RamazanBozkurrtt/circuitBuilderAi-Astra/docs/phases/phase_3g_remaining_schematic_implementation_preflight.md

# PHASE 3G — Remaining schematic implementation preflight

Date: 2026-09-14

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

## 1. Evidence used

Evidence IDs are from the [component evidence index](../evidence/component_evidence_index.md).

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

## 2. Phase 4C blocker disposition

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

## 3. Corrected microphone-to-ADC contract

### 3.1 Physical microphone ownership and polarity

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

### 3.2 Exact microphone-boundary isolation

Use four exact `TMUX1574PWR` TSSOP-16 packages:

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

The corrected isolation population is therefore:

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

### 3.3 Isolation electrical checks

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

### 3.4 Corrected VREF/common-mode path

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

### 3.5 Exact AFE topology and parts

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

For every `MICn_[P/N]_ISO` leg:

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

### 3.6 Worst-case range and headroom

The complete full-band screen uses the direction that maximizes amplitude:

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

Calculations:

`Vin,1k = 10^(-37/20) x 10^(26/20) = 0.281838 Vrms differential`

`Vin,max-band = 0.281838 x 10^(9/20) = 0.794328 Vrms differential`

`VADC,max-band = 0.794328 x 1.454479 = 1.155334 Vrms differential`

`Vleg,pk = 1.155334 / sqrt(2) = 0.816945 V`

`VOUT,min = 1.47 - 0.816945 - 0.002 = 0.651055 V`

`VOUT,max = 1.54 + 0.816945 + 0.002 = 2.358945 V`

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

## 4. Remaining-sheet implementation preflight

### 4.1 Sheet 3 — microphones / AFE

| Audit item | Frozen implementation | Result |
| --- | --- | --- |
| Channel/conductor count | Four differential channels, eight independently named legs; `P` and `N` never share a switch channel. | PASS |
| Isolation count/location | Microphone and AFE/ADC isolation devices are on Sheet 2. Sheet 3 receives eight `MICn_[P/N]_ISO` and returns eight `AFEn_[P/N]_RAW`. | PASS |
| Gain/headroom/common mode | Exact OPAx192 population, 1.453571 nominal gain and OPA320/OPA2192 VCM chain in §3. | PASS |
| LF corner | 4.7 uF nominal, >=2.2 uF effective, 100 kohm; 0.339/0.723 Hz. | PASS |
| Load/stability | `Rg+Rf>=4.066 kohm` and matched 47.0-ohm output isolation; Sheet 4 owns the balanced 1 nF C0G differential ADC capacitors. Macromodel/noise/CMRR tests retained. | PASS for schematic |
| Noise-critical resistors | 100 kohm bias, 2.80 kohm Rg, 1.27 kohm Rf, all 0.1% thin-film; 47 ohm output and Sheet 7 100 ohm RF resistors matched within each pair. | PASS |
| Power-off behavior | Paired-domain powered-off switches; no direct VREF or charged output path across an absent rail. | PASS |
| ADC interface | Eight outputs map one-to-one and polarity-correct to ADAU1978 AIN1-4. | PASS |
| Sheet 3 hierarchy count | **18 scalar pins:** eight mic inputs, eight AFE outputs, `AFE_VCM_ISO`, and `5V_AFE`. Ground is a global power net; no microphone connector is instantiated here. | PASS |

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

### 4.2 Sheet 4 — ADAU1978 ADC

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

### 4.3 Sheet 5 — ADSP-21569 DSP / boot / debug / clocks

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

The resource allocation is frozen and conflict-free:

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

### 4.4 Sheet 6 — TAS6424E-Q1 amplifier

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

### 4.5 Sheet 7 — connectors / system interfaces

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

## 5. Cross-sheet hierarchy inventory

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

| Source | Destination | Signal bundle | Direction | Count |
| --- | --- | --- | --- | ---: |
| Sheet 7 | Sheet 2 | `MIC1..4_[P/N]_RAW` after edge protection/100 ohms | 7 -> 2 | 8 |
| Sheet 2 | Sheet 3 | `MIC1..4_[P/N]_ISO` | 2 -> 3 | 8 |
| Sheet 3 | Sheet 2 | `AFE1..4_[P/N]_RAW` | 3 -> 2 | 8 |
| Sheet 2 | Sheet 4 | `ADC1..4_[P/N]_ISO` | 2 -> 4 | 8 |
| Sheet 4 | Sheet 2 | `ADC_VREF_RAW` | 4 -> 2 | 1 |
| Sheet 2 | Sheet 3 | `AFE_VCM_ISO` | 2 -> 3 | 1 |
| Sheet 2 | Sheets 3/4/5/6/7 | Frozen rails and enables: 5V AFE; 3V3 ADC; DSP rails; 3V3 SYS; 12V protected; 2V8 MIC | 2 -> loads | 8 named rails plus returns |
| Sheet 5 | Sheet 4 | ADC MCLK, BCLK, FSYNC | 5 -> 4 | 3 |
| Sheet 4 | Sheet 5 | ADC TDM data | 4 -> 5 | 1 |
| Sheet 5 | Sheet 6 | amplifier MCLK, SCLK, FSYNC, TDM data | 5 -> 6 | 4 |
| Sheet 5 | Sheets 4/6 | shared SDA, SCL | bidirectional | 2 |
| Sheet 5 | Sheet 2 | six retained-domain commands, MUTE command, STANDBY command, ADC reset-release command, WDI | 5 -> 2 | 10 |
| Sheet 2 | Sheet 5 | `RAILS_OK`, `SYS_HWRST` (dedicated reset, not GPIO) | 2 -> 5 | 2 |
| Sheet 6 | Sheets 2/5 | `AMP_FAULT_N` fanout | 6 -> 2 and 5 | 1 source, 2 sinks |
| Sheet 6 | Sheet 5 | `AMP_WARN_N` | 6 -> 5 | 1 |
| Sheet 6 | Sheet 7 | four filtered BTL `SPKn+/-` pairs | 6 -> 7 | 8 |
| Sheet 5 | Sheet 7 | UART TX/RX/RTS/CTS | mixed | 4 |
| Sheet 5 | Sheet 7 | JTAG TMS/TCK/TDO/TRST/TDI | mixed | 5 |
| Sheet 2 | Sheet 7 | common `SYS_HWRST` branch to JTAG reset contact | 2 -> 7 | 1 |
| Sheet 5 | Sheet 7 | optional service SDA/SCL | bidirectional | 2 |

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

## 6. Remaining non-architectural validation

The following are explicitly **physical-validation items**, not choices left to Astra:

- SPICE/macromodel DC, AC, noise, stability, CMRR and overload recovery for the exact OPA320/OPAx192/switch/ADC network at rail, resistor, temperature and microphone corners.
- Extracted plus measured microphone `Ca`, `Cb`, and `Cd`, each <=100 pF with the production cable/module.
- ADC full-scale/clipping onset because 2 Vrms is published as typical, plus complete channel gain/phase matching.
- ADC data hold timing using exact IBIS/trace extraction and the already frozen >=3 ns measured acceptance criterion.
- DSP rail transient/PI and BGA escape review; decoupling may be augmented within the frozen regulator limits.
- Exact amplifier inductor part, saturation/DCR/temperature, EMI filter optimization, heatsink/interface, load diagnostics and conducted/radiated emissions.
- Exact production connector series, creepage/mechanics, mating-cycle and cable strain relief.

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

## 7. Controlled implementation order

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

## 8. Gate

Both Phase 4C blockers are resolved. Every remaining sheet has a fixed component/interface/safe-state contract, the four-channel DSP resource map has no collision, connector counts include required returns/shields, and the remaining unknowns are physical validation or mechanical procurement items rather than schematic-architecture blockers.

PHASE 3G: PASS
