RamazanBozkurrtt/circuitBuilderAi-Astra/docs/product/ANC_B2B_Custom_PCB_2_Kart_Mimari_Tasarim_Dokumani_v1.0.docx

ANC B2B CUSTOM PCB

İki Kartlı Ürün Mimarisi
ve Tasarım Gereksinimleri

Controller + Audio AFE / Power + Stereo Class-D

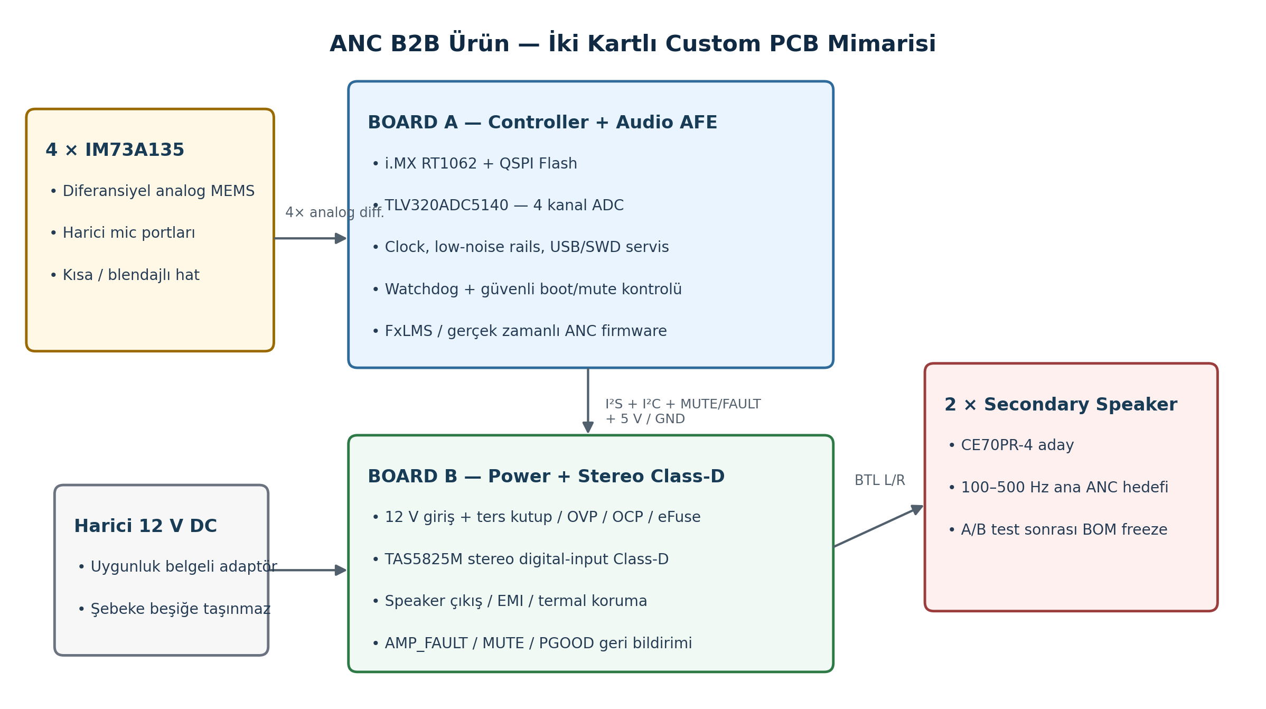
[picture p1: figure]

Doküman statüsü — Bu belge üretim dosyası değildir. Şema/PCB tasarımını yönetecek sistem mimarisi, güvenlik, arayüz, DFM ve doğrulama gereksinimlerini dondurmak için hazırlanmış taslak tasarım girdisidir.

Sürüm: v1.0 Draft | Tarih: 26 Eylül 2026 | Hedef: B2B gömülü ANC modülü

# 1. Amaç, kapsam ve ürün sınırı

Bu dokümanın amacı, mevcut Teensy 4.1 + iki Audio Shield + ayrı Class-D amplifier kartlarıyla kurulan PoC mimarisini, seri üretime uygun iki parçalı custom PCB platformuna dönüştürmek için teknik gereksinimleri tanımlamaktır.

Hedef, PoC kartlarını PCB üzerinde birebir kopyalamak değildir. Hazır geliştirme kartlarının yalnızca ürün için gerekli işlevleri korunur; microSD, headphone jack, kullanıcı potansiyometreleri, geliştirme amaçlı geniş header alanları ve final B2B ürününde kullanılmayan test çıkışları kaldırılır.

Ana ürün kararı — v1 ürün iki karttan oluşacaktır: Board A = Controller + Audio AFE; Board B = Power + Stereo Class-D. Dört mikrofon giriş kanalı ve iki secondary speaker çıkışı korunur. Ürünün ilk ticari odağı B2B gömülü entegrasyondur.

Kaynak proje belgeleri

- ANC_PoC_FINAL_Rev2(1).docx — mevcut PoC kanal planı, güç ve bring-up baseline.
- ANC_Ürünleşme_Sertifikasyon_Doküman.docx — güç, EMC, akustik emniyet, EVT/DVT/PVT ve teknik dosya gereksinimleri.
- ANC_Besik_Kompakt_Hoparlor_Adaylari_Arastirma_Raporu(1).docx — kompakt secondary speaker seçimi ve A/B test planı.
- ANC_Besik_Potansiyel_Musteri_Analizi_2026-09-16(1).docx — B2B gömülü ürün yaklaşımının ticari bağlamı.

1.1 Dondurulan ve açık bırakılan kararlar

Konu | Durum | v1 kararı | Not
Mimari | DONDURULDU | 2 kartlı stack | AFE/digital ile Class-D/power fiziksel olarak ayrılır.
Mikrofon | HEDEF | 4 × IM73A135 | Analog diferansiyel; exact input network şema aşamasında doğrulanır.
ADC | HEDEF | TLV320ADC5140 | 4 analog kanal, TDM/I²S; düşük gecikme ayarı doğrulanır.
MCU/DSP | HEDEF | i.MX RT1062 | Teensy 4.1 işlevlerinin gerekli kısmı doğrudan MCU üzerinde.
Amplifier | HEDEF | TAS5825M | 2 kanal digital-input Class-D; 12 V performansı EVT’de doğrulanır.
Speaker | ADAY | 2 × Dayton CE70PR-4 | Seri BOM, gerçek beşik A/B testinden sonra dondurulur.
Kablosuz | v1 DIŞI | Yok | RED kapsamını ve maliyeti gereksiz büyütmemek için.
microSD / headphone | KALDIRILDI | Yok | Ürün işlevi değil.
Boot/update | AÇIK | Kendi production flow’u tercih | Teensy uyumluluğu otomatik değildir; ayrıca kararlaştırılmalı.

# 2. Sistem mimarisi

Şekil 1 — Önerilen ürün mimarisi. Board A düşük seviyeli analog ve DSP işlerini; Board B yüksek akım, giriş koruması ve speaker sürüşünü taşır.

2.1 Ürün sinyal zinciri

4 × IM73A135 → analog diferansiyel giriş → TLV320ADC5140 → TDM/I²S → i.MX RT1062 / FxLMS → stereo I²S → TAS5825M → 2 × secondary speaker

- PoC’de kullanılan MAX4466 modülleri final üründe kaldırılır. Mikrofon kapsülleri doğrudan ürün AFE’sine bağlanır.
- PoC’deki iki SGTL5000 / iki Audio Shield kaldırılır. Dört giriş için tek çok kanallı ADC kullanılır.
- Digital-input Class-D kullanıldığı için ürün zincirinde ayrı bir stereo DAC zorunlu değildir.
- PoC’deki primary/noise speaker ve spare output final B2B cihaz işlevi değildir; üretim BOM’una eklenmez.
- Dört mikrofonun reference/error/monitoring rolleri mekanik geometri ve algoritma testleriyle atanacaktır; PCB dört eşdeğer giriş kanalı sağlar.

2.2 Fonksiyonel hedefler

Fonksiyon | v1 hedefi | Tasarım sonucu
Mikrofon girişleri | 4 eşzamanlı kanal | Tek ADC, kanal başına eşlenebilir gain/calibration.
Speaker çıkışları | 2 secondary kanal | Tek stereo Class-D.
ANC işleme | Düşük gecikmeli gerçek zamanlı FxLMS | RT1062 üzerinde production firmware.
Programlama/servis | Fabrika ve servis erişimi | USB/SWD/test pad; tüketiciye açık arayüz olmak zorunda değil.
Güvenli durum | Arıza / reset / boot sırasında mute | Hardware mute + watchdog + firmware state machine.
Güç | Harici düşük gerilim DC | Beşik içinde şebeke yok; giriş Board B’de korunur.

# 3. Board A — Controller + Audio AFE

Board A sistemin hassas tarafıdır. Mikrofon analog yolları, ADC, RT1062, flash, clock, servis/debug ve güvenli kontrol mantığı bu kartta bulunur. Class-D güç akımlarından fiziksel olarak uzak tutulur.

3.1 Zorunlu bloklar

- i.MX RT1062 MCU/DSP: mevcut Teensy 4.1 tabanlı gerçek zamanlı ANC algoritmasının üretim platformu.
- Harici QSPI NOR Flash: boot/application image ve gerekirse kalibrasyon verisi.
- TLV320ADC5140: dört analog mikrofon kanalının eşzamanlı örneklenmesi; TDM/I²S ile MCU bağlantısı.
- 4 × IM73A135 giriş portu: diferansiyel mikrofon hatları, ESD/EMI yaklaşımı ve gerekli AC-coupling/bias network.
- Düşük gürültülü analog besleme ve ayrı dijital regülasyon/filtreleme.
- Clock/reset/boot strap devresi; production boot ve recovery yolu.
- Hardware watchdog; amplifier MUTE/ENABLE hattını güvenli durumda zorlayabilecek fail-safe kontrol.
- USB servis/programlama ve SWD/JTAG test padleri; production pogo fixture ile erişilebilirlik.
- Kart kimliği / revision / seri numarası için EEPROM gerekmiyorsa flash alanı kullanılabilir; gereksiz IC eklenmez.

Mikrofon AFE notu — IM73A135 diferansiyel analog çıkışlıdır. TLV320ADC5140 analog/diferansiyel giriş destekler; ancak coupling, common-mode, gain, bias, headroom ve anti-alias network değerleri iki parçanın datasheet/referans devreleri birlikte incelenerek şema aşamasında doğrulanacaktır. Bu doküman o değerleri dondurmaz.

3.2 Board A PCB hedefi

Başlık | Öneri / gereksinim
Katman | Başlangıç hedefi 6 layer. EVT sonrası DFM/EMC sonucu uygunsa 4 layer cost-down değerlendirilebilir.
Yerleşim | Mic AFE + ADC bölgesi, RT1062/flash/clock bölgesinden ve board-to-board power girişinden ayrılır.
Ground | Kesintisiz referans plane; analog/digital dönüş yolları geometrik olarak yönetilir, keyfi split ground yapılmaz.
High-speed | QSPI, USB ve clock hatları kontrollü ve kısa; BGA breakout üretici DFM kurallarına göre.
Test | Tüm rail, reset, boot, SWD, I²C ve kritik audio clock hatlarında erişilebilir test noktası.
EMC | Harici mic connector girişinde ESD/filtre footprintleri; pre-scan için DNP opsiyonları.

# 4. Board B — Power + Stereo Class-D

Board B yüksek akım ve switching enerjisinin bulunduğu karttır. 12 V ürün girişi, primer koruma, logic rail üretimi ve stereo speaker amplifier aynı kartta tutulur. Board A’ya temiz ve kontrol edilmiş besleme sağlanır.

4.1 Zorunlu bloklar

- 12 V DC giriş konektörü ve doğru akım kapasitesine sahip kablo/harness arayüzü.
- Ters kutup koruması, aşırı gerilim, aşırı akım/kısa devre ve eFuse/elektronik sigorta yaklaşımı.
- 12 V → 5 V yüksek verimli buck; Board A üzerinde gerekli düşük gürültülü LDO’larla nihai rail üretimi.
- TAS5825M stereo digital-input Class-D amplifier; I²S audio ve I²C kontrol.
- Hardware MUTE/ENABLE; MCU arızasında varsayılan mute olacak pull-up/pull-down mantığı.
- AMP_FAULT / thermal / PGOOD geri bildirimleri Board A’ya taşınır.
- Speaker output connectorları, BTL topolojisine uygun; eksi uçlar GND olarak etiketlenmez.
- EMI/output network ve bulk decoupling footprintleri; ölçüm sonrası optimize edilebilir.

4.2 Board B PCB hedefi

Başlık | Öneri / gereksinim
Katman | 4 layer başlangıç hedefi; power/ground plane ve Class-D dönüş yolları için tercih edilir.
Akım döngüleri | PVDD decoupling, half-bridge ve speaker akım döngüleri çok kısa tutulur.
Termal | Exposed pad / thermal via / copper area datasheet’e göre; kapalı muhafaza worst-case test edilir.
Connector | 12 V giriş ve speaker çıkışları mic/AFE yönünün ters tarafına yerleştirilir.
Koruma | Input TVS/eFuse/OVP/OCP ve ESD parçaları konektöre yakın.
Servis | Rail, current sense/PGOOD, amplifier fault ve mute hatlarında test point.

12 V karar kapısı — İlk ürün 12 V hedefiyle tasarlanır; ancak CE70PR-4 ile gerçek beşik geometrisinde gerekli Vrms/Irms, THD ve ANC headroom ölçülmeden besleme kesin dondurulmaz. 24 V’a geçiş yalnız ölçüm ihtiyacı gösterirse değerlendirilir.

# 5. Board-to-board arayüzü ve stack konsepti

İki kartın fiziksel ayrımı yalnız servis kolaylığı için değil, EMC ve analog performans için de kullanılır. Board B’nin Class-D ve DC/DC switching bölgesi Board A mikrofon/ADC tarafının altına doğrudan denk getirilmemelidir.

5.1 Önerilen arayüz sinyalleri

Grup | Sinyaller | Yön | Not
Güç | 5 V, GND × çoklu pin | B → A | Akım ve ground dönüşü için birden fazla pin.
Audio | BCLK, LRCLK, SDOUT, opsiyonel MCLK | A → B | Stereo I²S; exact pinout şema freeze ile.
Control | I²C SDA/SCL | Çift yön | Amplifier configuration / status.
Safety | AMP_MUTE, AMP_FAULT, PGOOD | A↔B | Fail-safe logic seviyeleri güç yokken de tanımlı.
Service | Revision detect / spare GPIO | Çift yön | DNP/gelecek opsiyon; minimum tutulur.

5.2 Mekanik başlangıç hedefi

- Kart boyutları beşik geometrisi görülmeden dondurulmaz. İlk ECAD hedefi aynı dış zarfı paylaşan iki kompakt karttır.
- Board-to-board mezzanine connector; yanlış yönde takmayı fiziksel olarak engelleyen keying tercih edilir.
- Başlangıç stack mesafesi 10–15 mm sınıfında planlanır; en yüksek komponent ve termal hava ihtiyacıyla doğrulanır.
- Mic connectorları Board A’nın bir kenarında, power/speaker connectorları Board B’nin karşı kenarında gruplanır.
- Montaj deliği/standoff düzeni iki kartta ortak datum kullanır; beşik üreticisinin plastik/ahşap taşıyıcısına aktarılabilir.

# 6. Güvenlik ve EMC gereksinimleri

Bu bölüm maliyet düşürmek için kaldırılamayacak gereksinimleri özetler. Bebek ürünü bağlamında DSP yazılımı tek güvenlik katmanı olarak kabul edilmez.

Risk | Donanım / firmware önlemi | Doğrulama
Kontrol kararsızlığı / yüksek SPL | Hardware mute, sabit gain/power sınırı, watchdog, controlled startup | Full-scale ve kararsızlık fault injection + peak/süre ölçümü.
Mic kopuk/kısa/doygun | ADC validity check + anında safe state | Open/short/reverse/clip testleri.
Amplifier/power arızası | eFuse/OCP/OVP, amp thermal/fault, mute | Short-circuit, overload, thermal single-fault.
EMC ile yanlış çıkış | ESD/EMI filtreleme + immunity sırasında fault→mute | Pre-scan + immunity sırasında eşzamanlı audio izleme.
Yanlış adaptör / reset | Input protection, brownout/PGOOD, silent boot | Gerilim sweep, kesinti, hızlı power-cycle.
Kablo/connector | Locking connector, strain relief, BTL işaretleme | Pull test ve yanlış bağlantı senaryoları.

EMC yerleşim kuralları

- Clock/QSPI/USB ve Class-D switching akım döngüleri mic inputlardan uzak tutulur.
- Board A ve Board B arasında ground dönüşü düşük empedanslı ve öngörülebilir olmalıdır; sinyal dönüşleri connector üzerinden kopuk bırakılmaz.
- Harici mic ve power/speaker kabloları pre-scan testinde en kötü gerçek uzunlukla değerlendirilir.
- Ferrite/RC/common-mode filtre için ölçüm sonrası populate edilebilecek DNP footprint alanları planlanır.
- Debug/test konnektörleri final ürün EMI antenine dönüşmeyecek biçimde üretim sonrasında erişim kontrolüyle ele alınır.

# 7. Firmware, boot ve ürün davranışı

RT1062 kullanmak, Teensy 4.1 kartını PCB üzerinde kopyalamak anlamına gelmez. MCU, flash, reset/boot ve programlama zinciri ürün için ayrıca tasarlanır. Teensy uyumluluğu istenirse bootloader/lisans/ek bileşen kararı ayrı bir üretim kararıdır.

7.1 Production firmware state machine

Durum | Davranış
POWER_OFF | Amplifier fiziksel olarak mute/disabled.
BOOT_SAFE | Rail/clock/flash/ADC/amp iletişimi doğrulanır; speaker sessiz.
SELF_TEST | Mic kanal validity, fault pinleri, calibration CRC ve temel limitler kontrol edilir.
READY | ANC enable edilebilir; soft-start uygulanır.
ANC_ACTIVE | Watchdog ve audio health sürekli izlenir.
FAULT_MUTE | Her kritik fault’ta amp mute; otomatik restart yalnız tanımlı policy ile.

7.2 Güncelleme yaklaşımı

- v1 B2B üründe Wi-Fi/Bluetooth OTA zorunlu değildir.
- Factory flashing pogo/SWD veya USB üzerinden yapılır.
- Firmware version, board revision ve calibration version üretim kaydına bağlanır.
- Field update gerekiyorsa yetkili servis/üretici prosedürü tanımlanır; rastgele son kullanıcı update akışı ilk sürümde şart değildir.

# 8. Üretilebilirlik (DFM/DFA) ve 400 adet/yıl planı

Ticari hedef 400 adet/yıl olduğunda üretim dört release halinde 100 + 100 + 100 + 100 yapılabilir. Ancak fiyat avantajını korumak için üreticiyle yıllık hacim taahhütlü blanket order / scheduled release modeli müzakere edilmelidir.

8.1 PCB üretim paketi

- Gerber/ODB++ veya üreticinin tercih ettiği fabrication package.
- BOM: manufacturer + MPN + approved alternate + DNP + lifecycle status.
- CPL / pick-and-place, centroid, rotation doğrulaması.
- Assembly drawing, polarity, critical component notes.
- Stack-up, impedance note, via/finish ve BGA escape gereksinimleri.
- Panelization/fiducial/tooling hole kuralları assembly house ile birlikte dondurulur.
- Programming/test fixture mekanik çizimi ve pogo test-point map.

8.2 Üretim kalite kontrolü

- RT1062 BGA ve QFN/thermal pad komponentler için ilk lotta X-ray inspection.
- AOI + görsel kalite standardı; tombstone, polarity ve solder void riskleri için process feedback.
- Her board setine lot/serial kimliği.
- Approved alternate kullanımı yalnız BOM change control ile.
- RoHS/material declaration ve kritik komponent CoC dokümanları teknik dosyada saklanır.

# 9. Factory EOL test planı

Her ürün seti yalnız “çalışıyor” kontrolüyle değil, otomatik veya yarı otomatik EOL fixture ile temel güvenlik ve kanal fonksiyonlarından geçmelidir.

Test | Yöntem | PASS kriteri | Kayıt
Rail/idle current | Fixture ölçümü | 5 V/3.3 V tolerans içinde, anormal idle yok | V/I
MCU/Flash | Program + CRC | Boot OK, firmware checksum PASS | FW rev/CRC
ADC/I²C | Device ID/config | 4 kanal erişilebilir | PASS/FAIL
Mic channel | Known acoustic/electrical stimulus | Gain/noise/channel map limit içinde | 4ch değer
I²S amp | Digital test tone | L/R doğru kanal, mute çalışıyor | PASS/FAIL
Speaker output | Dummy load veya controlled speaker fixture | Amplitude/THD/fault normal | L/R değer
Watchdog/mute | Fault injection | Belirlenen sürede sessiz duruma geçiş | ms + status
Serial trace | QR/serial scan | Board A/B eşleşmesi kayıtlı | Serial pair

# 10. EVT → DVT → PVT doğrulama planı

Resmi uygunluk testine production tasarımı dondurulmadan girilmez. Önce elektrik/akustik riskleri kapatan mühendislik iterasyonları tamamlanır.

Aşama | Önerilen adet | Ana iş | Çıkış koşulu
EVT-0 | 5–10 set | Power-up, RT1062 boot, ADC 4ch, I²S amp, basic audio loop | Schematic/layout kritik hataları kapanır.
EVT-1 | 10–20 set | Latency, noise floor, thermal, fault/mute, speaker A/B | CE70PR-4/SLS-65 kararı ve power headroom.
PCB v2 / DVT | 20–30 set | EMC pre-scan, ESD, single-fault, full enclosure/crib integration | Design freeze candidate.
PVT | 50–100 set | Gerçek üretim hattı, EOL fixture, yield ve traceability | 400/yıl release planına geçiş.
Production | 100 × 4 release | Blanket order / scheduled build | Her lot EOL + change control.

# 11. Maliyet hedefi ve cost-down sınırı

Aşağıdaki rakamlar tedarikçi teklifi değil, proje hedef zarfıdır. 400 ürün/yıl ve parçaların yıllık hacim üzerinden fiyatlanması varsayımıyla kullanılmalıdır.

Kapsam | Hedef maliyet | Not
2-board assembled PCB set | ~1.700–2.100 TL / ürün | MCU+ADC+amp+power/safety+PCB/SMT; RFQ ile doğrulanır.
4 mic + 2 speaker + harness dahil embedded set | ~3.400–3.700 TL / ürün | 400/yıl optimize hedef; lojistik/garanti koşuluna göre değişir.
Ticari planlama maliyeti | ~4.000 TL / ürün | Garanti/yield/lojistik/finansman tamponu için güvenli planlama rakamı.

Cost-down kuralı — microSD, headphone, potansiyometre, ikinci gereksiz codec, ayrı DAC, development header ve PoC’ye özel primary speaker çıkışı kaldırılır. Buna karşılık eFuse/OVP/OCP, watchdog, mute, ESD/EMI ve EOL test gibi güvenlik/üretim öğeleri cost-down için kaldırılmaz.

# 12. Açık kararlar / tasarım başlamadan kapanması gerekenler

# | Açık karar | Kapanma kriteri

1 | IM73A135 → TLV320ADC5140 exact analog input network | Schematic freeze öncesi bench/reference-circuit validation.
2 | RT1062 boot/programming modeli | Kendi production boot/update flow’u mu, Teensy uyumluluğu mu?
3 | CE70PR-4 vs SLS-65 | Gerçek beşik A/B testi: 80/100/125/160/250/500/800 Hz, THD, excursion, Vrms/Irms.
4 | 12 V amplifier headroom | CE70PR-4 ile hedef attenuation için yeterli mi? Ölçümle dondur.
5 | Board boyutu ve connector | Beşik üreticisinin mekanik hacmi ve kablo rotası geldikten sonra.
6 | Mic role / placement | 4 kanalın reference/error/monitoring dağılımı akustik geometriyle.
7 | Safety SPL acceptance criteria | Bağımsız akustik uzman/lab ile satış öncesi yazılı limit/test metodu.

12.1 İlk PCB tasarım sprinti için önerilen çıktı

- System schematic review: Board A ve Board B sheet breakdown.
- Power tree + reset/boot sequencing diagram.
- 4-channel microphone AFE simulation / bench validation note.
- Board-to-board connector pin assignment v0.1.
- RT1062 pin mux / DMA / SAI / I²C resource map.
- Preliminary BOM + lifecycle + sourcing risk list.
- Placement floorplan before routing: AFE, MCU/flash, connector, DC/DC, Class-D, speaker outputs.
- EVT testpoint ve fixture requirements freeze.

# Ek A — Fonksiyonel preliminary BOM

Bu liste üretim BOM’u değildir; tasarım bloklarını netleştirmek için hazırlanmıştır. Exact MPN, package ve alternatifler schematic/DFM aşamasında dondurulacaktır.

Ref blok | Önerilen parça / sınıf | Adet | Kart | Durum
MCU | NXP i.MX RT1062 | 1 | A | Hedef
Flash | QSPI NOR, yeterli capacity | 1 | A | Açık MPN
Audio ADC | TI TLV320ADC5140 | 1 | A | Hedef
Microphone | Infineon IM73A135 | 4 | Harici / mic PCB | Hedef
Class-D | TI TAS5825M | 1 | B | Hedef
Secondary speaker | Dayton CE70PR-4 | 2 | Harici | A/B test adayı
Power protection | eFuse / OVP / reverse polarity / TVS | 1 set | B | Schematic seçimi açık
DC/DC | 12 V → 5 V buck | 1 | B | Açık MPN
Low-noise rails | LDO / filter network | 1 set | A | Açık MPN
Watchdog | Independent hardware watchdog veya equivalent safety path | 1 | A | Açık MPN
Board connector | Keyed mezzanine | 1 pair | A+B | Mekanik açık
Service | USB/SWD/pogo test interface | 1 set | A | Üretim gereksinimi

# Ek B — Teknik referanslar ve proje dayanakları

- TI TLV320ADC5140 product/data sheet: 4 analog ADC channel, TDM/I²S, programmable gain/low-latency options.
- TI TAS5825M product/data sheet: stereo digital-input Class-D, 4.5–26.4 V PVDD, integrated fault protections.
- Infineon IM73A135 product information: analog differential MEMS microphone.
- Project document: ANC_PoC_FINAL_Rev2(1).docx.
- Project document: ANC_Ürünleşme_Sertifikasyon_Doküman.docx.
- Project document: ANC_Besik_Kompakt_Hoparlor_Adaylari_Arastirma_Raporu(1).docx.

Final not — Bu dokümandan sonraki doğru adım doğrudan routing değildir. Önce Board A/Board B schematic sheet planı, power tree, boot strategy ve IM73A135→ADC input network dondurulmalı; ardından placement floorplan ve PCB layout’a geçilmelidir.

ANC B2B Custom PCB | Taslak v1.0 | 26.09.2026 •

ANC B2B Custom PCB — Two-Board Product Architecture
