RamazanBozkurrtt/circuitBuilderAi-Astra/datasheets/power/amass_xt30pw_spec_0.png

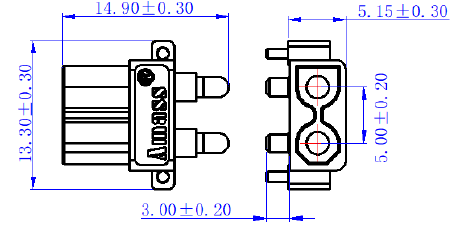
datasheets/power/amass_xt30pw_spec_0.png
