RamazanBozkurrtt/circuitBuilderAi-Astra/tmp/phase_1/ADC_8.png

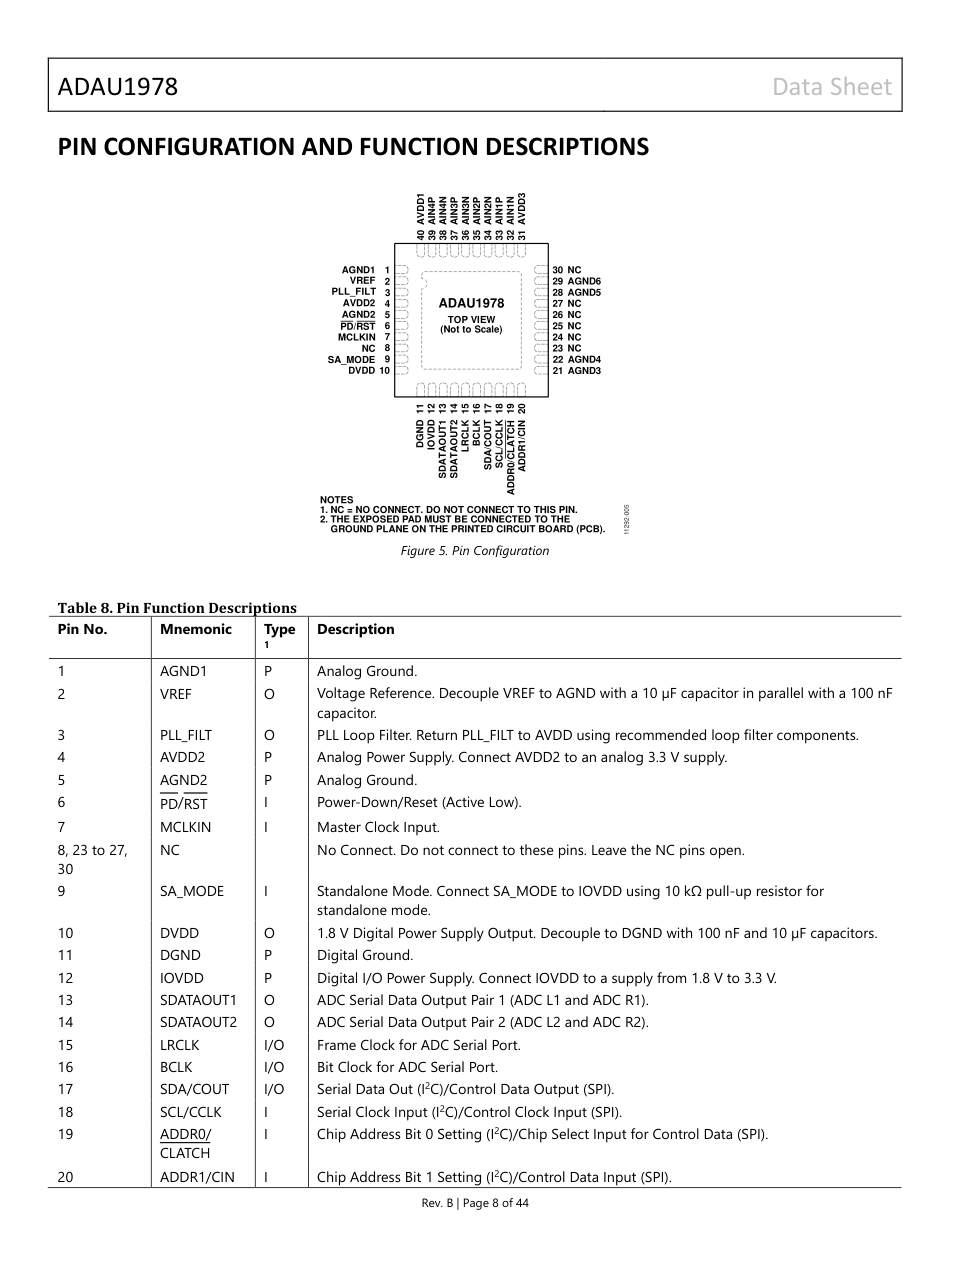
tmp/phase_1/ADC_8.png
