RamazanBozkurrtt/circuitBuilderAi-Astra/tmp/phase_1/ADC_18.png

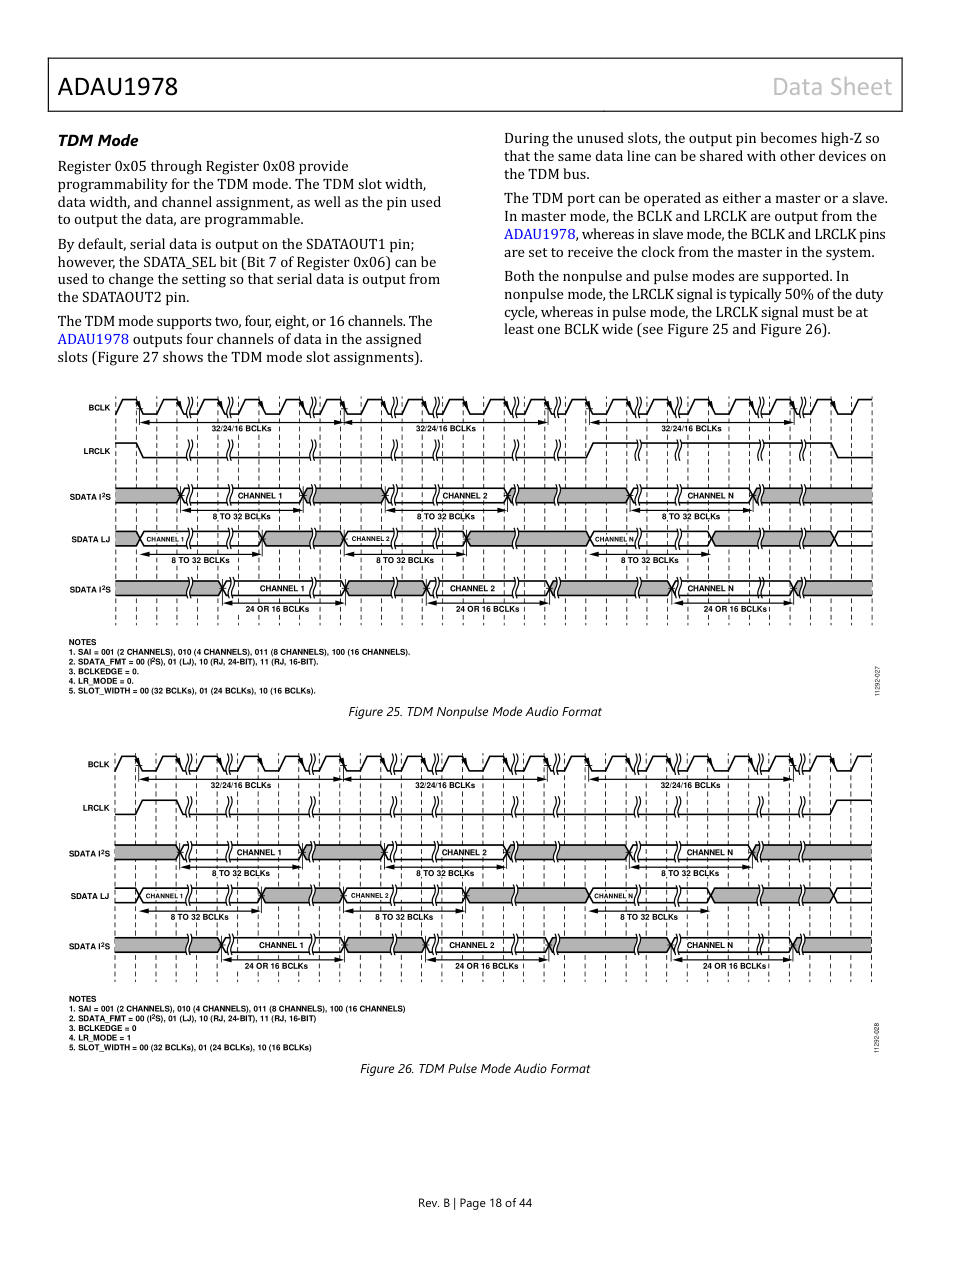
tmp/phase_1/ADC_18.png
