RamazanBozkurrtt/circuitBuilderAi-Astra/tmp/phase_1/ADC_43.png

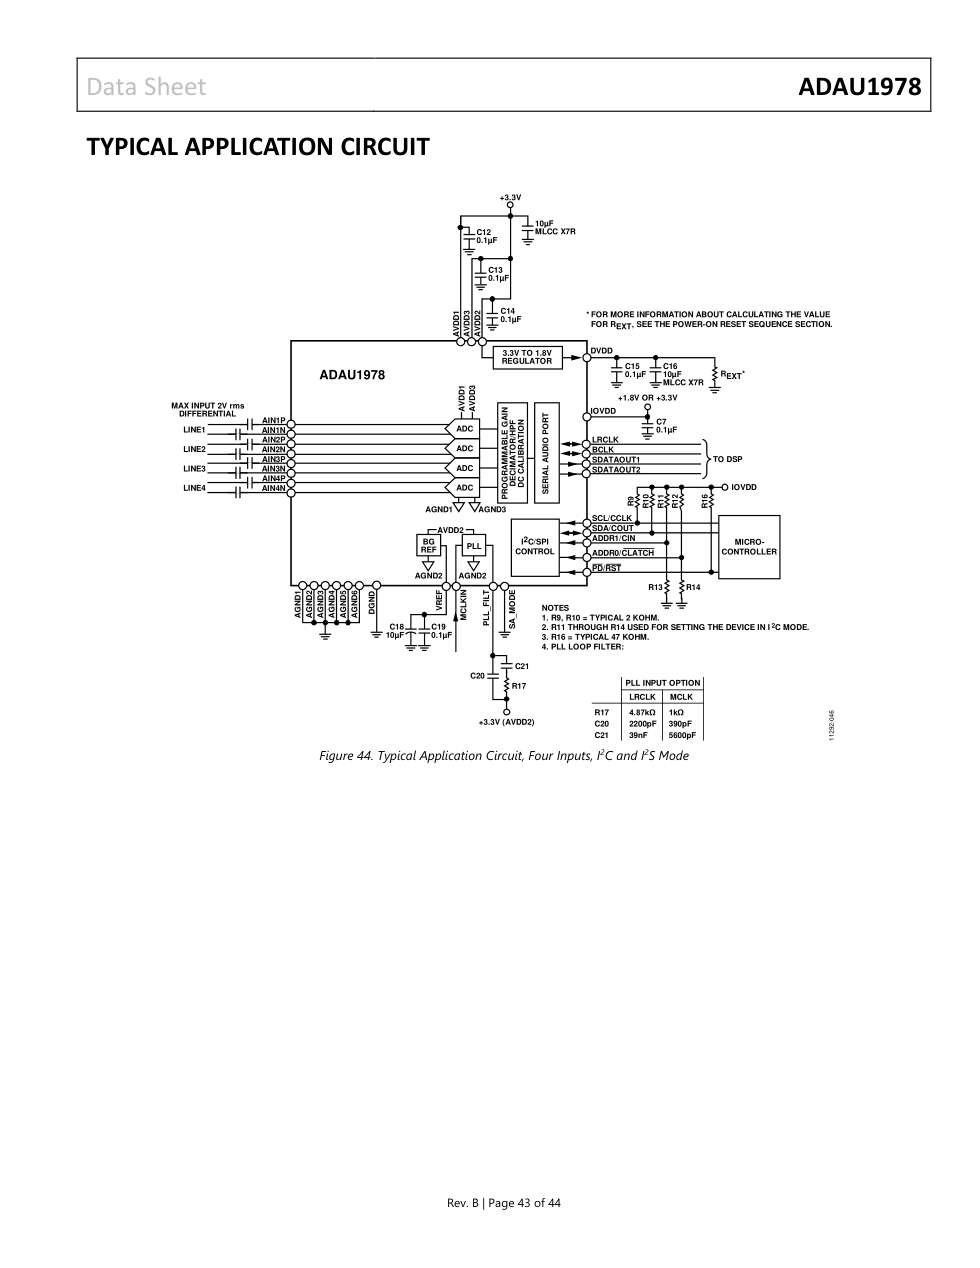
tmp/phase_1/ADC_43.png
