RamazanBozkurrtt/circuitBuilderAi-Astra/tmp/phase_1/ADCEVAL_10.png

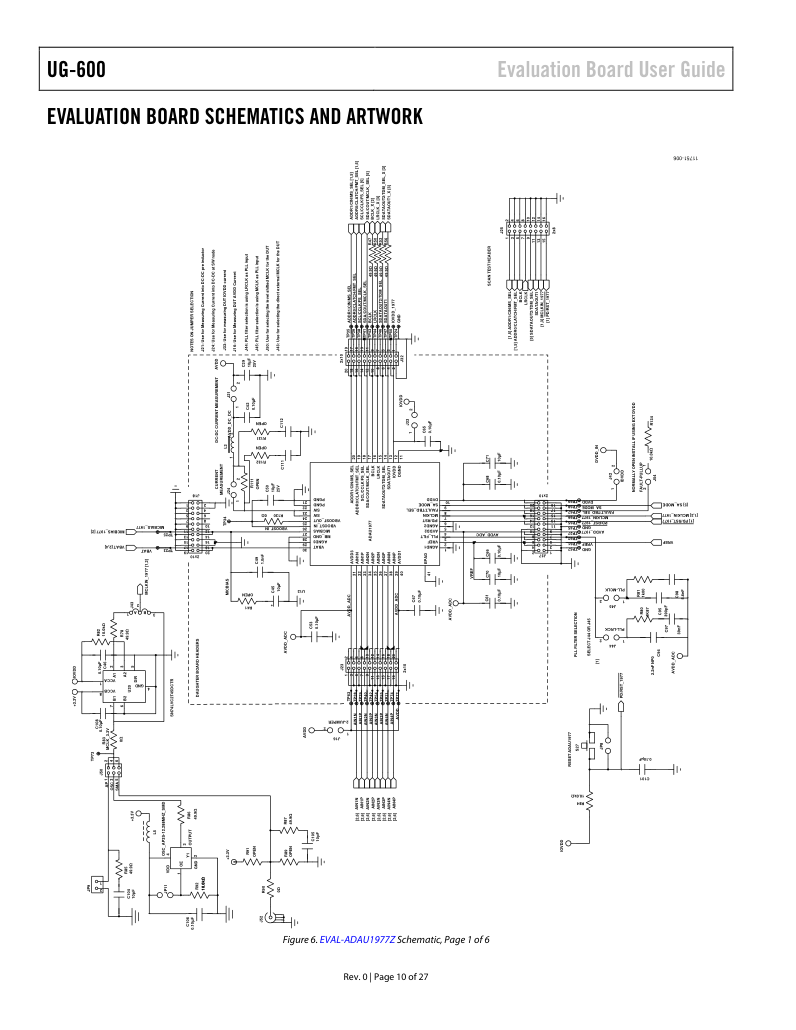
tmp/phase_1/ADCEVAL_10.png
