RamazanBozkurrtt/circuitBuilderAi-Astra/tmp/phase_1/ADCEVAL_11.png

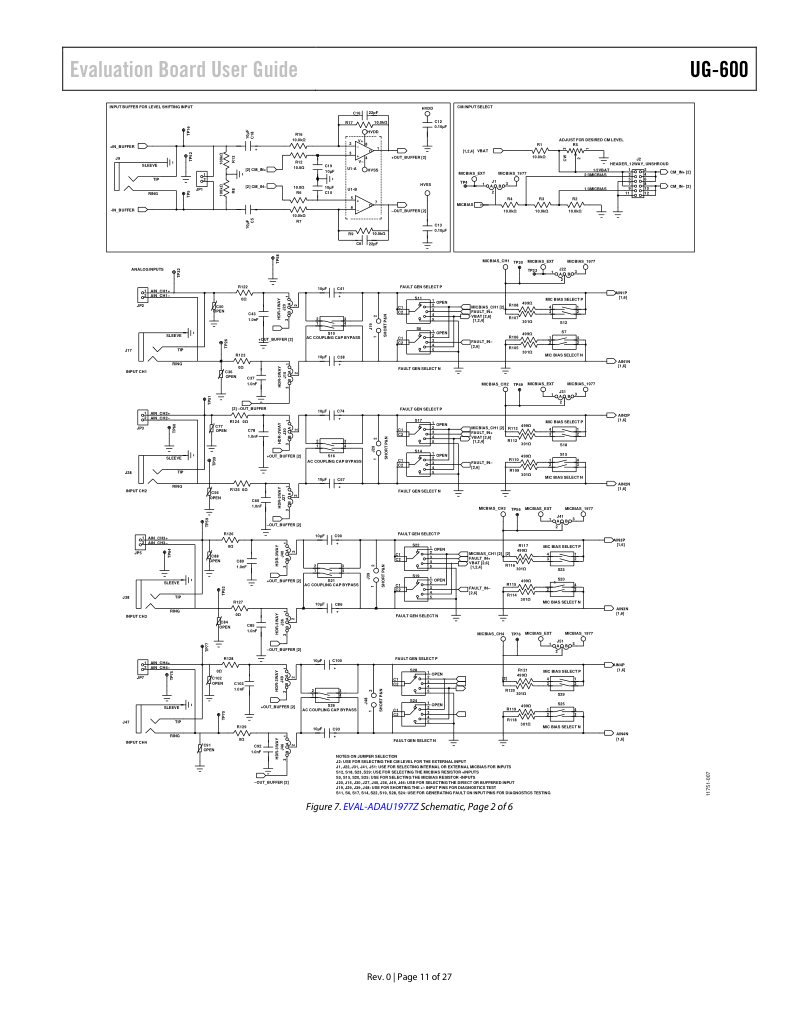
tmp/phase_1/ADCEVAL_11.png
