RamazanBozkurrtt/circuitBuilderAi-Astra/tmp/phase_1/AMP_4.png

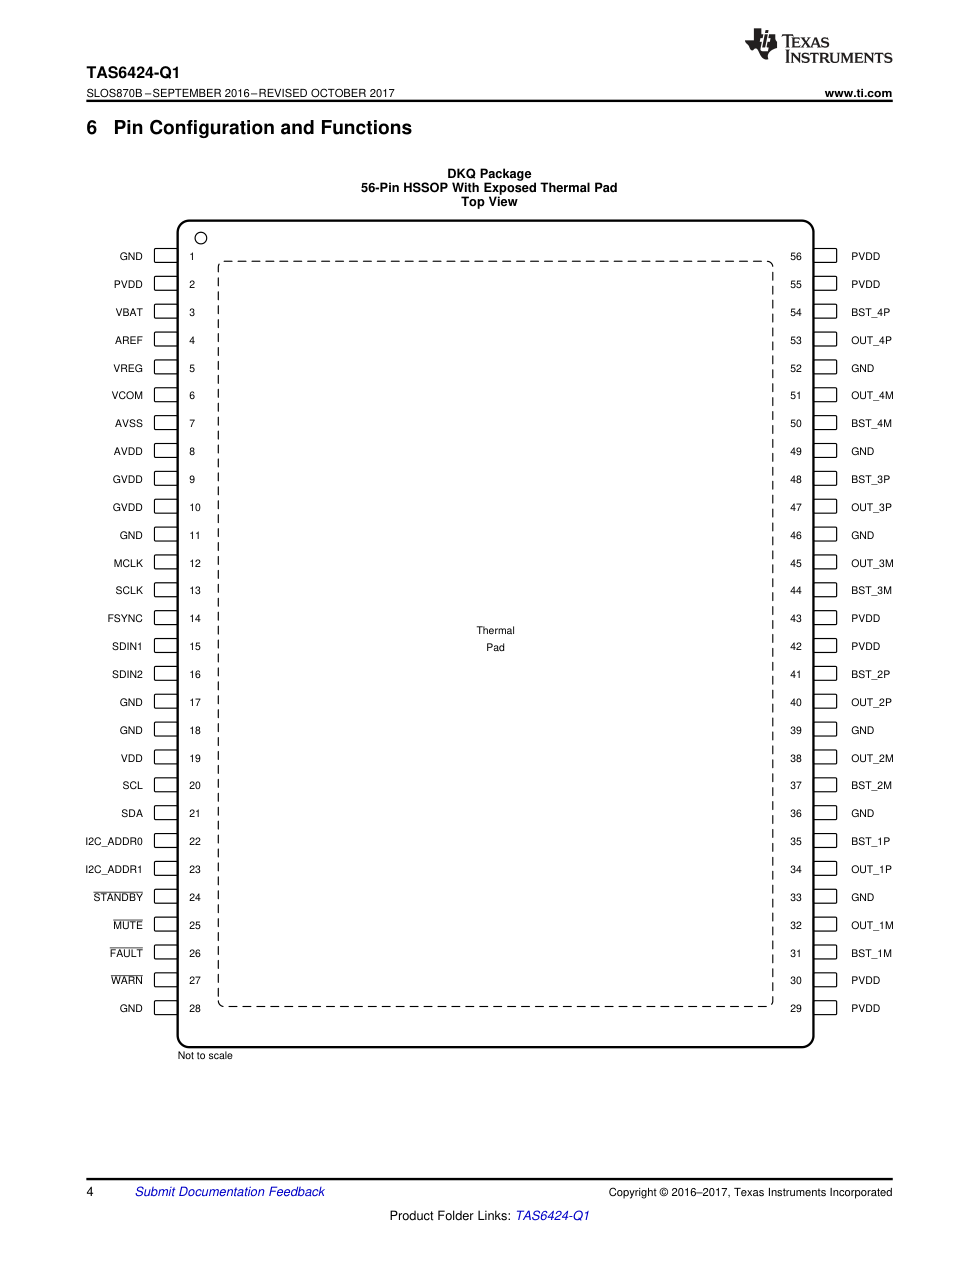
tmp/phase_1/AMP_4.png
