RamazanBozkurrtt/circuitBuilderAi-Astra/tmp/phase_1/AMP_19.png

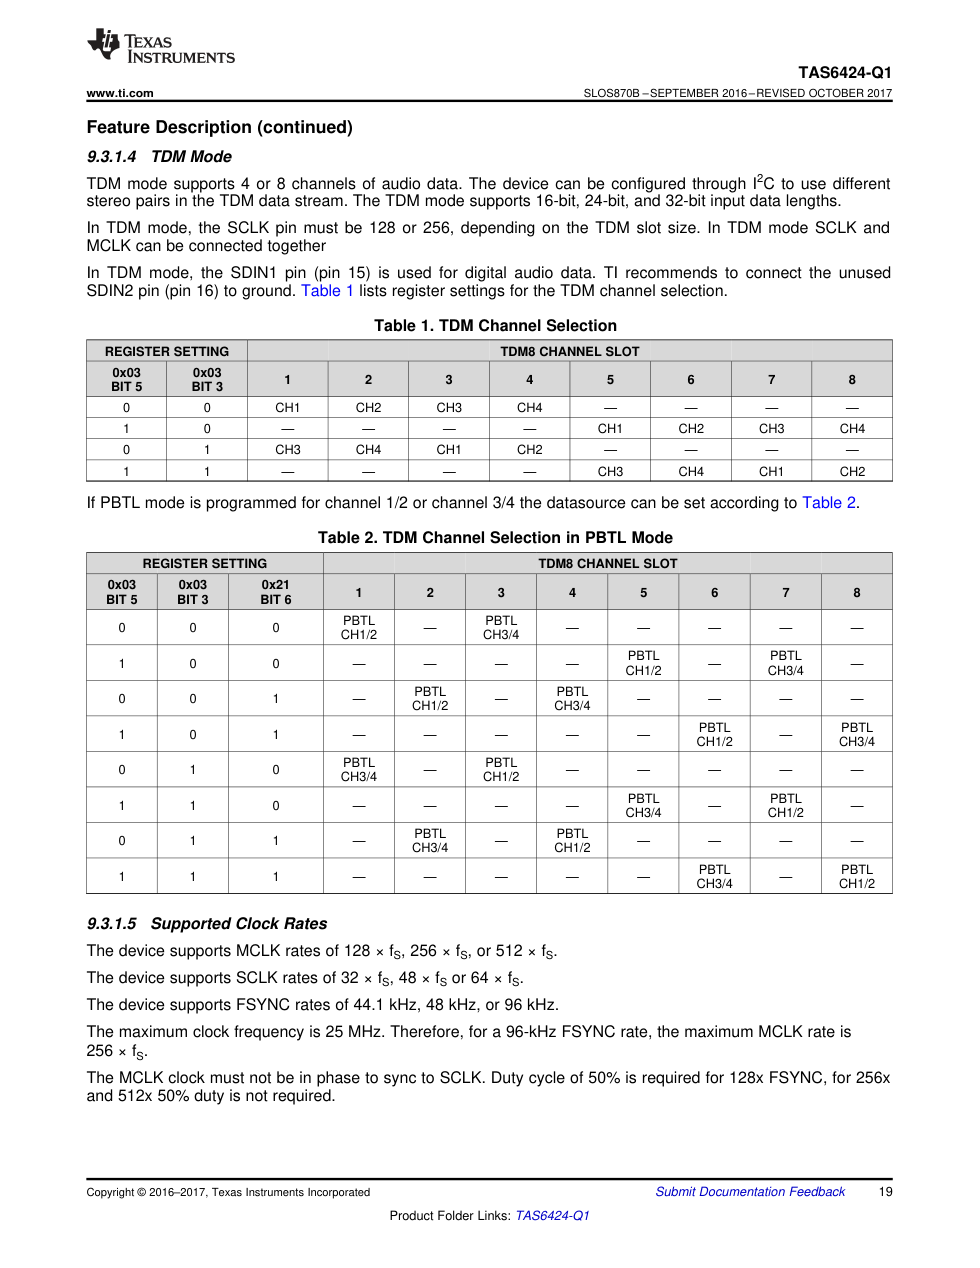
tmp/phase_1/AMP_19.png
