RamazanBozkurrtt/circuitBuilderAi-Astra/tmp/phase_1/AMP_21.png

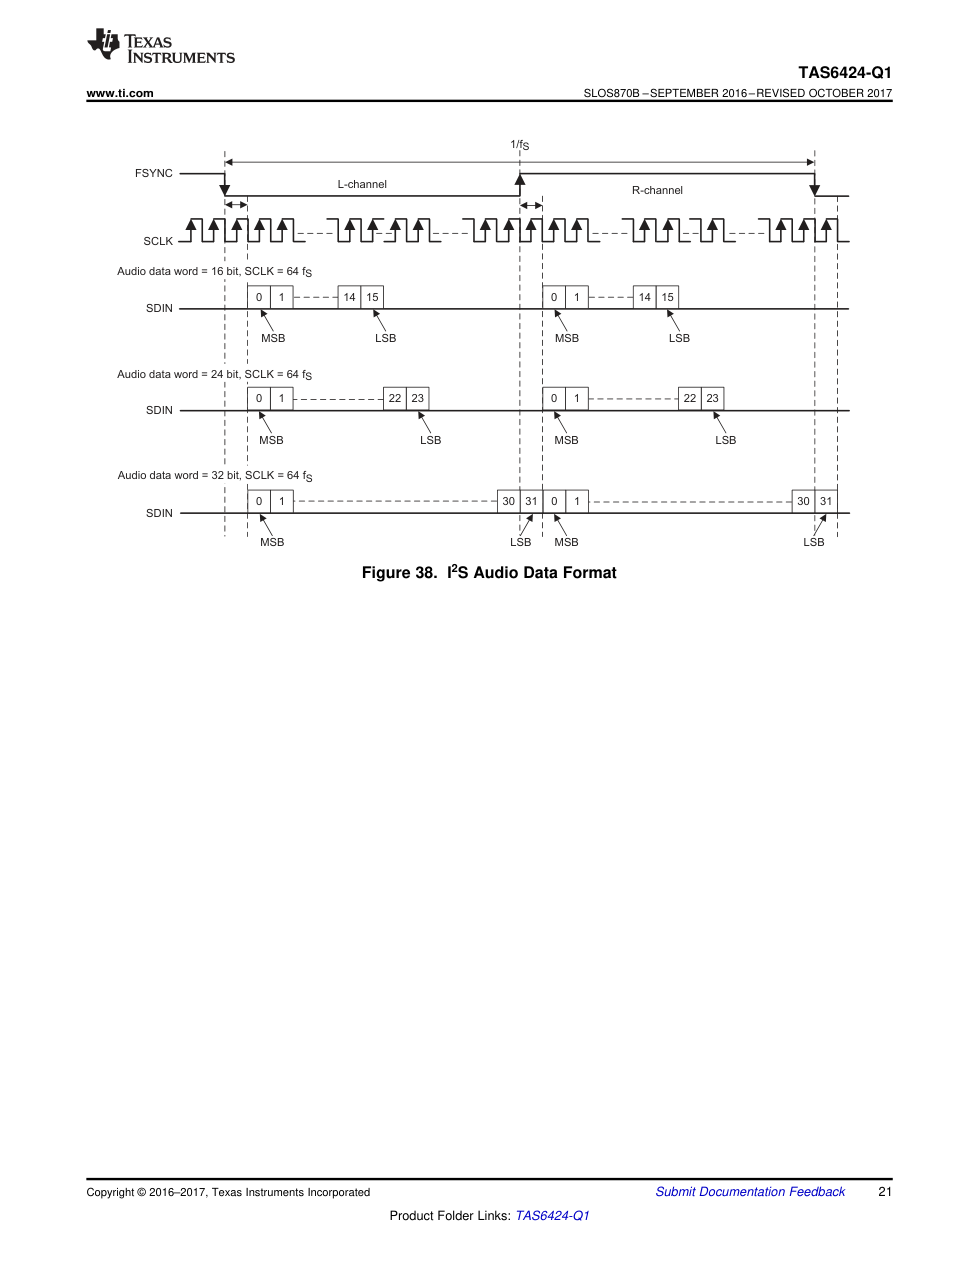
tmp/phase_1/AMP_21.png
