RamazanBozkurrtt/circuitBuilderAi-Astra/tmp/phase_1/AMP_22.png

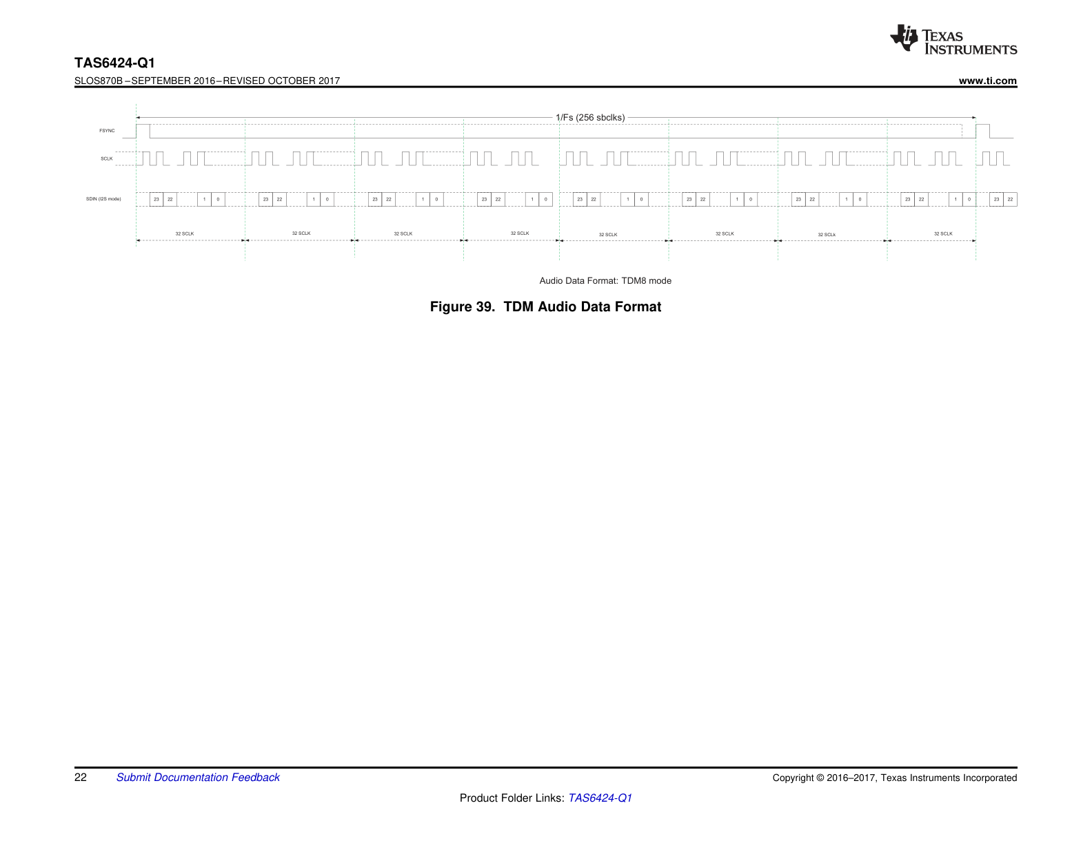
tmp/phase_1/AMP_22.png
