RamazanBozkurrtt/circuitBuilderAi-Astra/tmp/phase_1/AMP_34.png

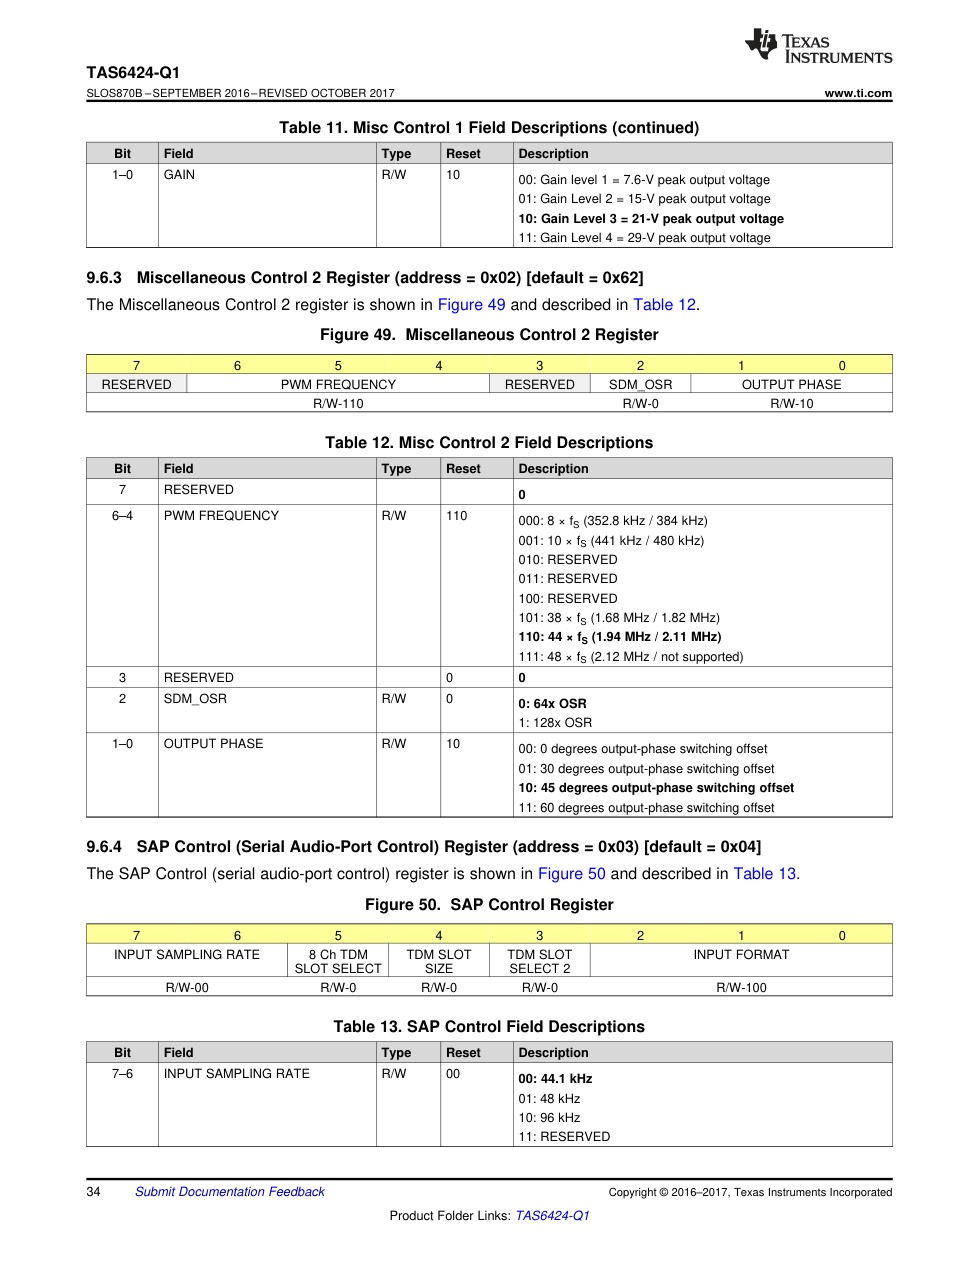
tmp/phase_1/AMP_34.png
