RamazanBozkurrtt/circuitBuilderAi-Astra/tmp/phase_1/AMPEVAL_23.png

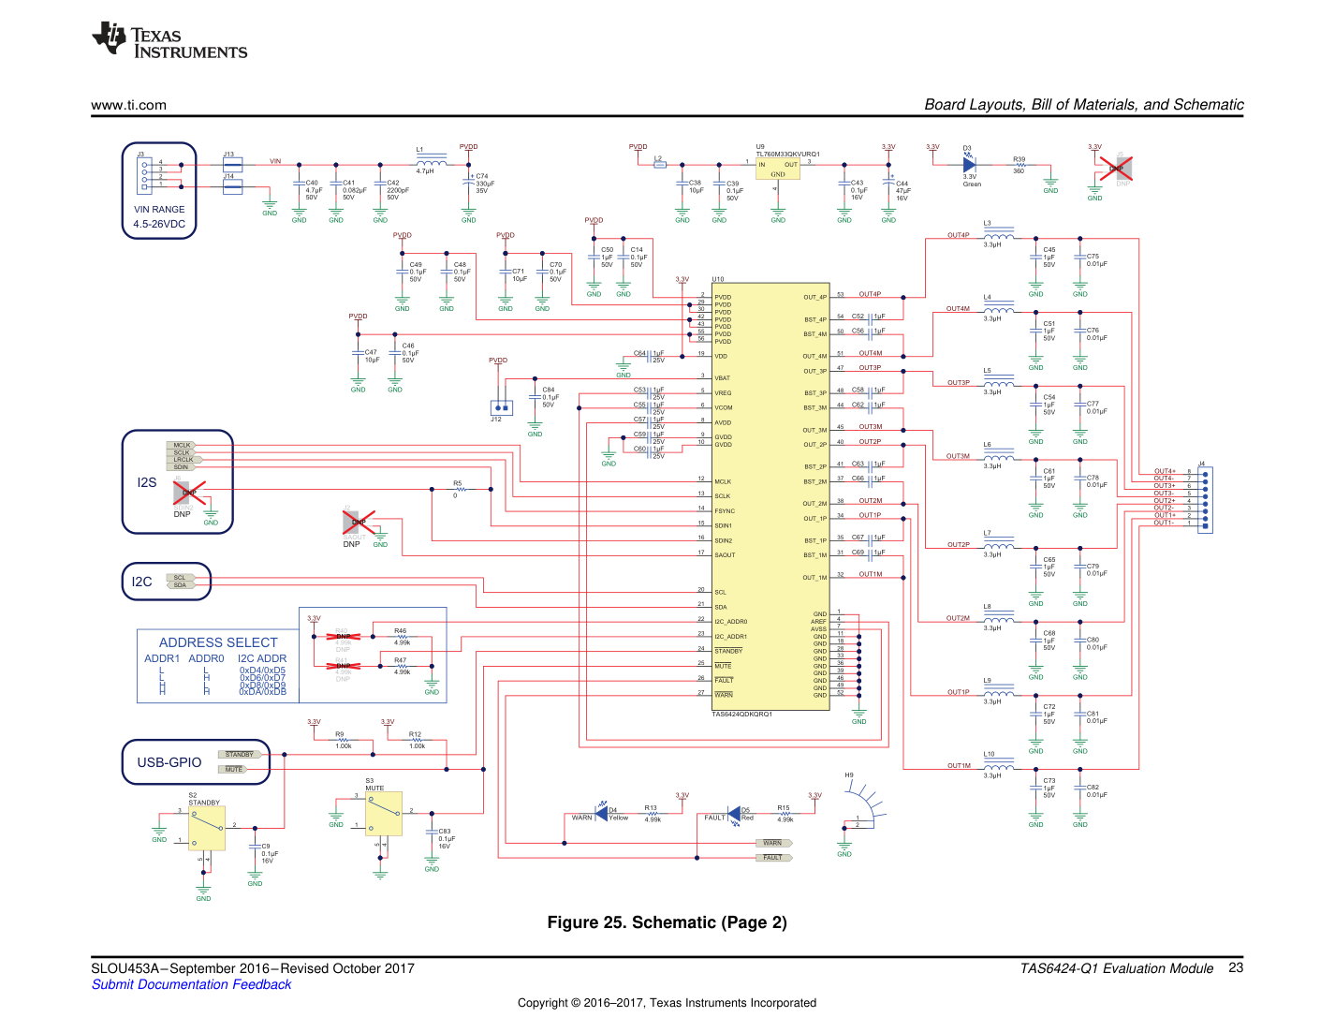
tmp/phase_1/AMPEVAL_23.png
