RamazanBozkurrtt/circuitBuilderAi-Astra/tmp/phase_1/AMPEVAL_27.png

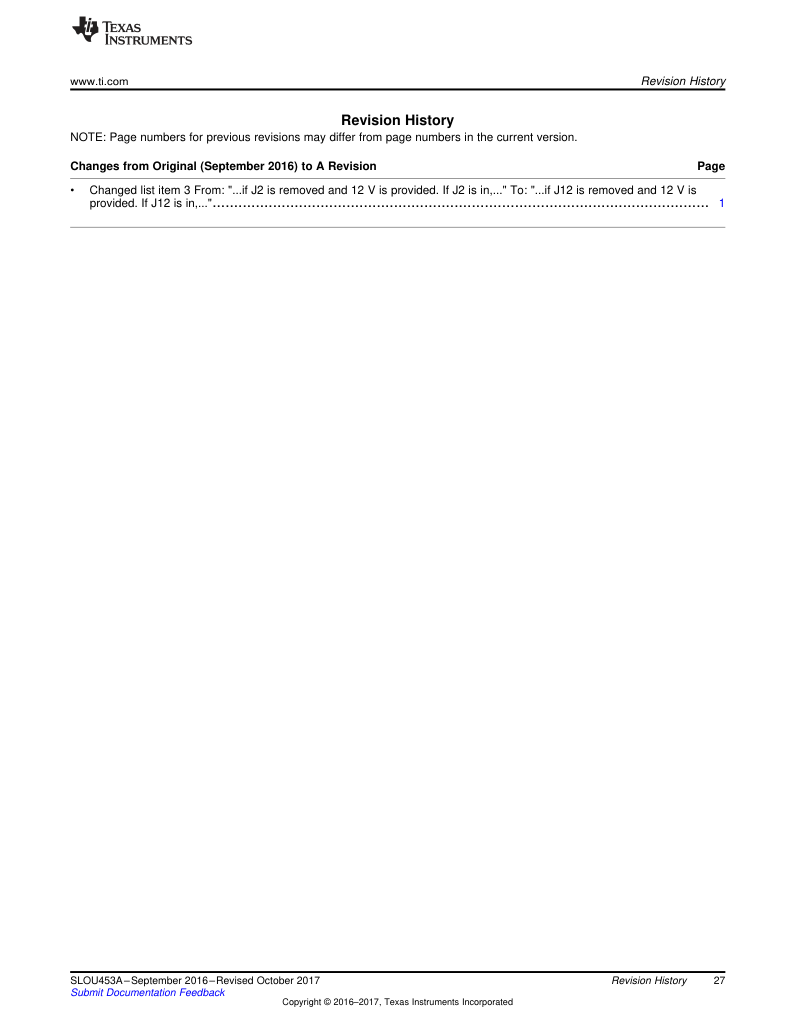
tmp/phase_1/AMPEVAL_27.png
