RamazanBozkurrtt/circuitBuilderAi-Astra/tmp/phase_1/AMPEVAL_28.png

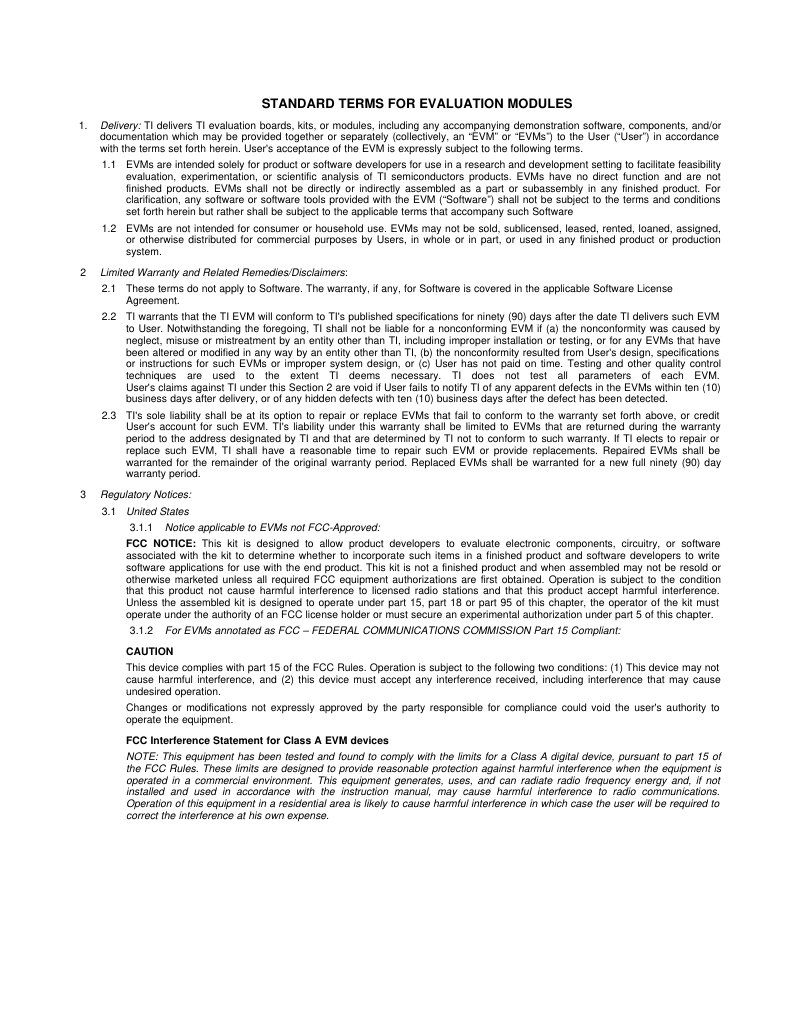
tmp/phase_1/AMPEVAL_28.png
