RamazanBozkurrtt/circuitBuilderAi-Astra/tmp/phase_1/DSP_89.png

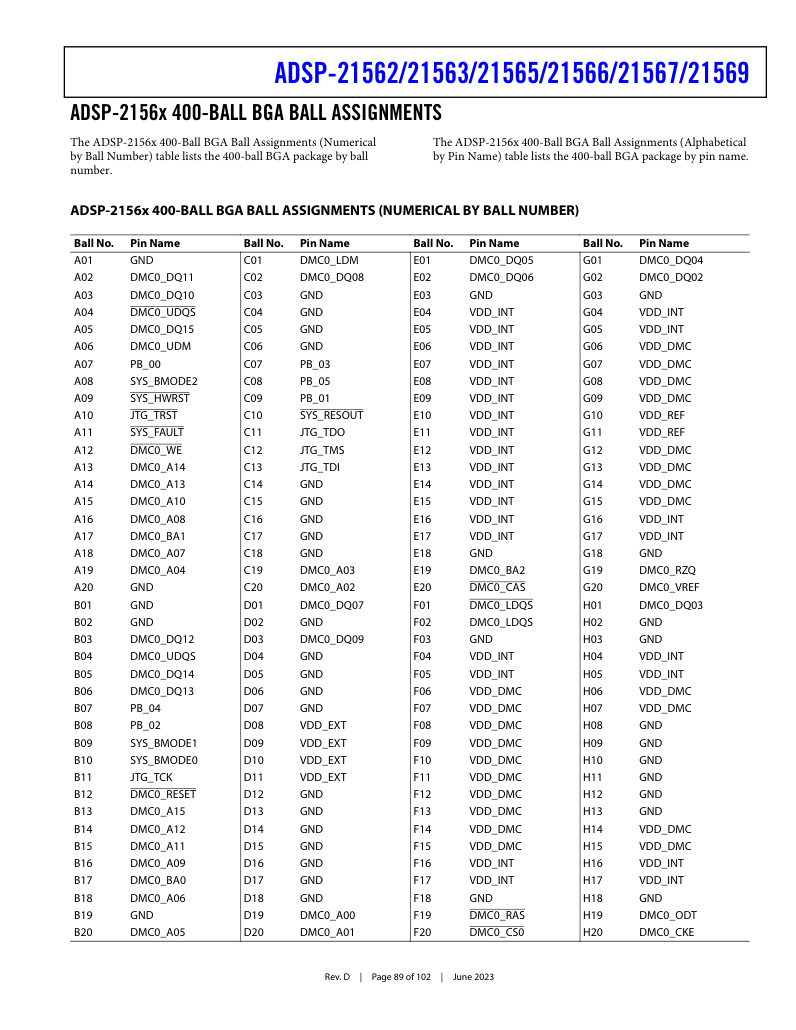
tmp/phase_1/DSP_89.png
