RamazanBozkurrtt/circuitBuilderAi-Astra/tmp/phase_1/DSP_90.png

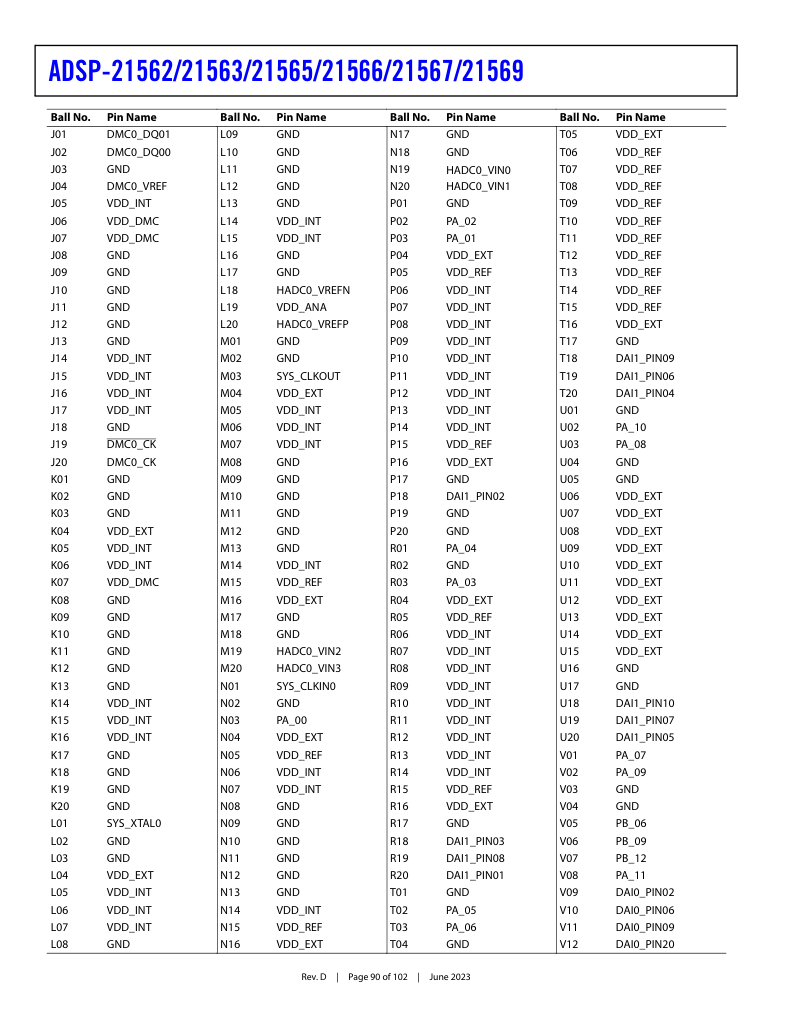
tmp/phase_1/DSP_90.png
