RamazanBozkurrtt/circuitBuilderAi-Astra/tmp/phase_1/DSP_91.png

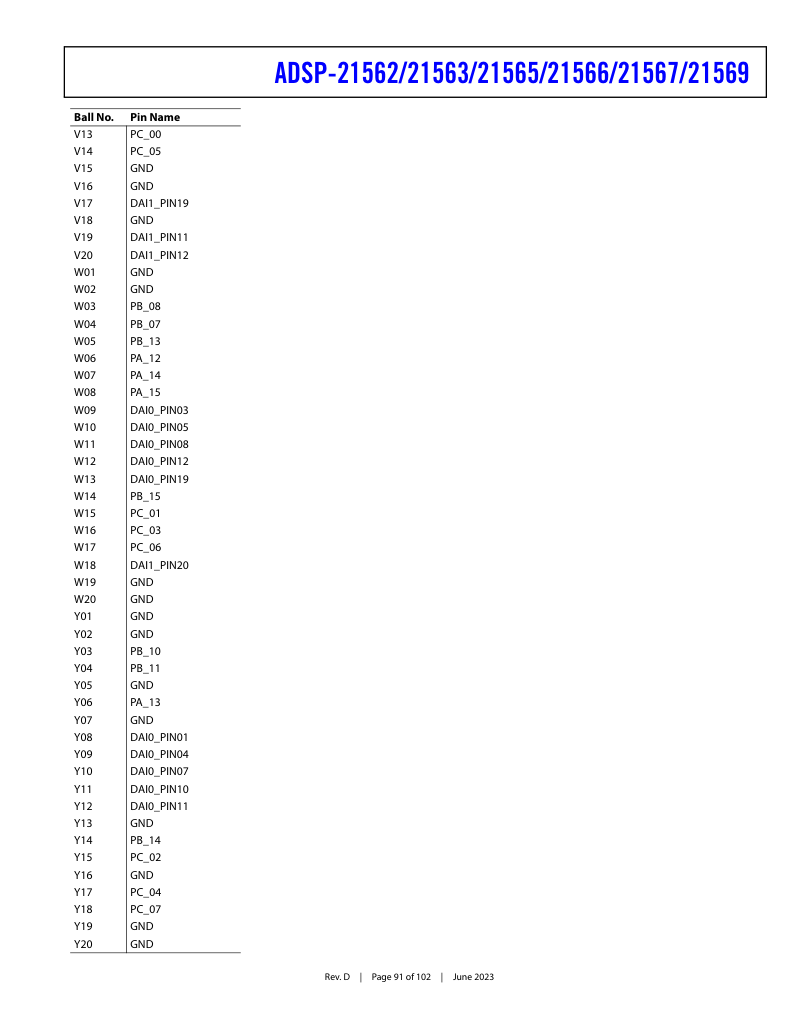
tmp/phase_1/DSP_91.png
