RamazanBozkurrtt/circuitBuilderAi-Astra/tmp/phase_1/MIC_8.png

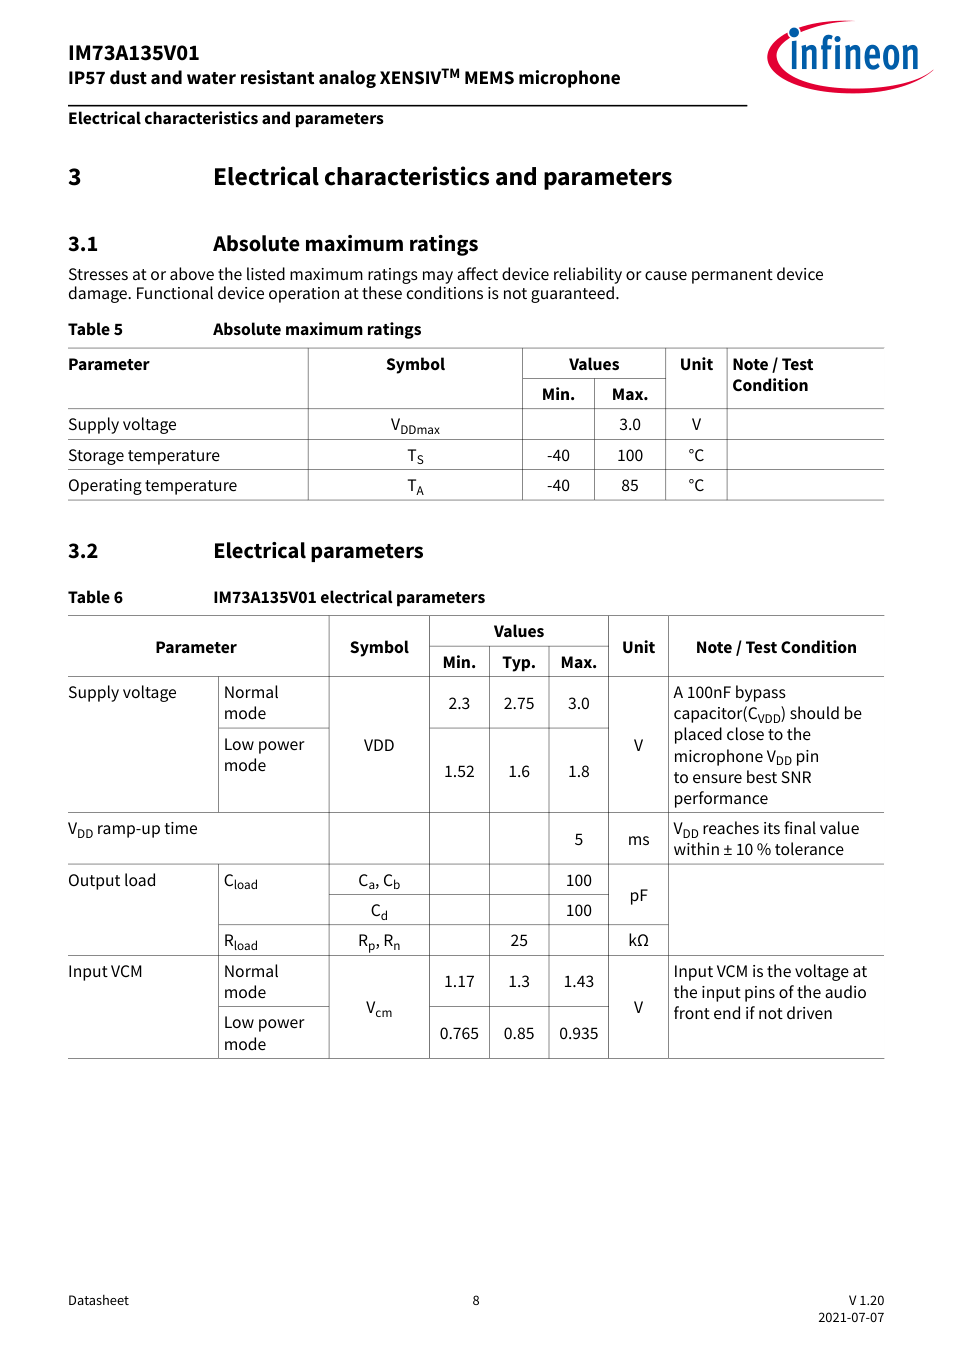
tmp/phase_1/MIC_8.png
