RamazanBozkurrtt/circuitBuilderAi-Astra/tmp/phase_1/MIC_9.png

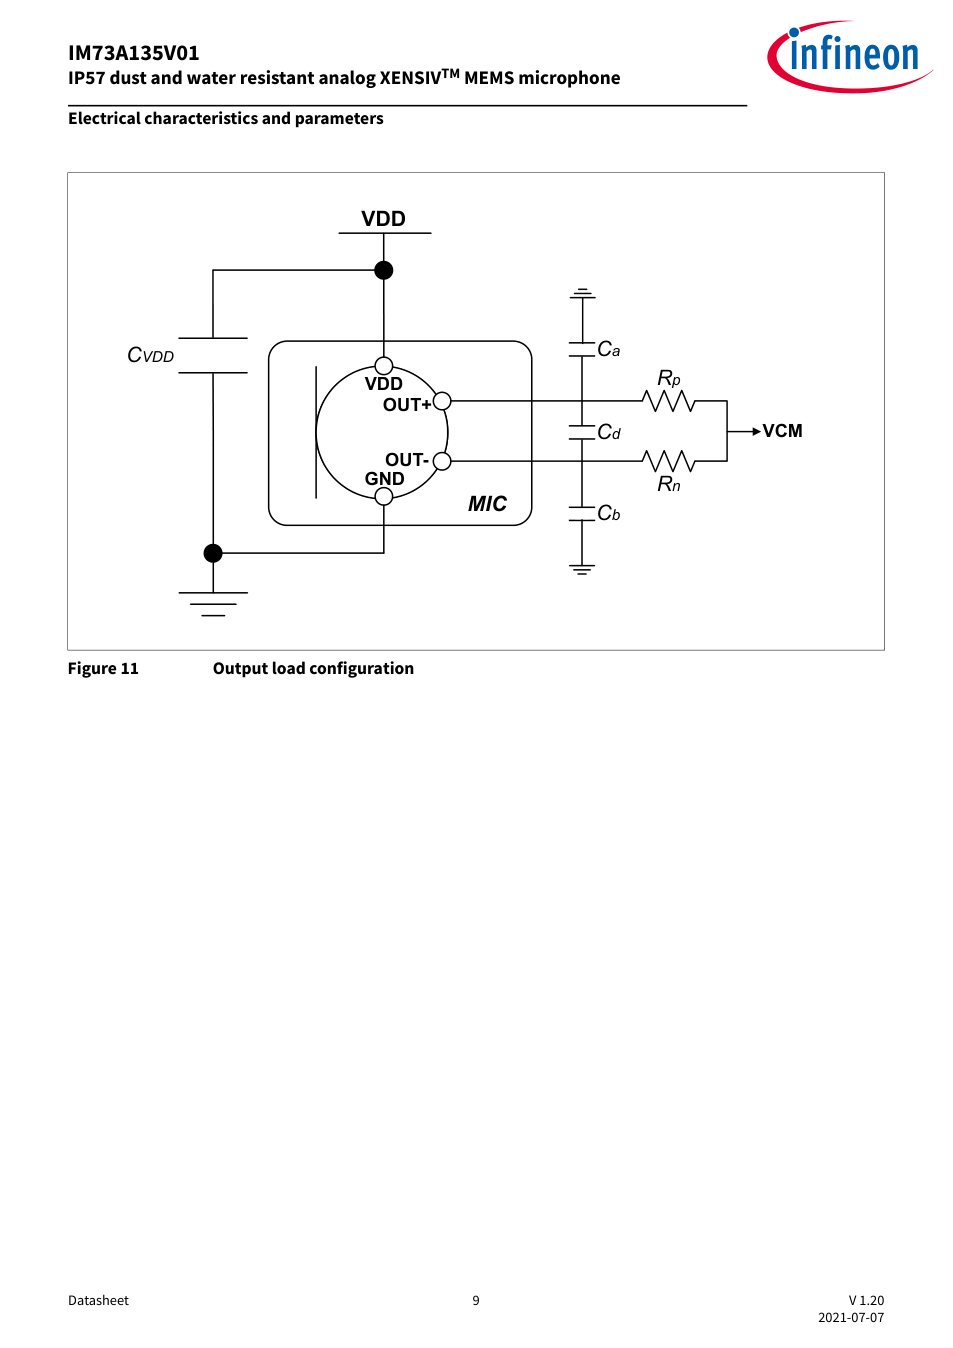
tmp/phase_1/MIC_9.png
