RamazanBozkurrtt/circuitBuilderAi-Astra/tmp/phase_1/MIC_10.png

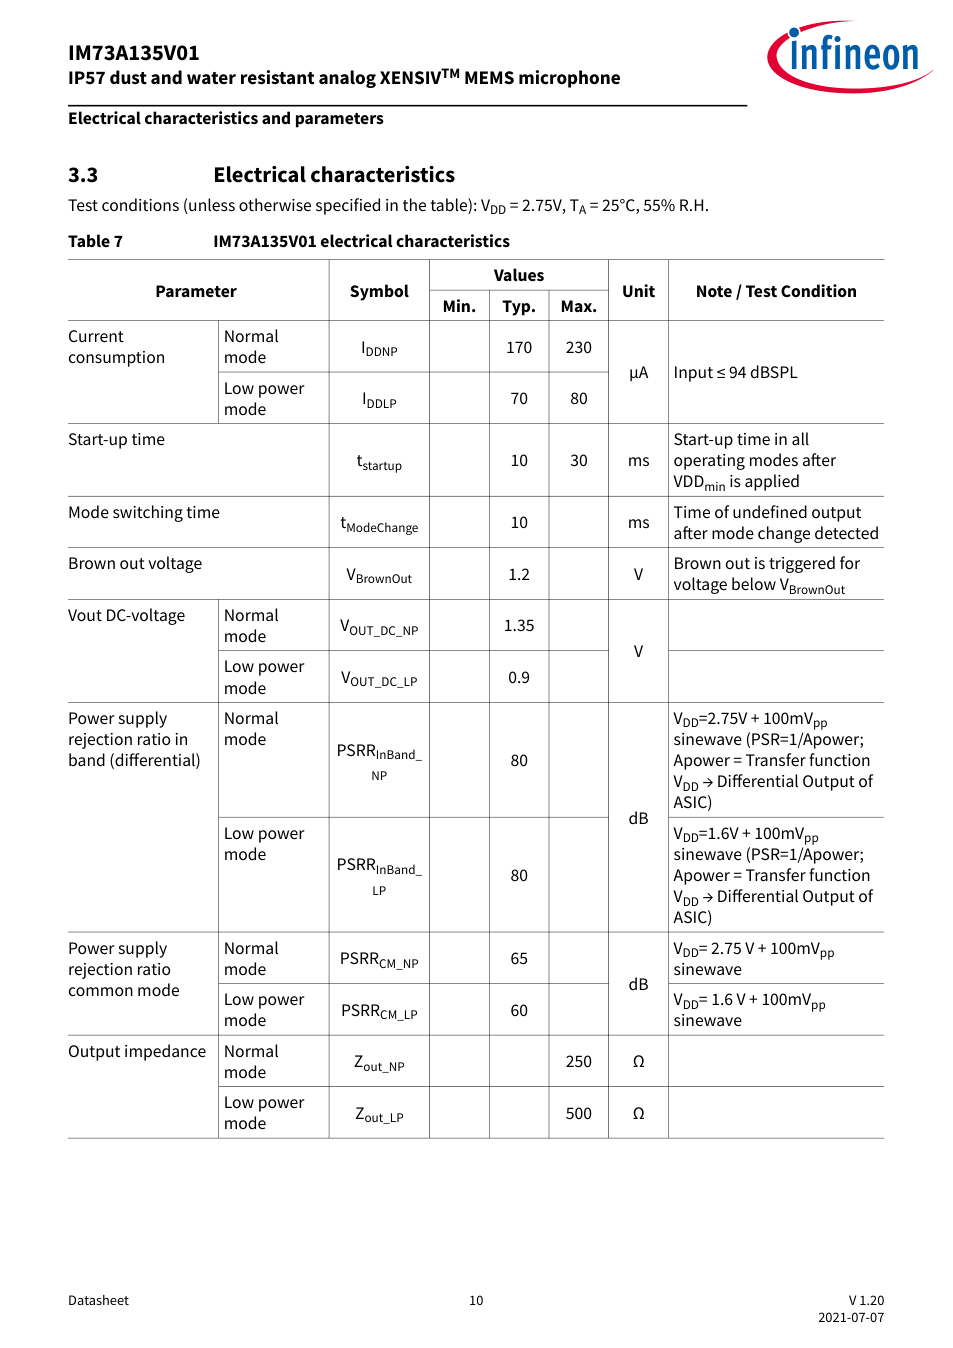
tmp/phase_1/MIC_10.png
