RamazanBozkurrtt/circuitBuilderAi-Astra/tmp/phase_1/MIC_11.png

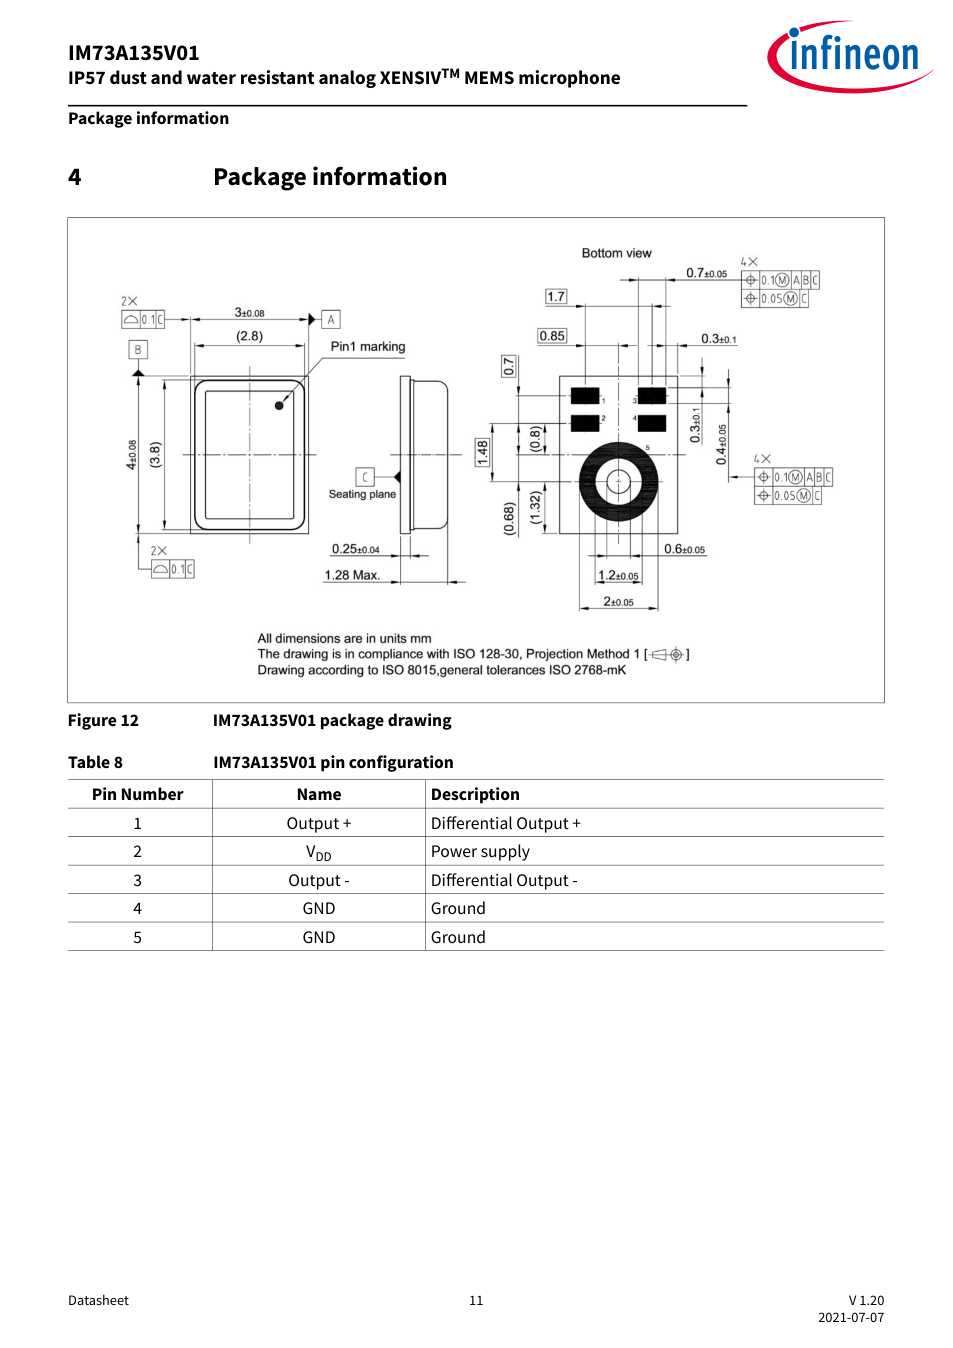
tmp/phase_1/MIC_11.png
