RamazanBozkurrtt/circuitBuilderAi-Astra/tmp/phase_1/SOMSCH_7.png

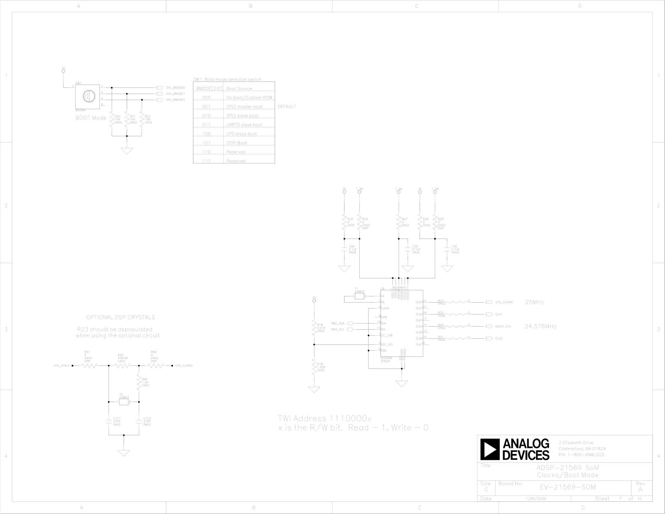
tmp/phase_1/SOMSCH_7.png
