RamazanBozkurrtt/circuitBuilderAi-Astra/tmp/phase_1/SOMSCH_9.png

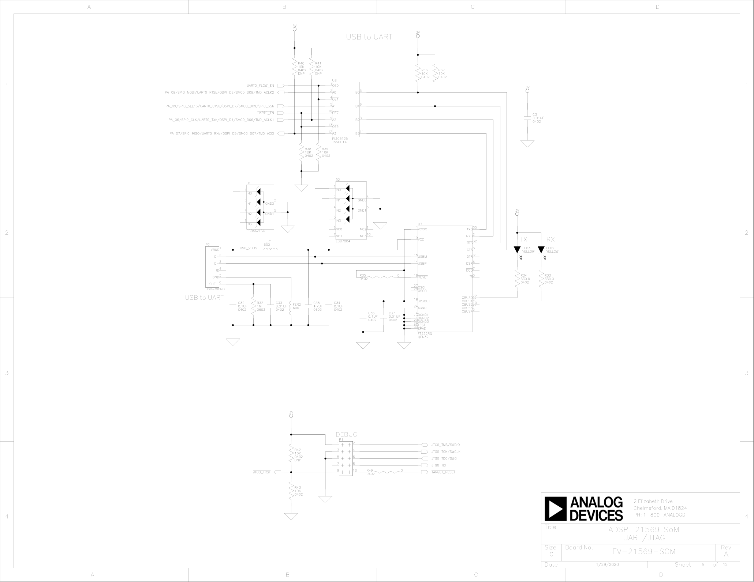
tmp/phase_1/SOMSCH_9.png
