RamazanBozkurrtt/circuitBuilderAi-Astra/tmp/phase_1/SOMSCH_11.png

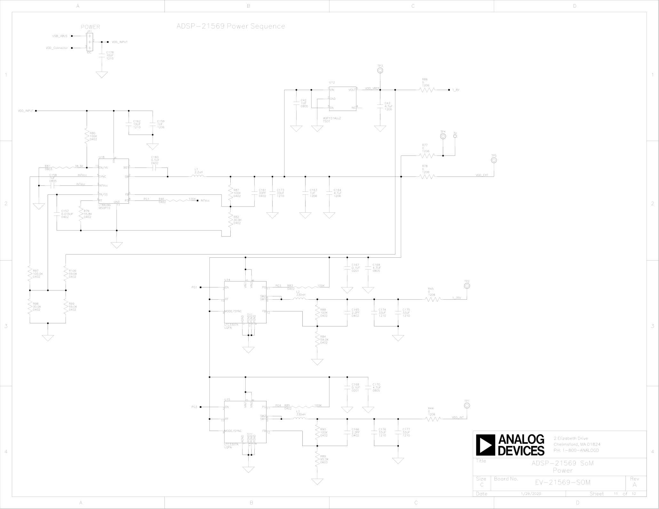
tmp/phase_1/SOMSCH_11.png
