RamazanBozkurrtt/circuitBuilderAi-Astra/tmp/phase_1b/ADC_3.png

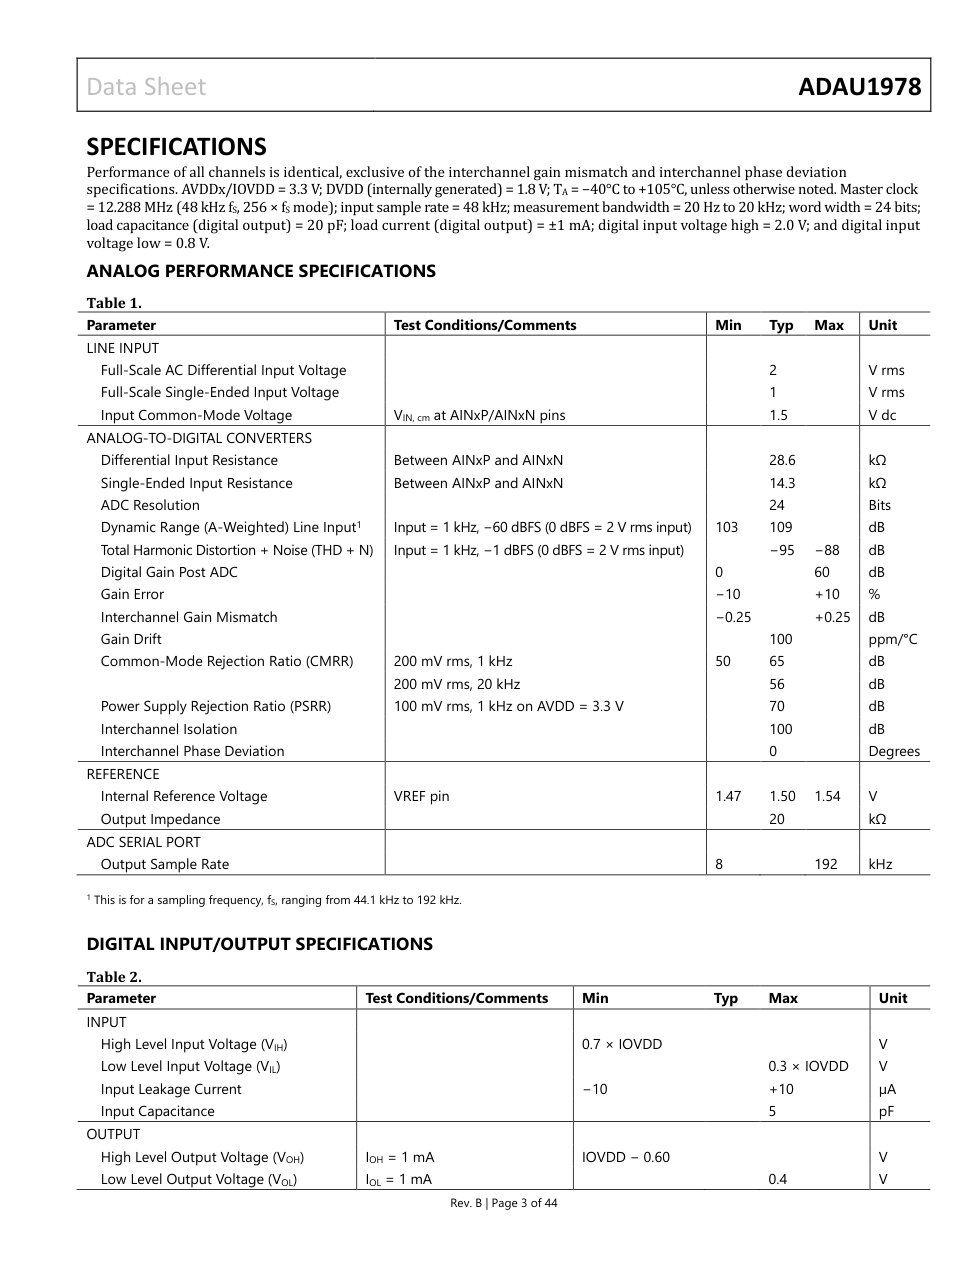
tmp/phase_1b/ADC_3.png
