RamazanBozkurrtt/circuitBuilderAi-Astra/tmp/phase_1b/ADC_4.png

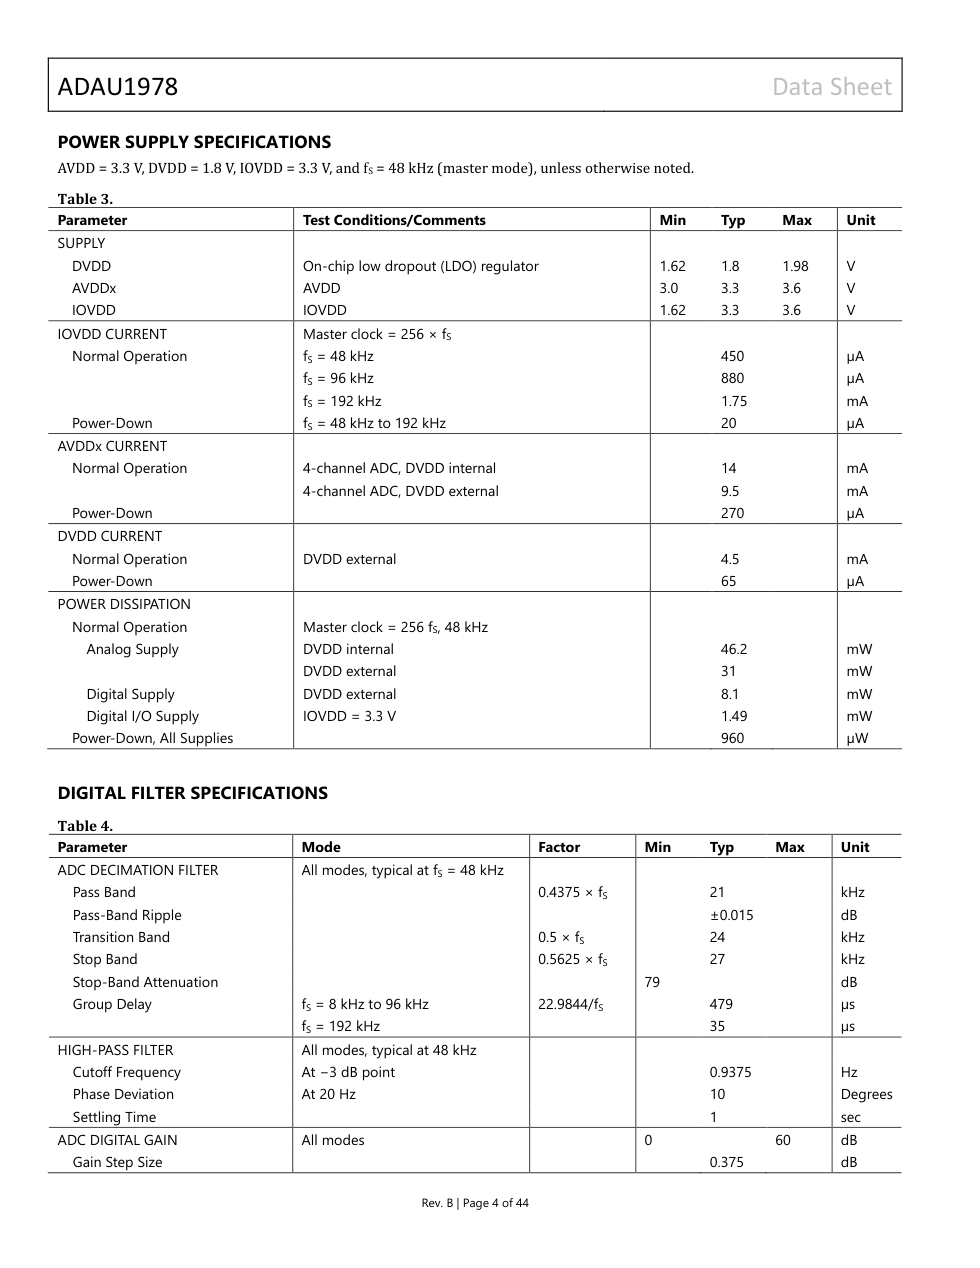
tmp/phase_1b/ADC_4.png
