RamazanBozkurrtt/circuitBuilderAi-Astra/tmp/phase_1b/ADC_5.png

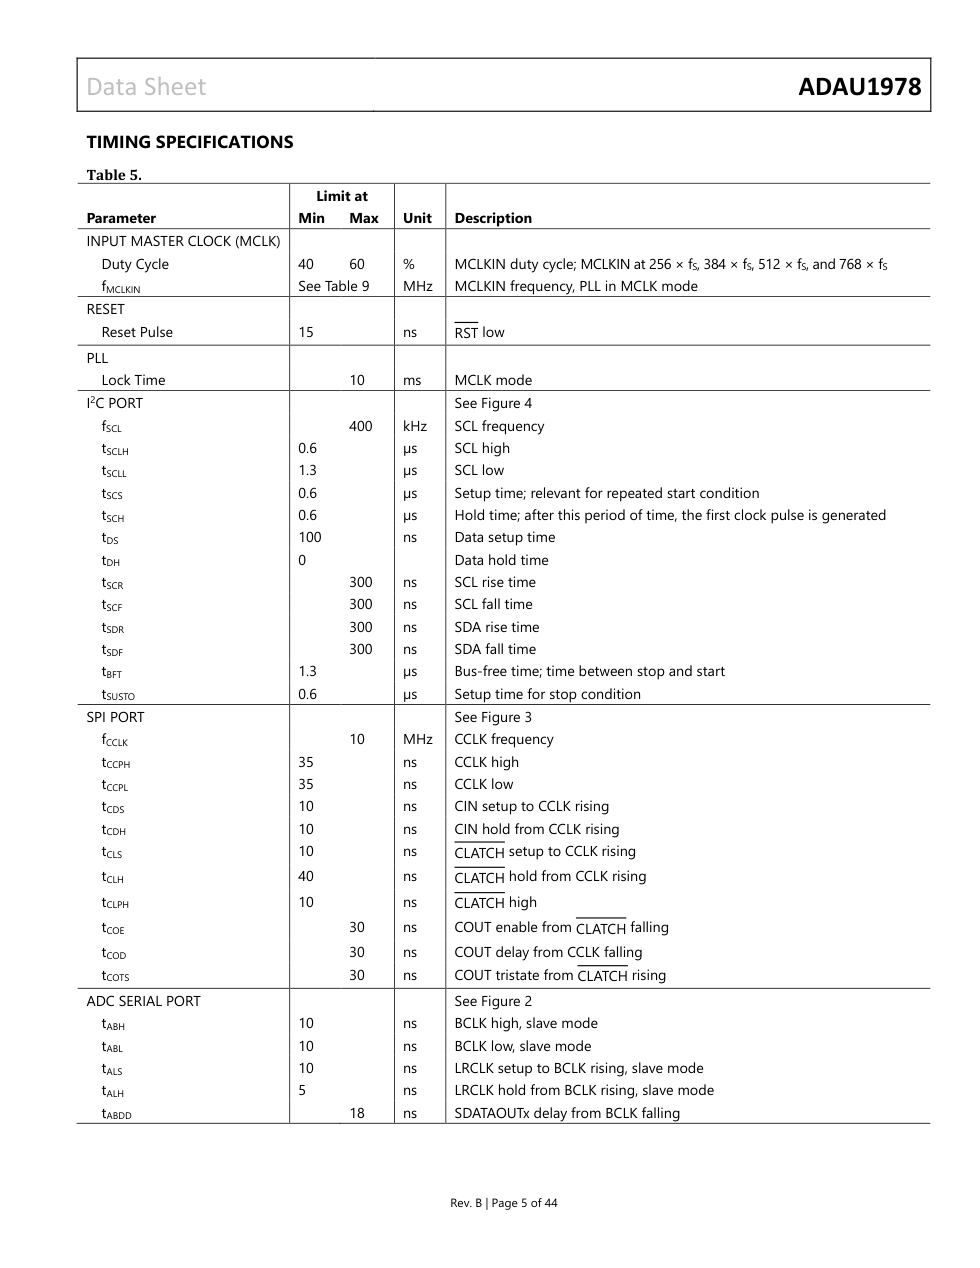
tmp/phase_1b/ADC_5.png
