RamazanBozkurrtt/circuitBuilderAi-Astra/tmp/phase_1b/ADC_6.png

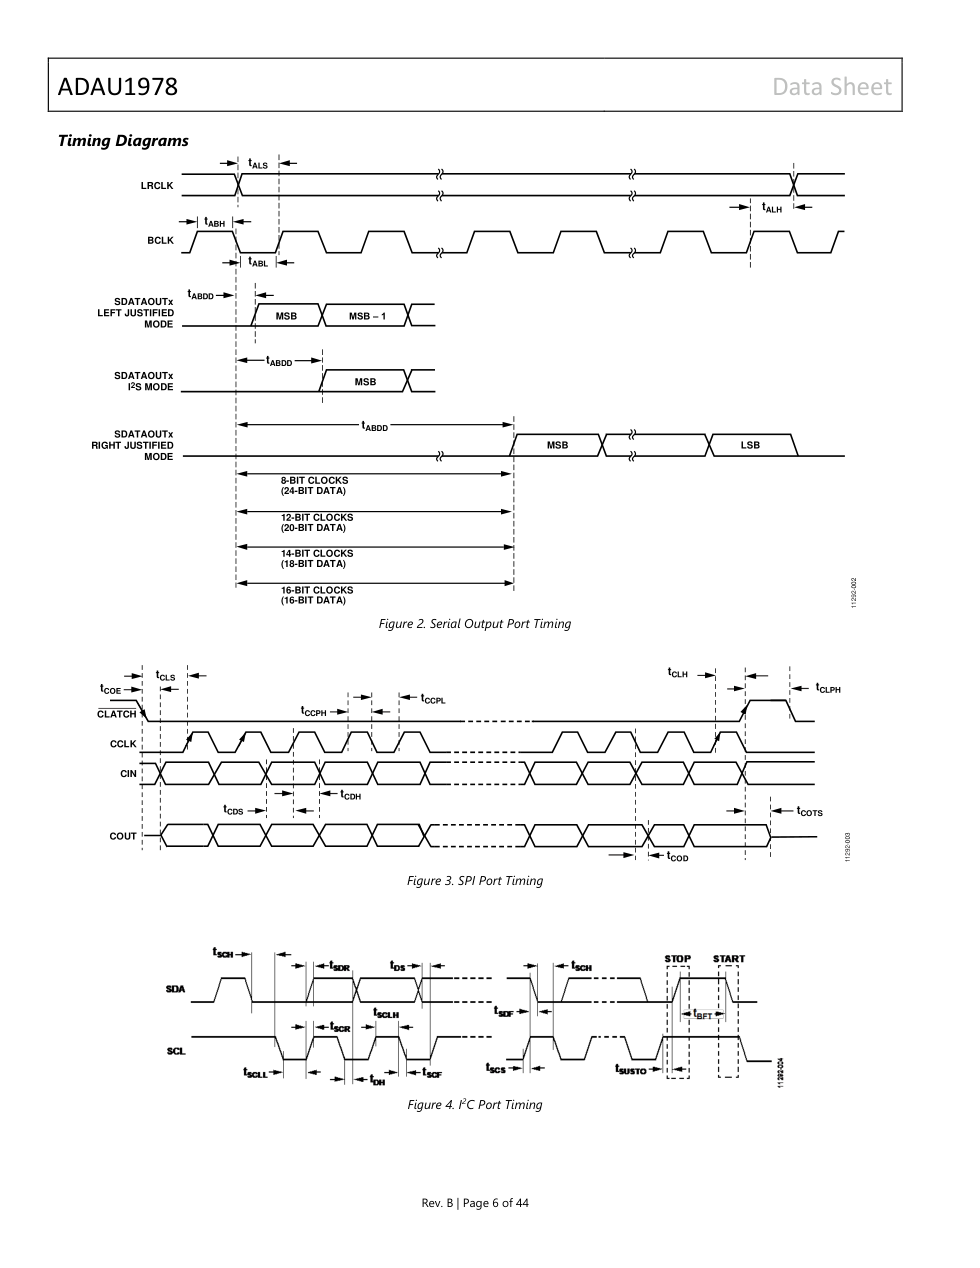
tmp/phase_1b/ADC_6.png
