RamazanBozkurrtt/circuitBuilderAi-Astra/tmp/phase_1b/ADC_31.png

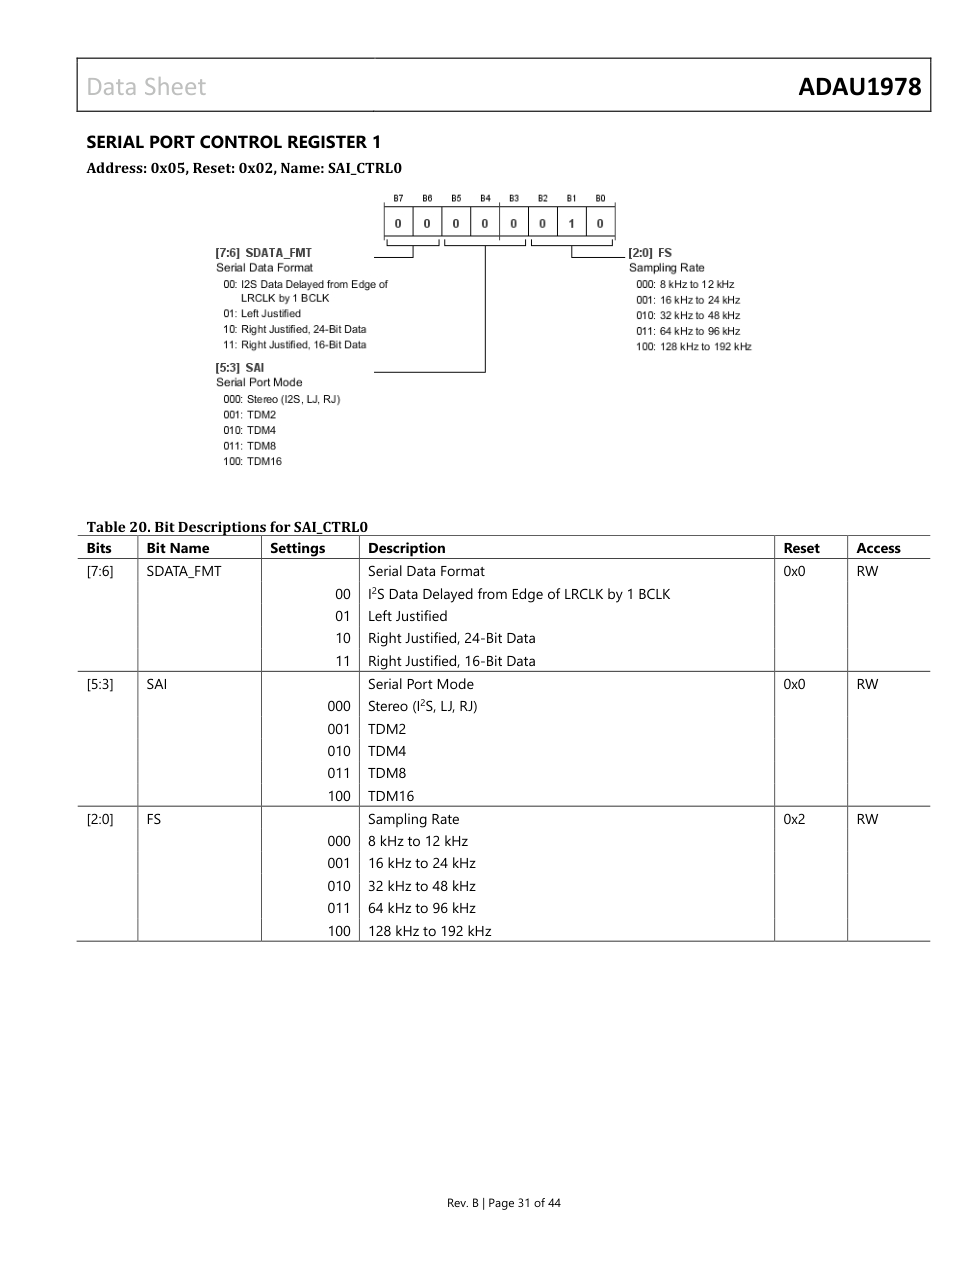
tmp/phase_1b/ADC_31.png
