RamazanBozkurrtt/circuitBuilderAi-Astra/tmp/phase_1b/ADC_42.png

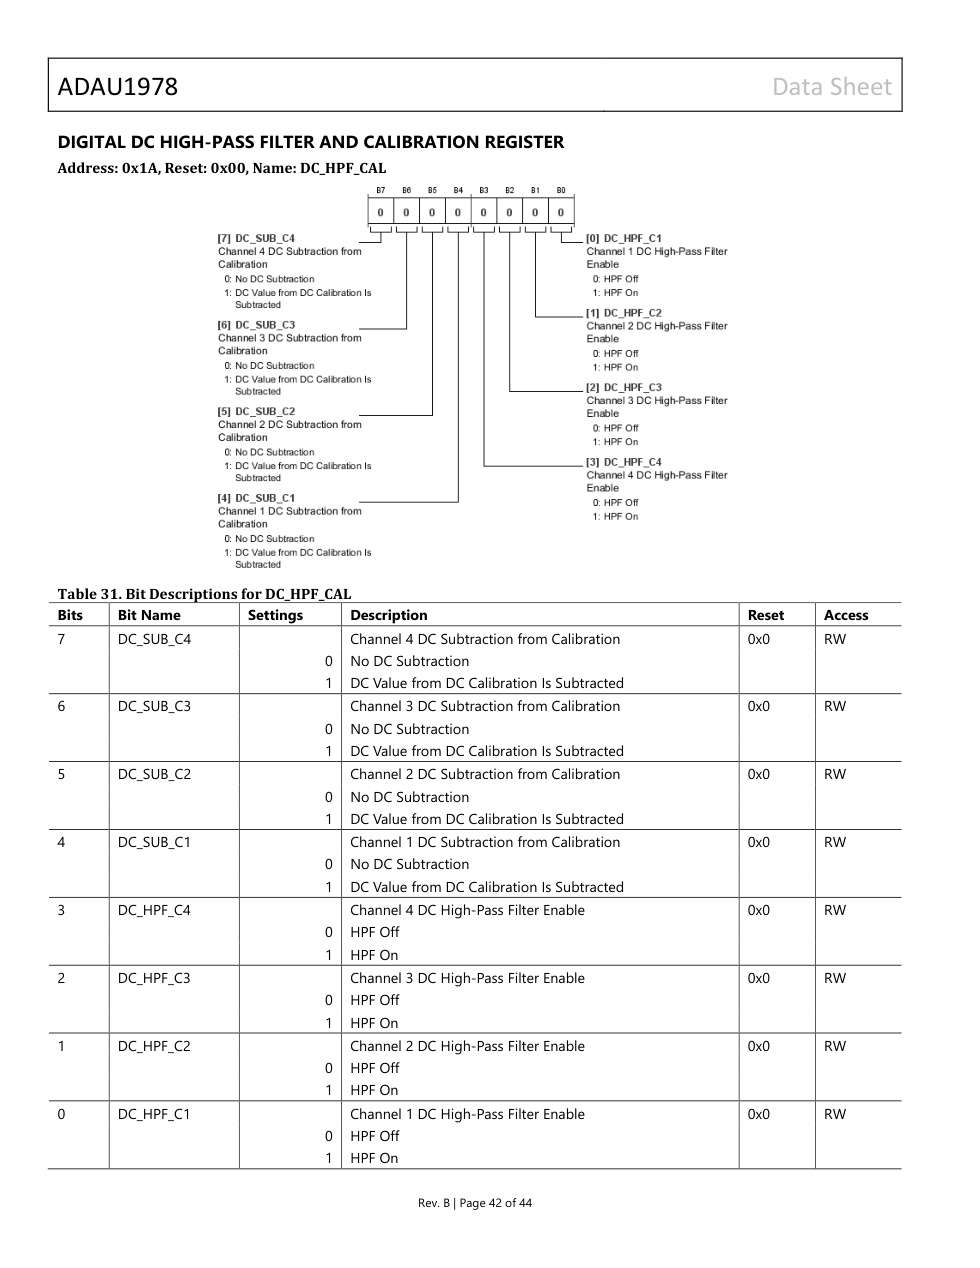
tmp/phase_1b/ADC_42.png
