RamazanBozkurrtt/circuitBuilderAi-Astra/tmp/phase_1b/AMP_6.png

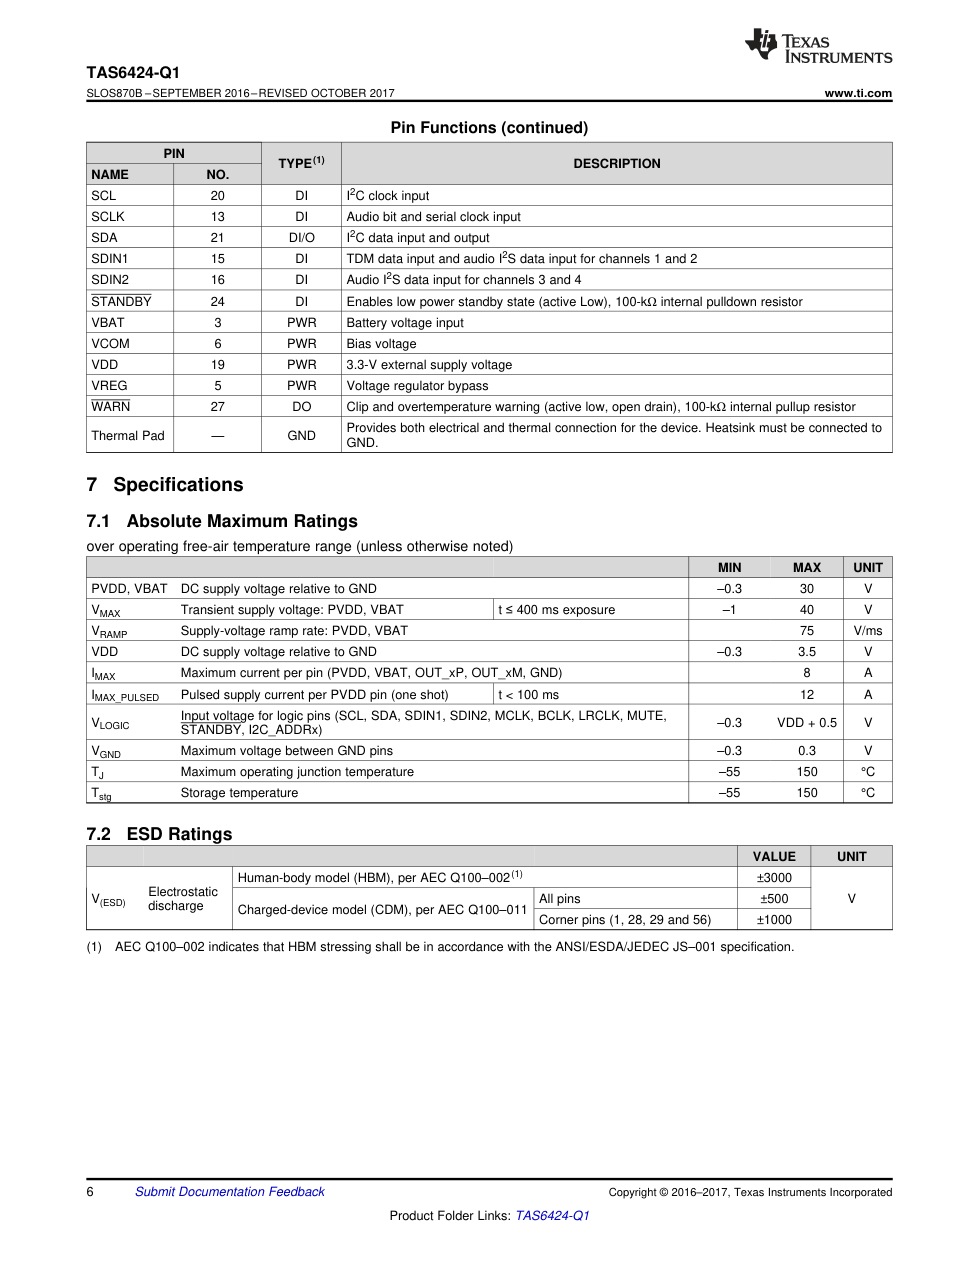
tmp/phase_1b/AMP_6.png
