RamazanBozkurrtt/circuitBuilderAi-Astra/tmp/phase_1b/AMP_8.png

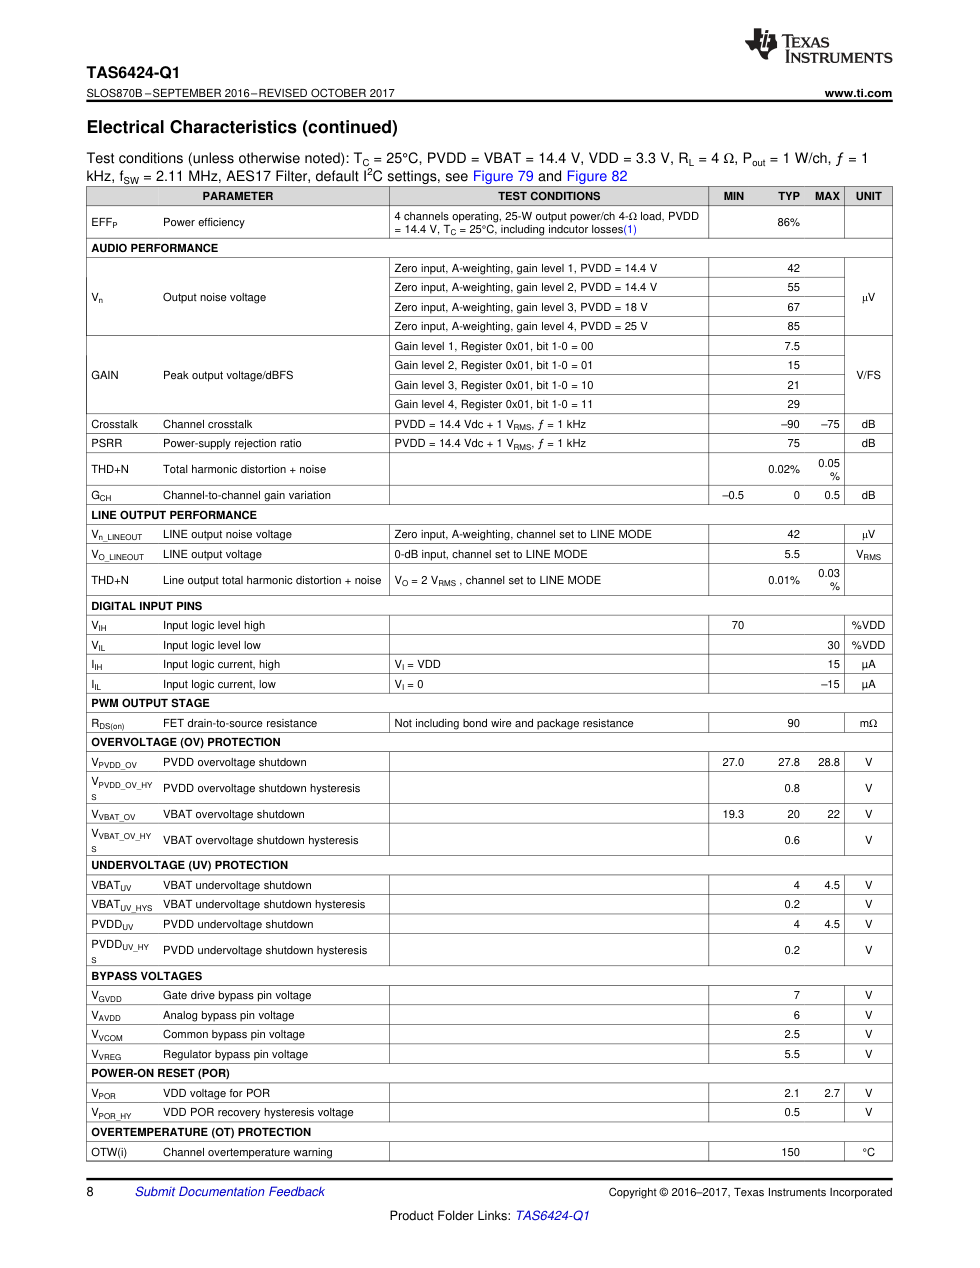
tmp/phase_1b/AMP_8.png
