RamazanBozkurrtt/circuitBuilderAi-Astra/tmp/phase_1b/AMP_10.png

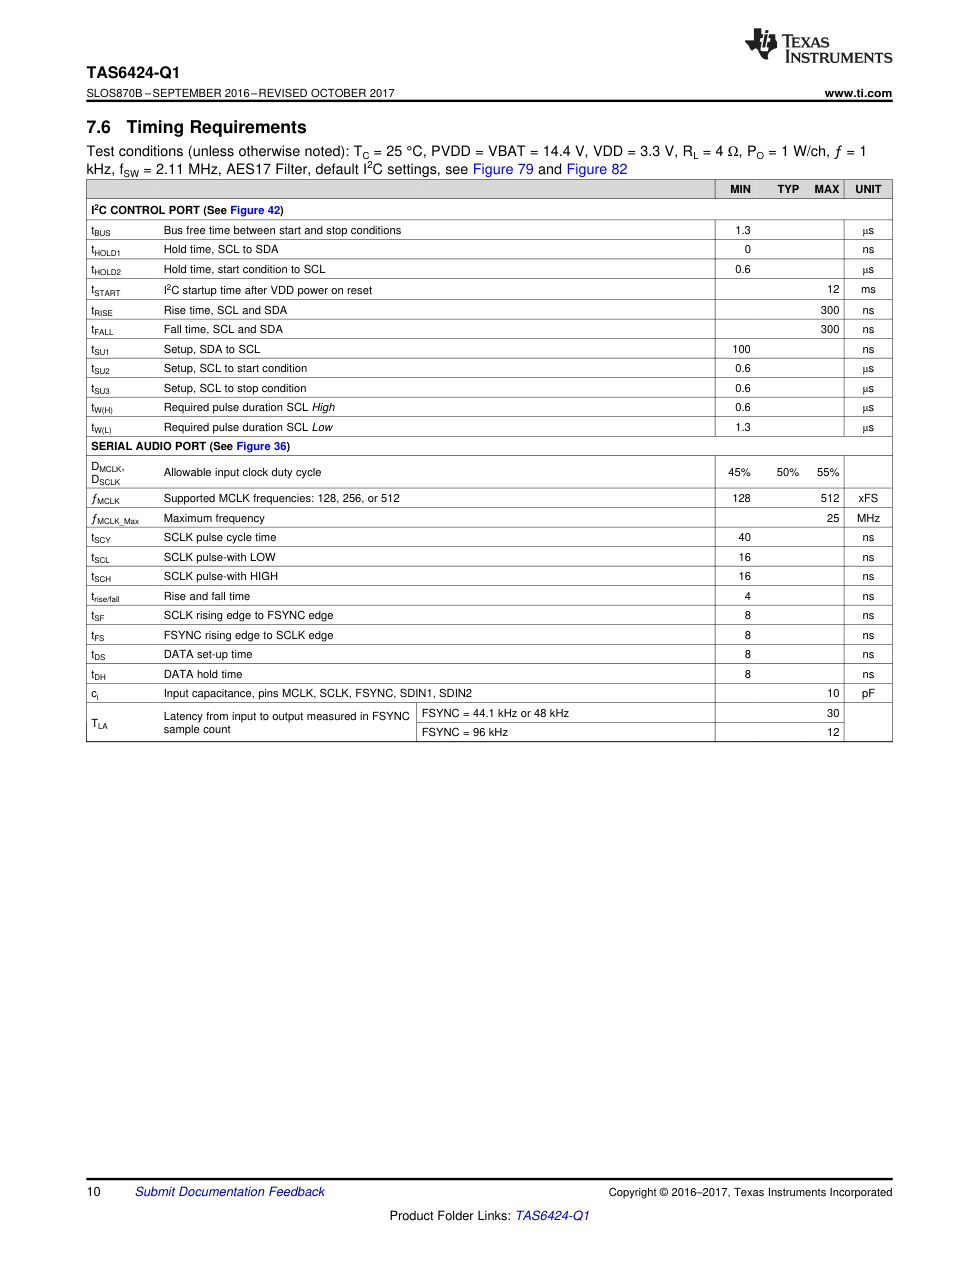
tmp/phase_1b/AMP_10.png
