RamazanBozkurrtt/circuitBuilderAi-Astra/tmp/phase_1b/AMP_20.png

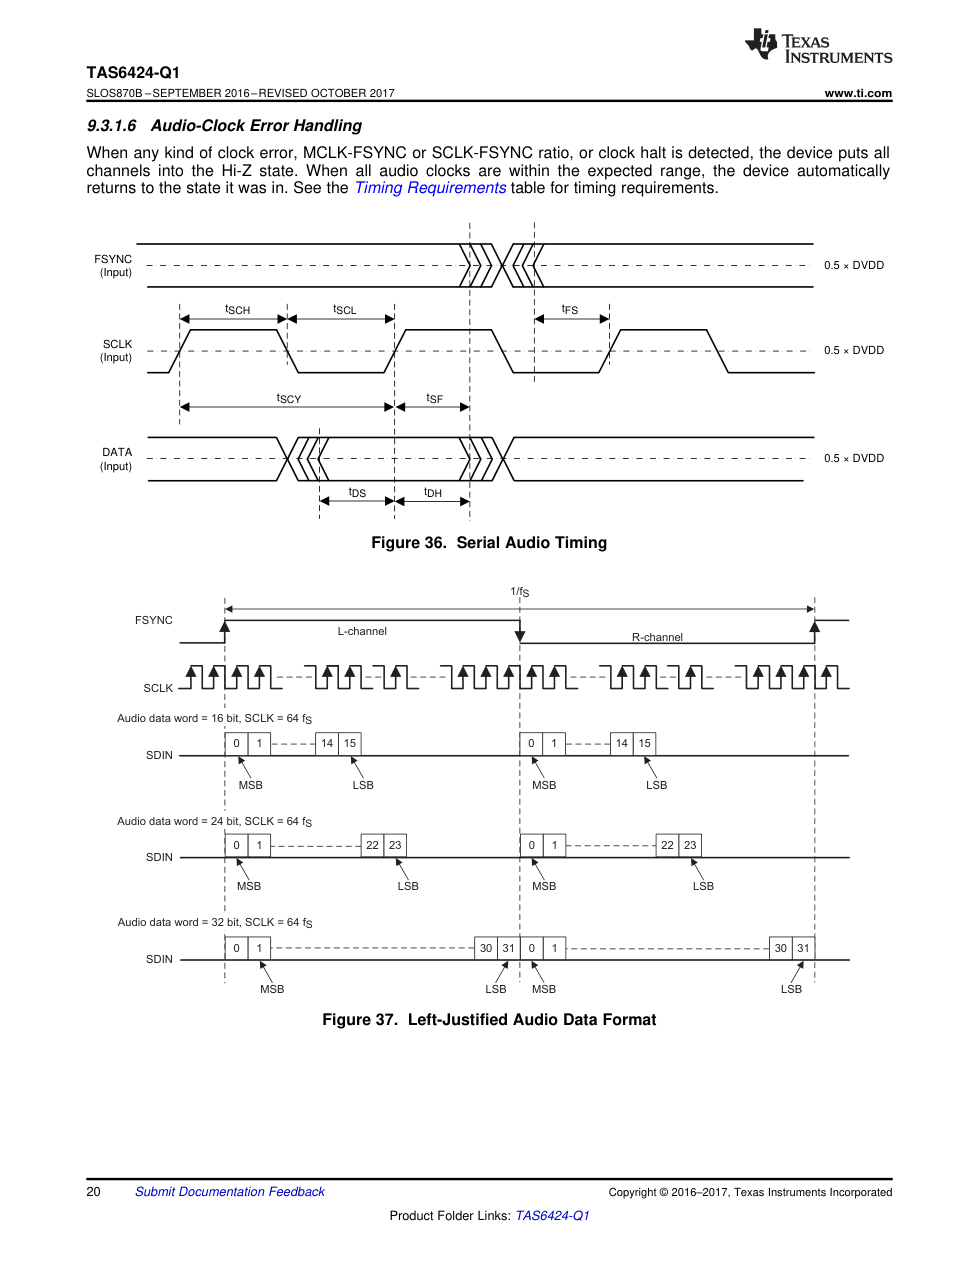
tmp/phase_1b/AMP_20.png
