RamazanBozkurrtt/circuitBuilderAi-Astra/tmp/phase_1b/AMP_24.png

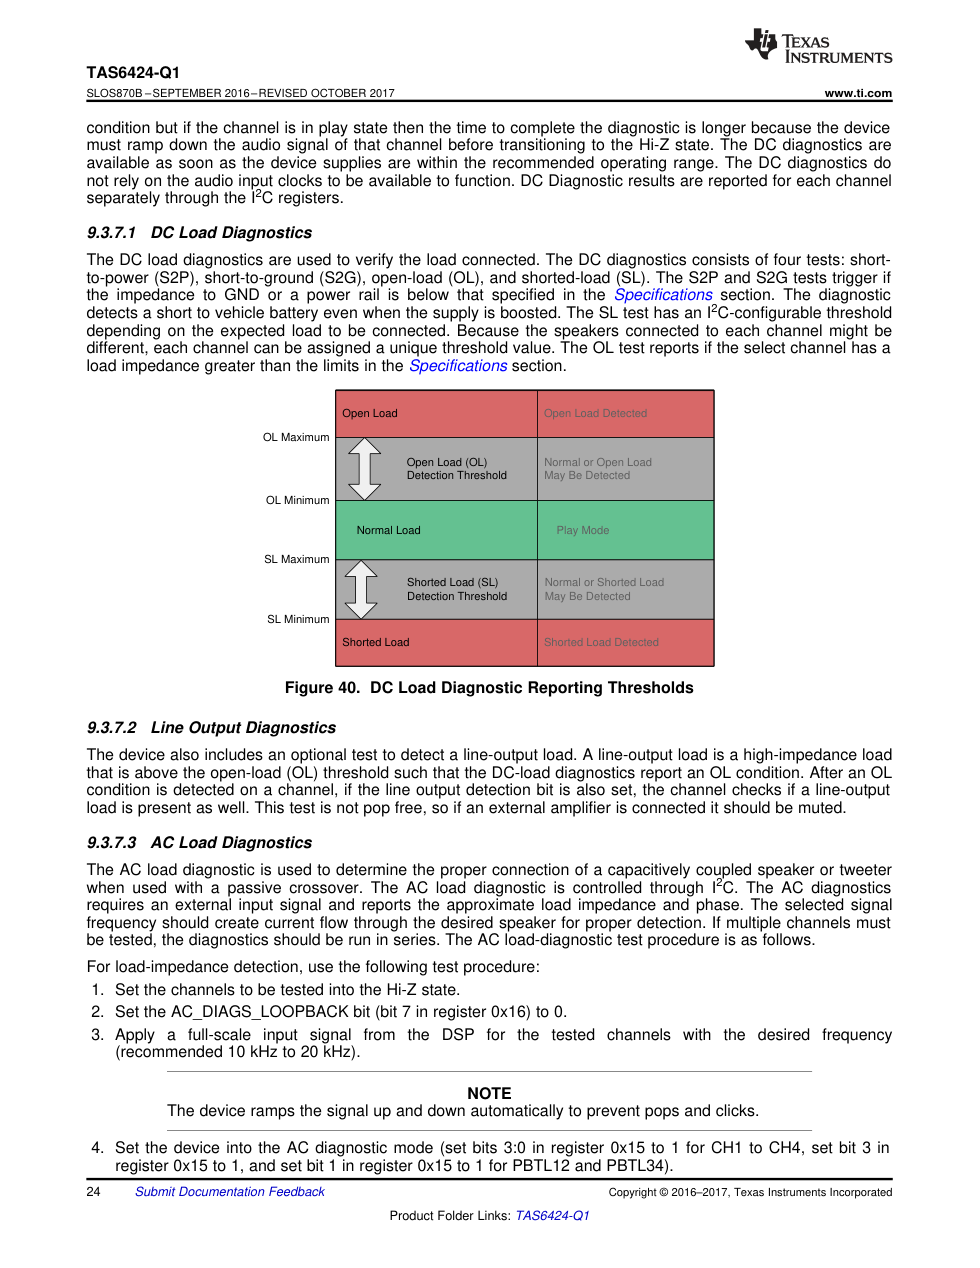
tmp/phase_1b/AMP_24.png
