RamazanBozkurrtt/circuitBuilderAi-Astra/tmp/phase_1b/AMP_35.png

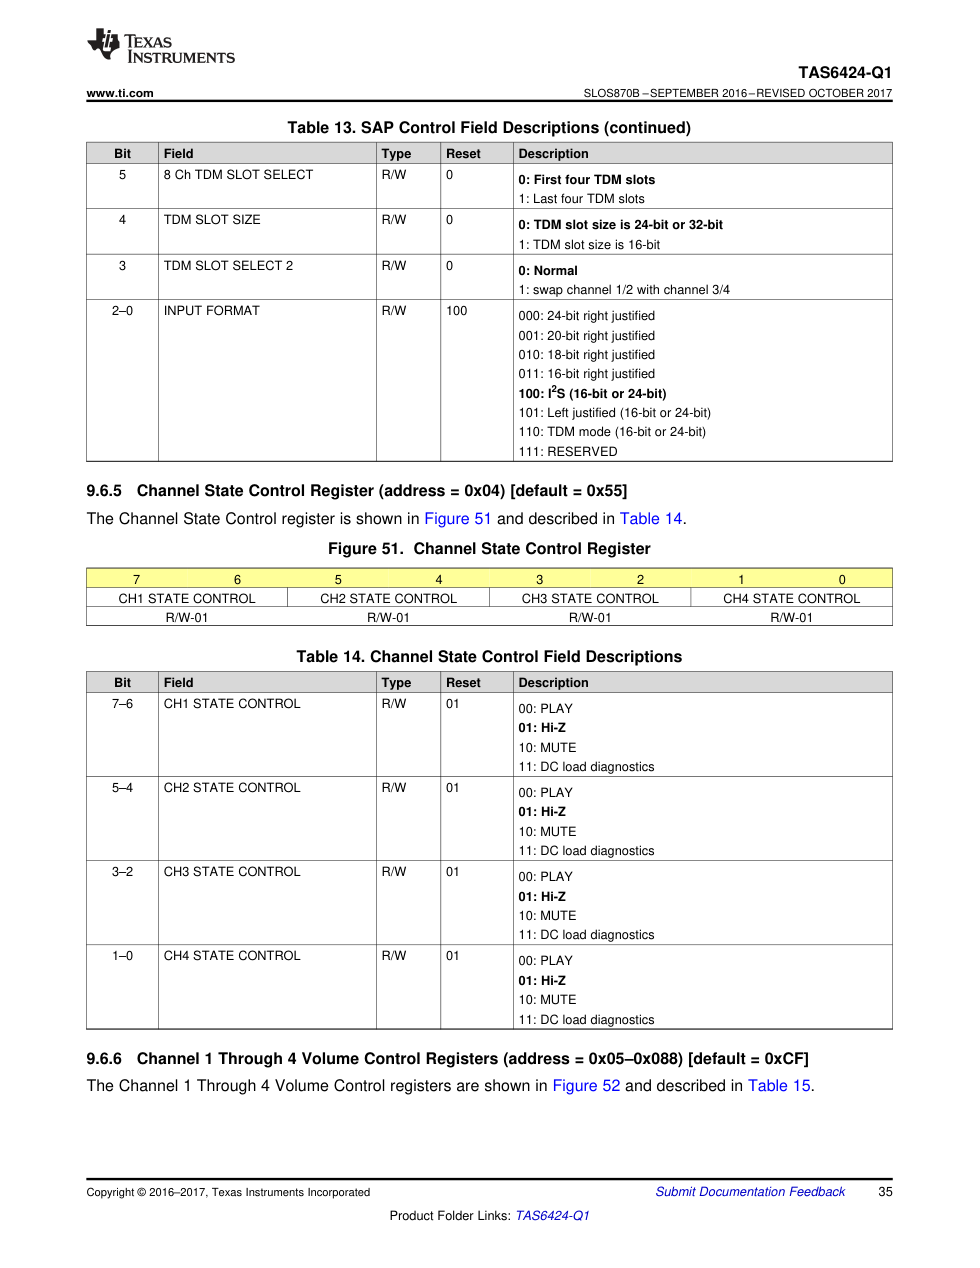
tmp/phase_1b/AMP_35.png
