RamazanBozkurrtt/circuitBuilderAi-Astra/tmp/phase_1b/DSP_44.png

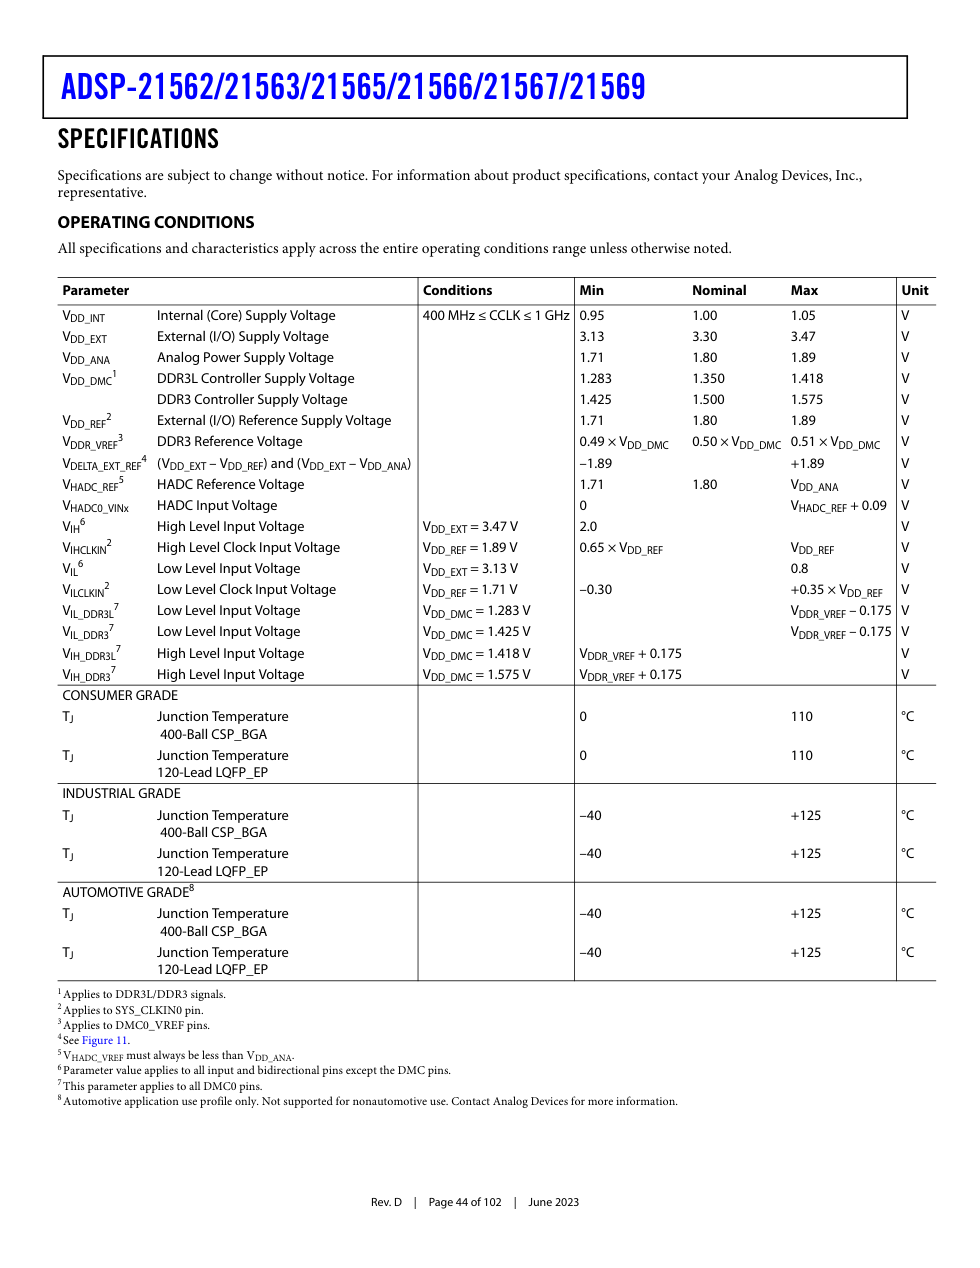
tmp/phase_1b/DSP_44.png
