RamazanBozkurrtt/circuitBuilderAi-Astra/tmp/phase_1b/DSP_47.png

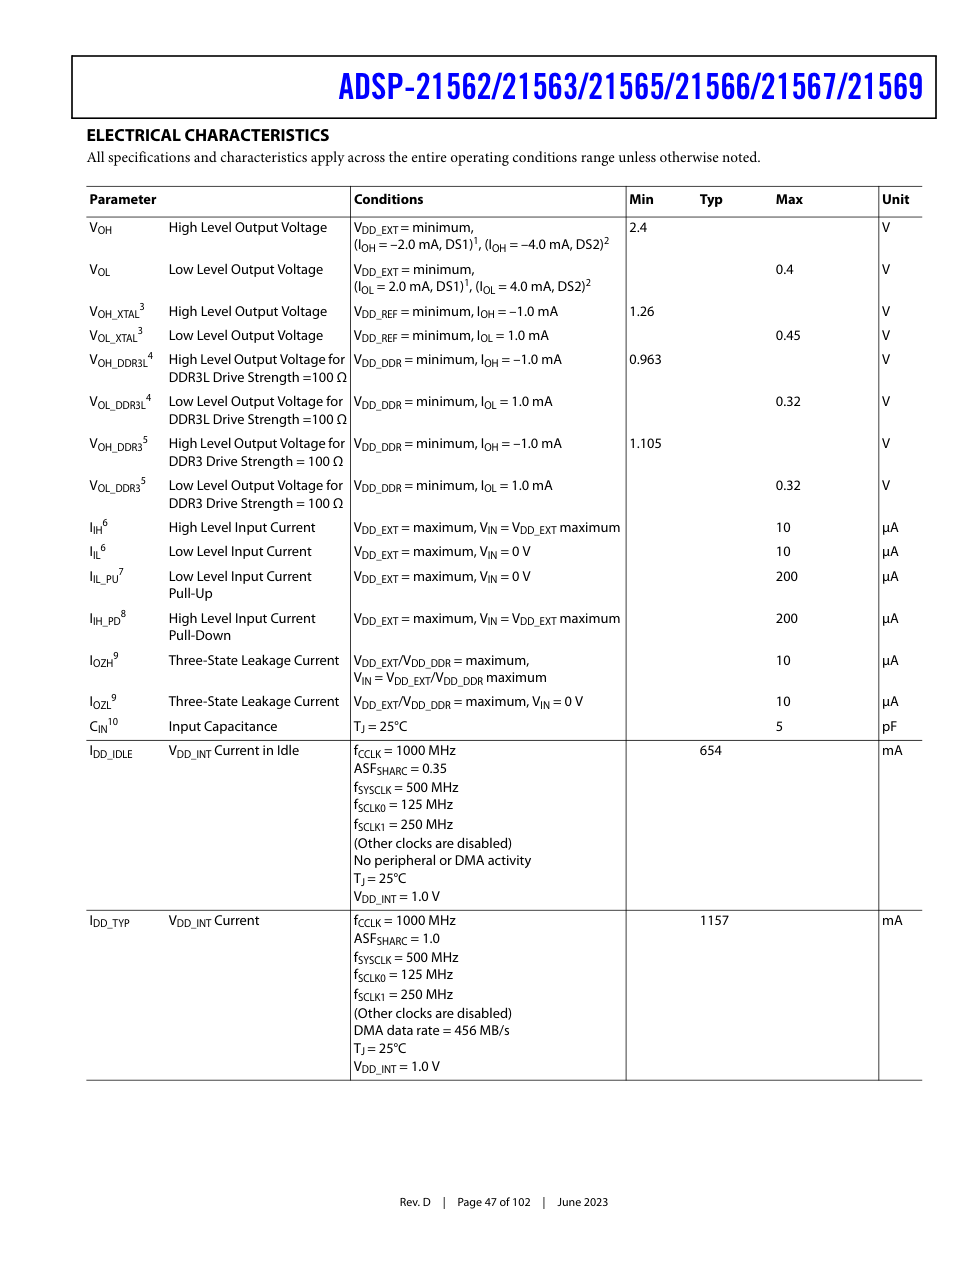
tmp/phase_1b/DSP_47.png
