RamazanBozkurrtt/circuitBuilderAi-Astra/tmp/phase_1b/DSP_49.png

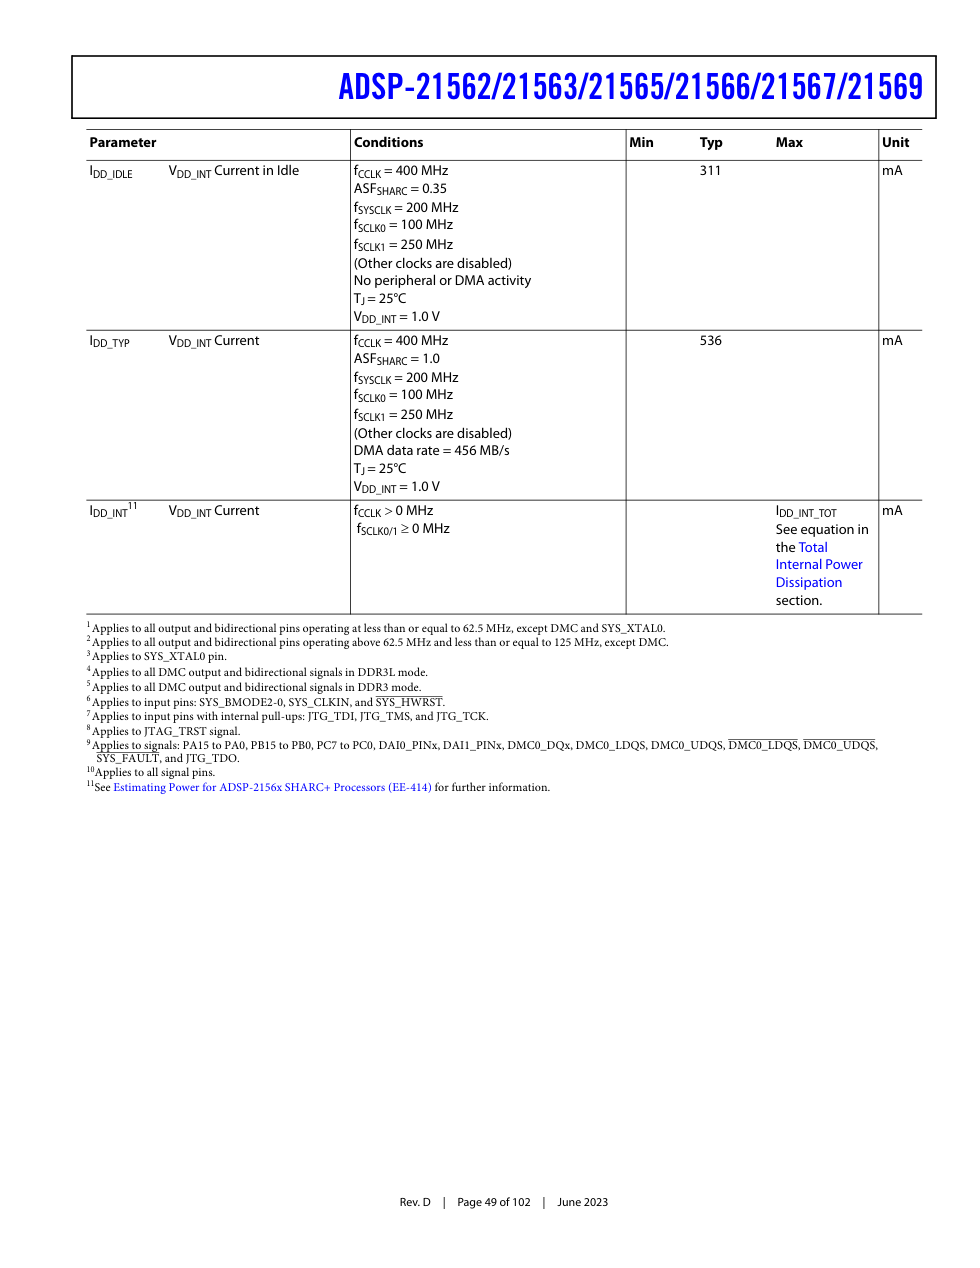
tmp/phase_1b/DSP_49.png
