RamazanBozkurrtt/circuitBuilderAi-Astra/tmp/phase_1b/DSP_52.png

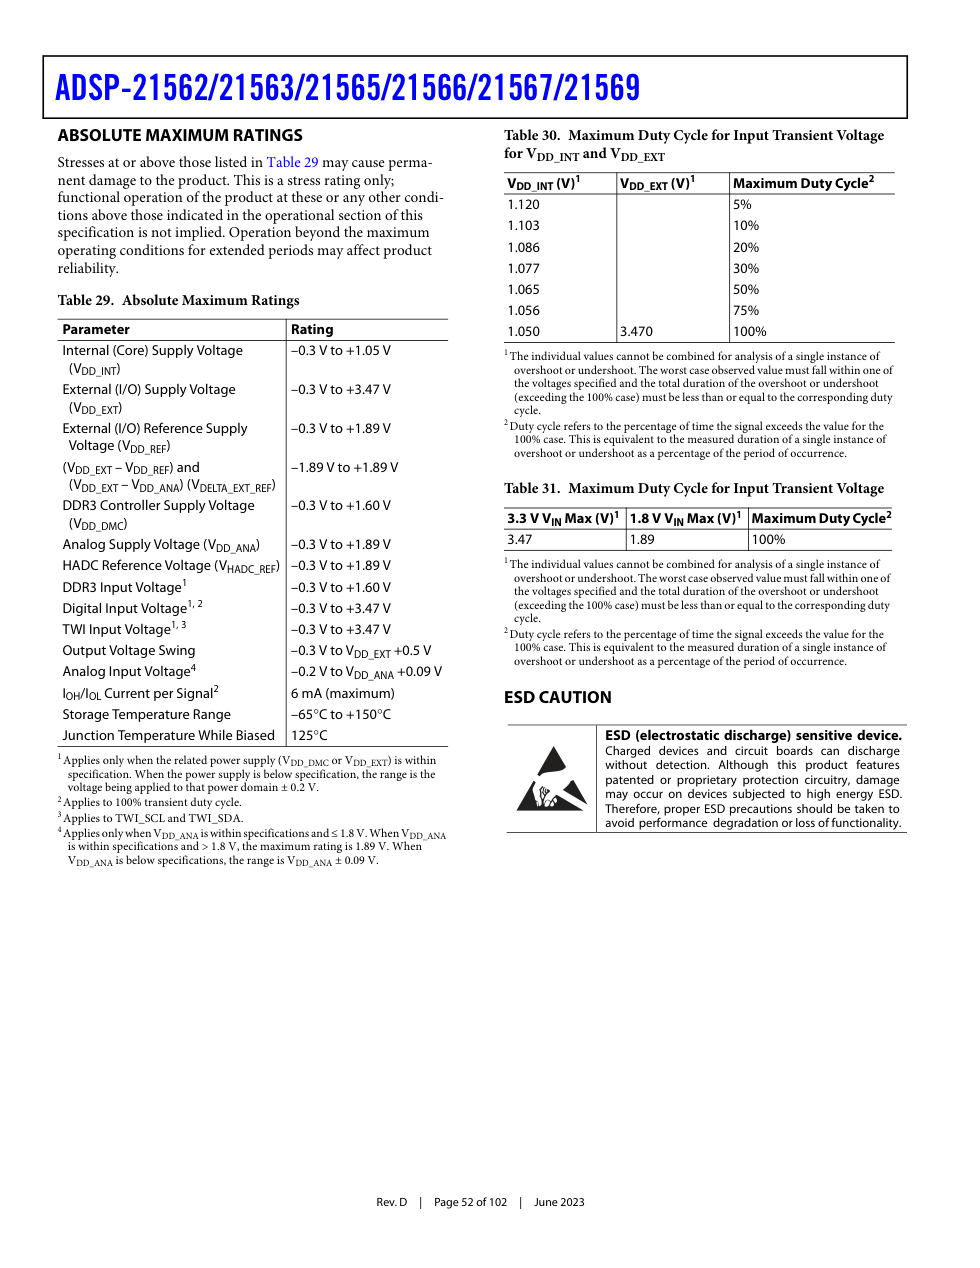
tmp/phase_1b/DSP_52.png
