RamazanBozkurrtt/circuitBuilderAi-Astra/tmp/phase_1b/DSP_57.png

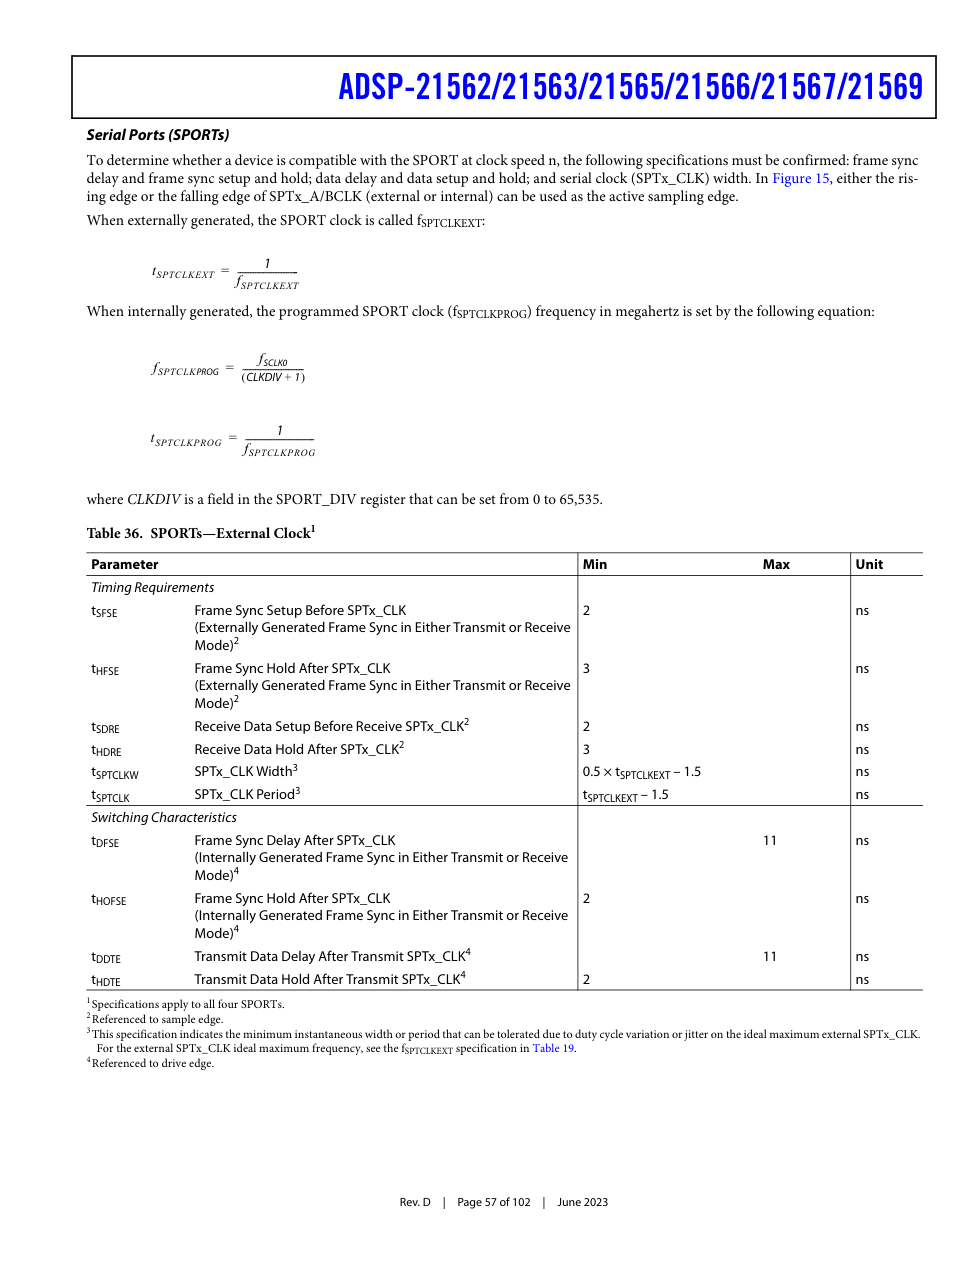
tmp/phase_1b/DSP_57.png
