RamazanBozkurrtt/circuitBuilderAi-Astra/tmp/phase_1b/DSP_58.png

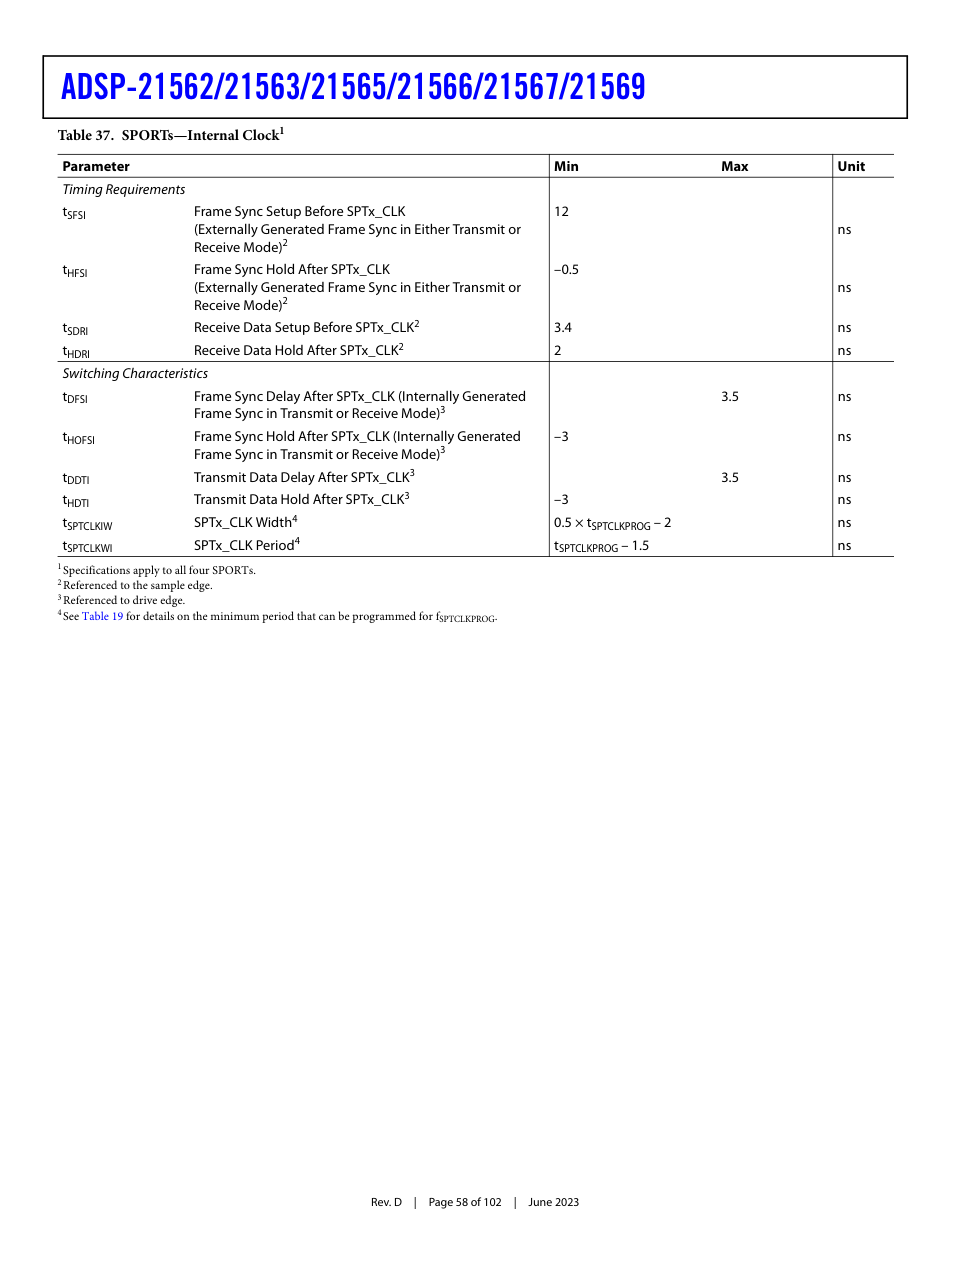
tmp/phase_1b/DSP_58.png
