RamazanBozkurrtt/circuitBuilderAi-Astra/tmp/phase_1b/DSP_73.png

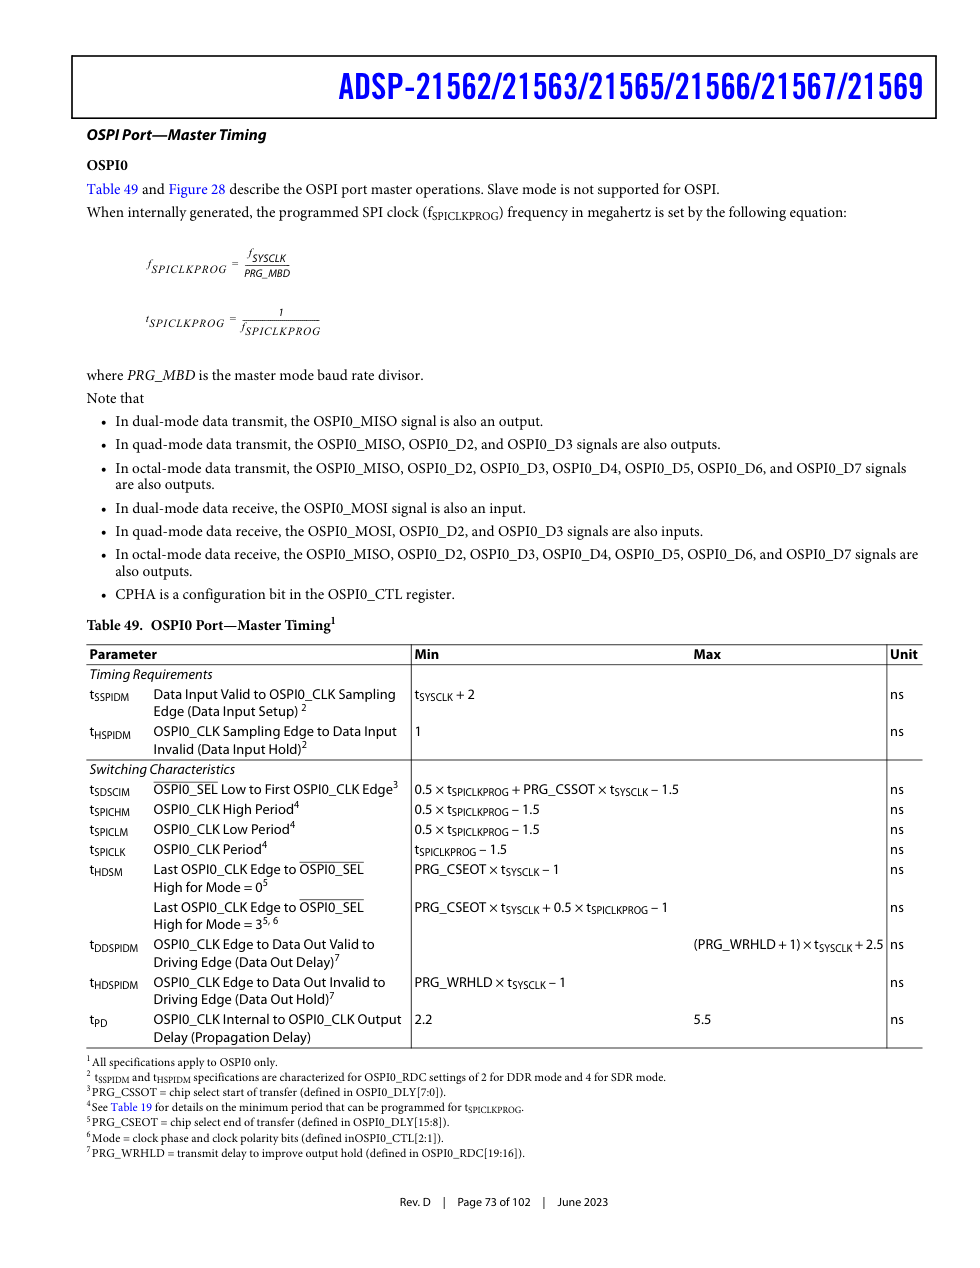
tmp/phase_1b/DSP_73.png
