RamazanBozkurrtt/circuitBuilderAi-Astra/tmp/phase_1b/DSP_75.png

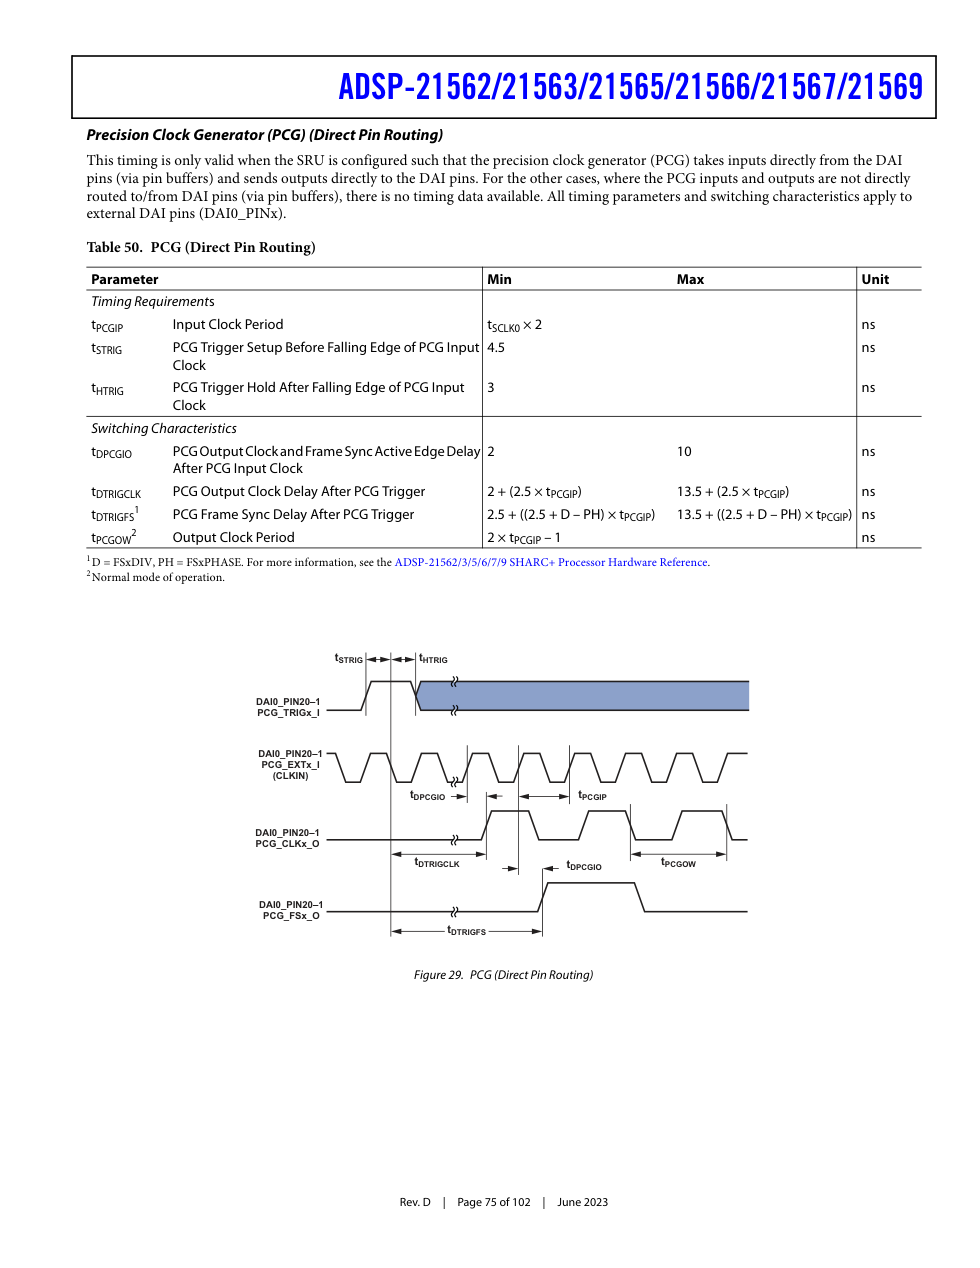
tmp/phase_1b/DSP_75.png
