RamazanBozkurrtt/circuitBuilderAi-Astra/tmp/phase_1b/DSP_87.png

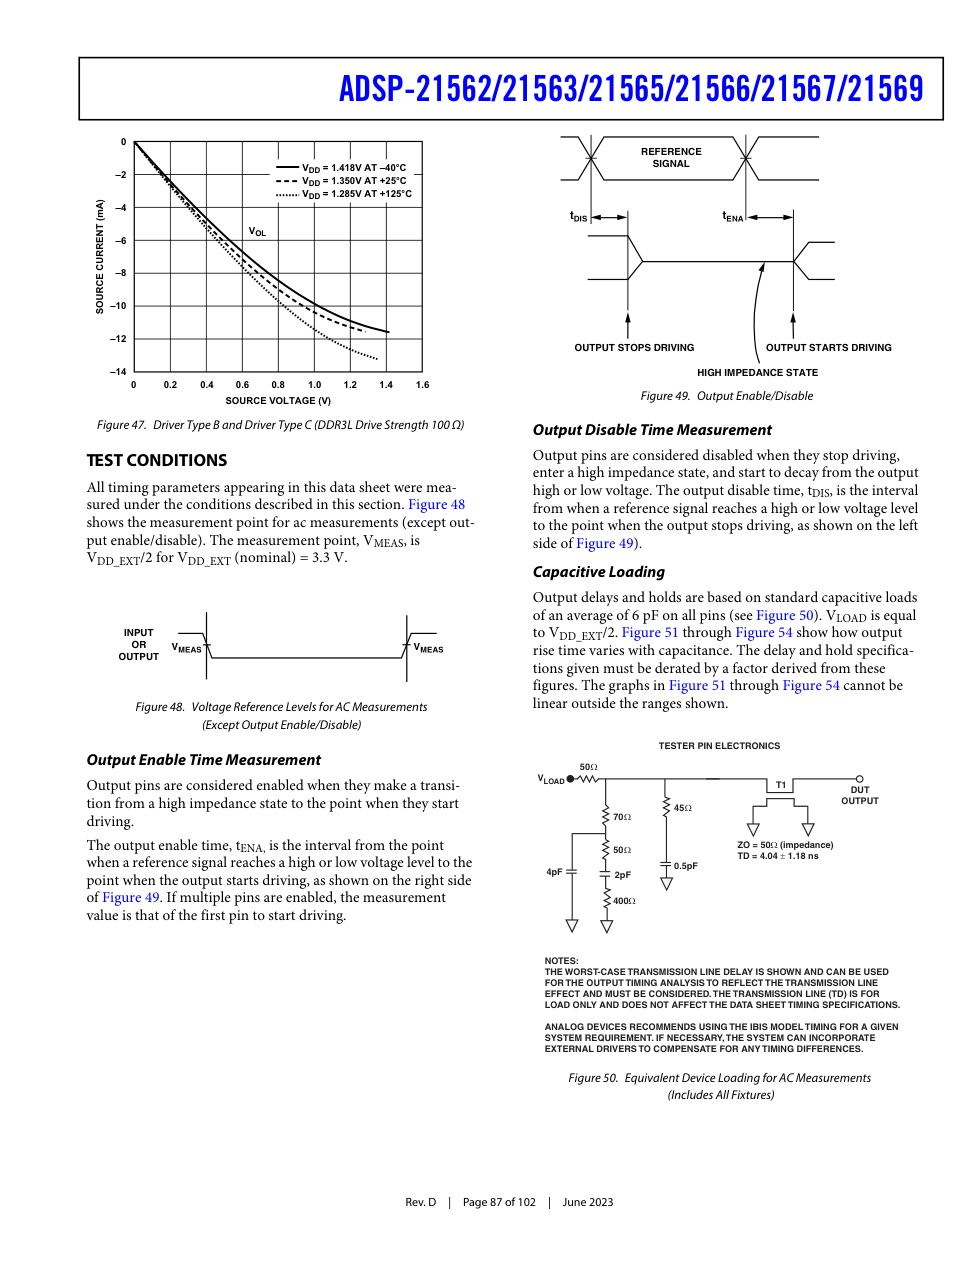
tmp/phase_1b/DSP_87.png
