RamazanBozkurrtt/circuitBuilderAi-Astra/validation/phase_3/rendered/ev-21569-som-schematic_p9.png

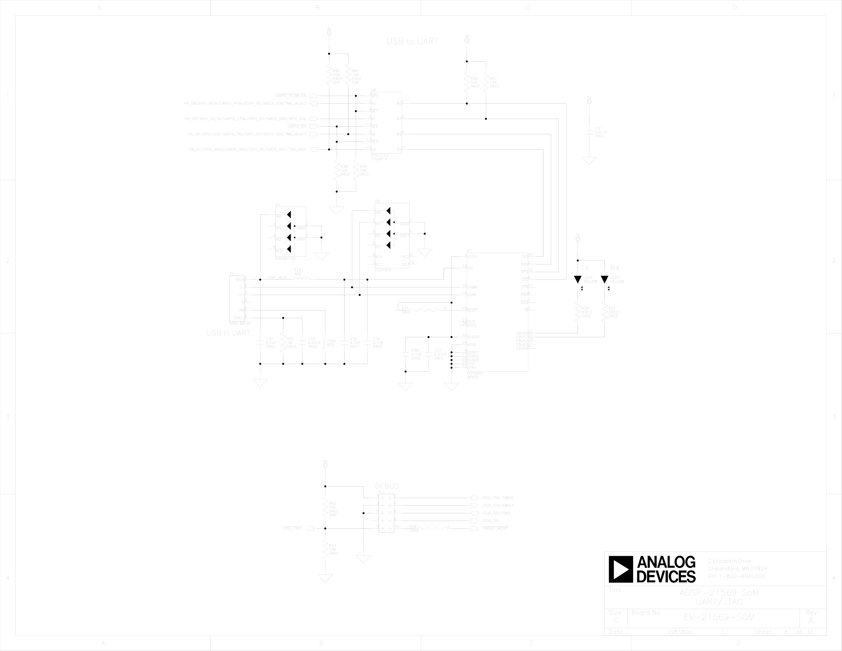
validation/phase_3/rendered/ev-21569-som-schematic_p9.png
