RamazanBozkurrtt/circuitBuilderAi-Astra/validation/phase_3/rendered/ev-21569-som-schematic_p11.png

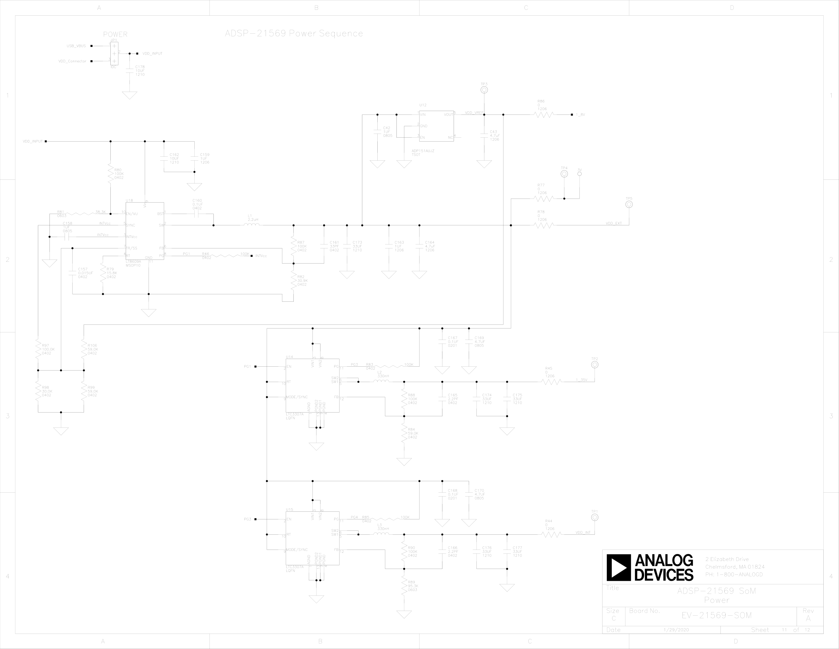
validation/phase_3/rendered/ev-21569-som-schematic_p11.png
