RamazanBozkurrtt/circuitBuilderAi-Astra/validation/phase_4b/phase3f_completion/sheet2_review.pdf

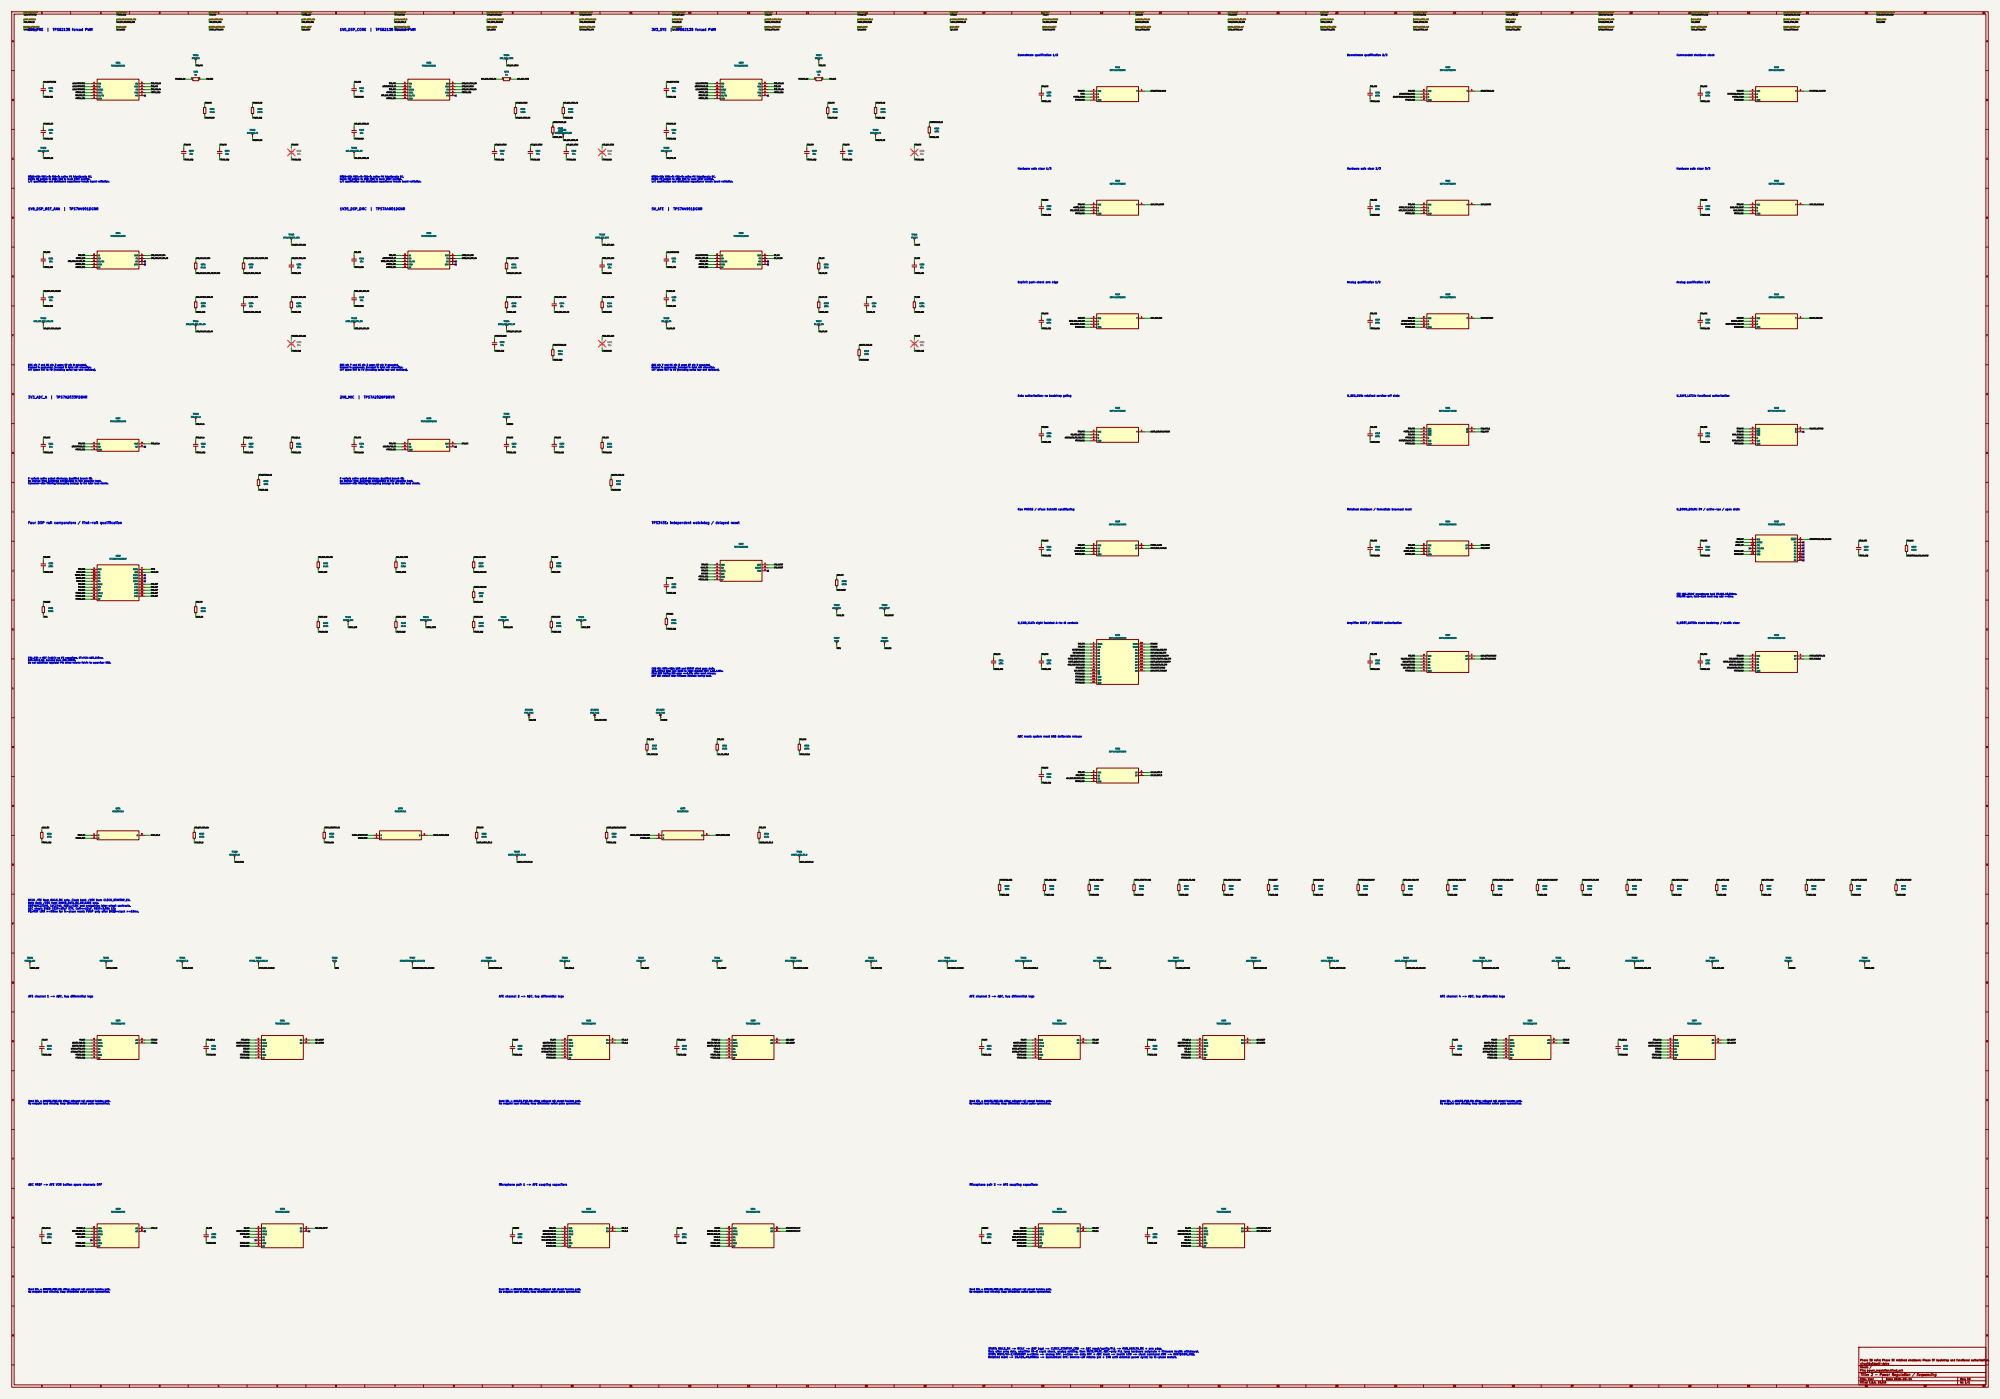
[picture p54: page 1]

AFE2N_AFTER_47R
L/C qualification and distributed capacitance remain board validation. 3V8_PRE | TPS62135 forced PWM

MODE=VIN; VSEL=0; FB2=0; native PG intentionally NC. Kelvin FB bottom to GND; VOS to local COUT positive.

L/C qualification and distributed capacitance remain board validation.

Explicit post-check arm edge

DNC pin 7 and NC pin 3 open; EP pin 9 grounded. Preload is permanent, included in total rail allocation. CFF spans OUT to FB (including series top-arm resistors). DNC pin 7 and NC pin 3 open; EP pin 9 grounded. Preload is permanent, included in total rail allocation. CFF spans OUT to FB (including series top-arm resistors).

Data authorization; no bootstrap gating

U_SEQ_RUN: retained service-off state

P variant: active output discharge. Qualified branch EN. No startup-time guarantee extrapolated to this capacitor bank. Consumer-side filtering/decoupling belongs to the later load sheets.

Raw PGOOD / eFuse Schmitt conditioning

Retained shutdown / immediate brownout reset

U_DOWN_DELAY: OV / active-low / open drain

Four DSP rail comparators / first-rail qualification

TPS3431: independent watchdog / delayed reset

CTS 198..242nF acceptance: hold 20.415..40.946ms. CTR/MR open. Cold-start reset may add <=2ms.

U_CMD_XLAT: eight isolated A-to-B controls CWD NC; SET1=VDD; WDO and ENOUT wired open drain. 330..470ms total rail-valid to reset release; WDT 1.36..1.84s. First DSP falling WDI edge <=1.13s after reset release. DSP WDI default low; firmware services during boot.

Amplifier MUTE / STANDBY authorization

U_BOOT_GATES: clock bootstrap / health clear

PG1..PG4 = REF (+ADJ); no PG capacitors. RT=VCC: 160..240ms. RST=RAILS_OK, isolated from SYS_HWRST. Do not substitute regulator PG; sense returns Kelvin to supervisor GND.

ADC reset: system reset AND deliberate release

MCLK /OE from RAILS_OK only. Clock bank /1OE from CLOCK_STARTUP_EN.
Data bank /2OE from AUDIO_DATA_OE_RELEASE only.
SN74AXC2T245, LVC244A, ASDLJ/LMK and endpoints: later-sheet contracts.
ADC sheet: DVDD CEXT=10uF X7R, Ceff<=12uF, REXT=3.00k 1%;
PD/RST LOW >=50ms for in-place reset; PWUP only after DVDD+clock >=10ms.

AFE channel 1 -> ADC, two differential legs

AFE channel 2 -> ADC, two differential legs

AFE channel 3 -> ADC, two differential legs

AFE channel 4 -> ADC, two differential legs

Used SEL = ANALOG_PWR_EN; either adjacent rail absent isolates path. No endpoint load circuitry. Keep differential switch paths symmetrical.

ADC VREF -> AFE VCM buffer; spare channels OFF

Microphone pair 1 -> AFE coupling capacitors

Microphone pair 2 -> AFE coupling capacitors

START: RAILS_OK -> MCLK -> DSP boot -> CLOCK_STARTUP_CMD -> ADC reset/config/PLL -> RUN_HEALTH_OK + arm edge.
Only after arm: data, amplifier Hi-Z clock check, analog settling, then MUTE/PLAY. ADC-only PLL loss: hardware automute + firmware health withdrawal.
STOP: MUTE/Hi-Z/STANDBY >=15ms -> analog OFF, >=1ms -> data OFF + ADC reset -> health LOW -> clock command LOW -> SHUTDOWN_REQ.
Retained reset -> 20.415..40.946ms -> downstream OFF. Service-off retains pre + 1V8 until external power cycle; no in-place restart.

Phase 3D rails; Phase 3E retained shutdown; Phase 3F bootstrap and functional authorization.
circuitBuilderAi-Astra
Sheet: /
File: power_regulation.kicad_sch
Title: 2 - Power Regulation / Sequencing

Size: User | Rev: 4B
KiCad E.D.A. 10.0.6 | Id: 1/1
