RamazanBozkurrtt/circuitBuilderAi-Astra/validation/phase_4a/transient_trace.csv

time_s | IN_SYS_V | protected_V | sense_V | PG_nom_V | PG_high_V | PG_low_V | UVLO_enabled | safe_request
1e-06 | 0.0 | 0.0 | 0.0 | 0.0 | 0.0 | 0.0 | 9.99999999e-10 | 1.0
0.0001448 | 0.0 | 0.0 | 0.0 | 0.0 | 0.0 | 0.0 | 9.99999999e-10 | 1.0
0.001096 | 0.0 | 0.0 | 0.0 | 0.0 | 0.0 | 0.0 | 9.99999999e-10 | 1.0
0.002096 | 0.0 | 0.0 | 0.0 | 0.0 | 0.0 | 0.0 | 9.99999999e-10 | 1.0
0.003096 | 0.0 | 0.0 | 0.0 | 0.0 | 0.0 | 0.0 | 9.99999999e-10 | 1.0
0.004096 | 0.0 | 0.0 | 0.0 | 0.0 | 0.0 | 0.0 | 9.99999999e-10 | 1.0
0.005096 | 0.0 | 0.0 | 0.0 | 0.0 | 0.0 | 0.0 | 9.99999999e-10 | 1.0
0.006096 | 0.0 | 0.0 | 0.0 | 0.0 | 0.0 | 0.0 | 9.99999999e-10 | 1.0
0.007096 | 0.0 | 0.0 | 0.0 | 0.0 | 0.0 | 0.0 | 9.99999999e-10 | 1.0
0.008096 | 0.0 | 0.0 | 0.0 | 0.0 | 0.0 | 0.0 | 9.99999999e-10 | 1.0
0.009096 | 0.0 | 0.0 | 0.0 | 0.0 | 0.0 | 0.0 | 9.99999999e-10 | 1.0
0.01 | 0.0 | 0.0 | 0.0 | 0.0 | 0.0 | 0.0 | 9.99999999e-10 | 1.0
0.01075 | 0.075 | 0.0 | 0.0 | 0.0 | 0.0 | 0.0 | 9.99999999e-10 | 1.0
0.01175 | 0.175 | 0.0 | 0.0 | 0.0 | 0.0 | 0.0 | 9.99999999e-10 | 1.0
0.01275 | 0.275 | 0.0 | 0.0 | 0.0 | 0.0 | 0.0 | 9.99999999e-10 | 1.0
0.01375 | 0.375 | 0.0 | 0.0 | 0.0 | 0.0 | 0.0 | 9.99999999e-10 | 1.0
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
