RamazanBozkurrtt/circuitBuilderAi-Astra/validation/phase_3/rendered/asdlj_datasheet_rev_a_p1.png

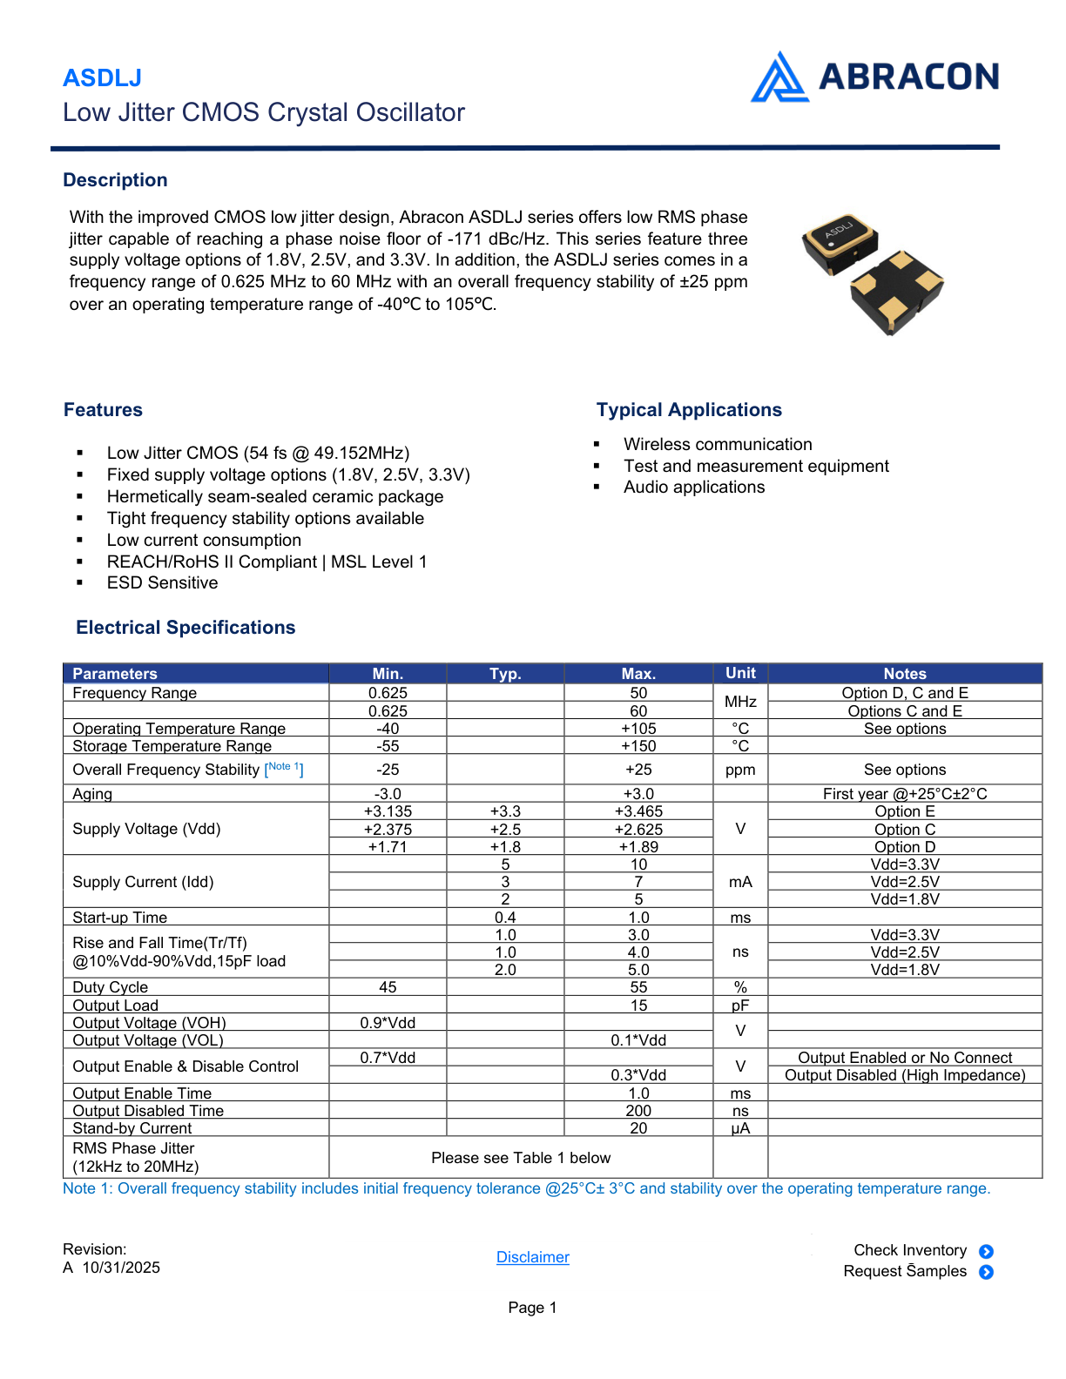
validation/phase_3/rendered/asdlj_datasheet_rev_a_p1.png
