RamazanBozkurrtt/circuitBuilderAi-Astra/validation/phase_3/rendered/asdlj_datasheet_rev_a_p4.png

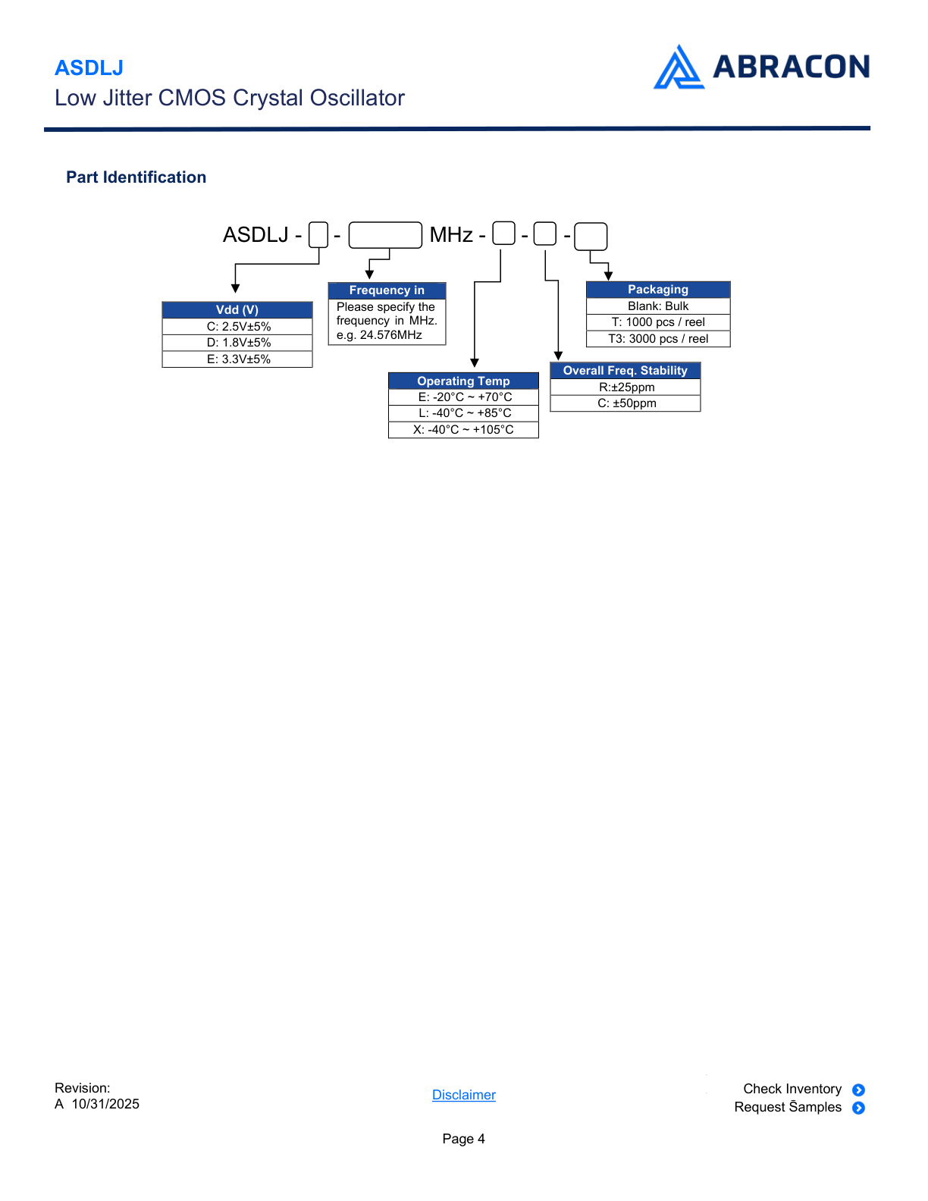
validation/phase_3/rendered/asdlj_datasheet_rev_a_p4.png
