RamazanBozkurrtt/circuitBuilderAi-Astra/validation/phase_3/rendered/ee-68_p10.png

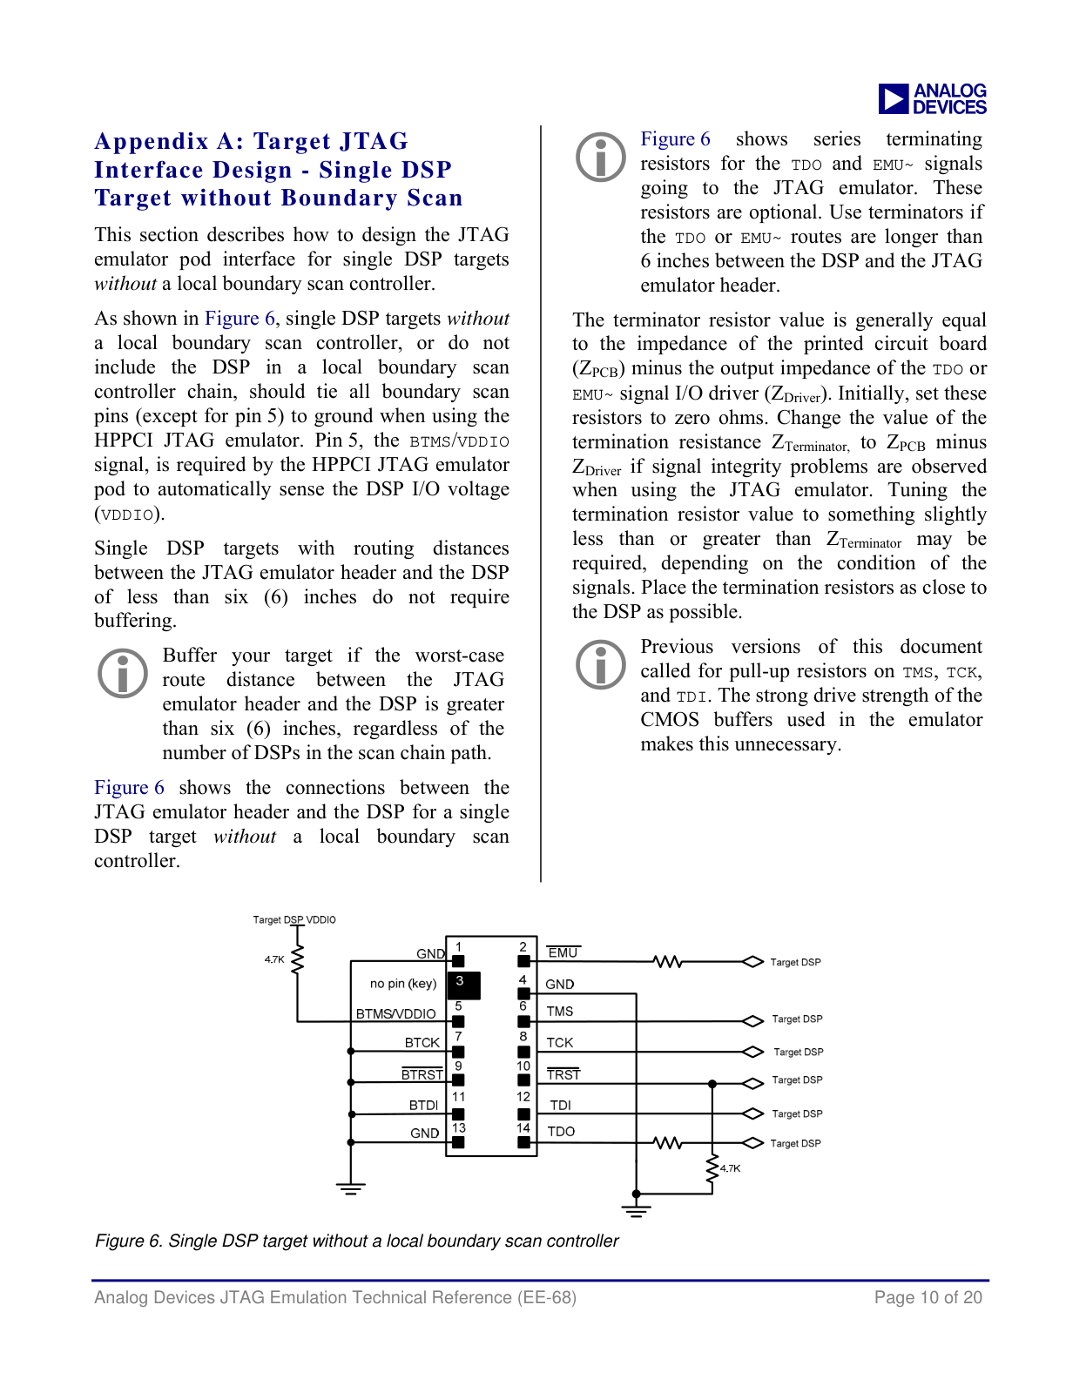
validation/phase_3/rendered/ee-68_p10.png
