RamazanBozkurrtt/circuitBuilderAi-Astra/validation/phase_3/rendered/lmk1c1103_datasheet_rev_d_p8.png

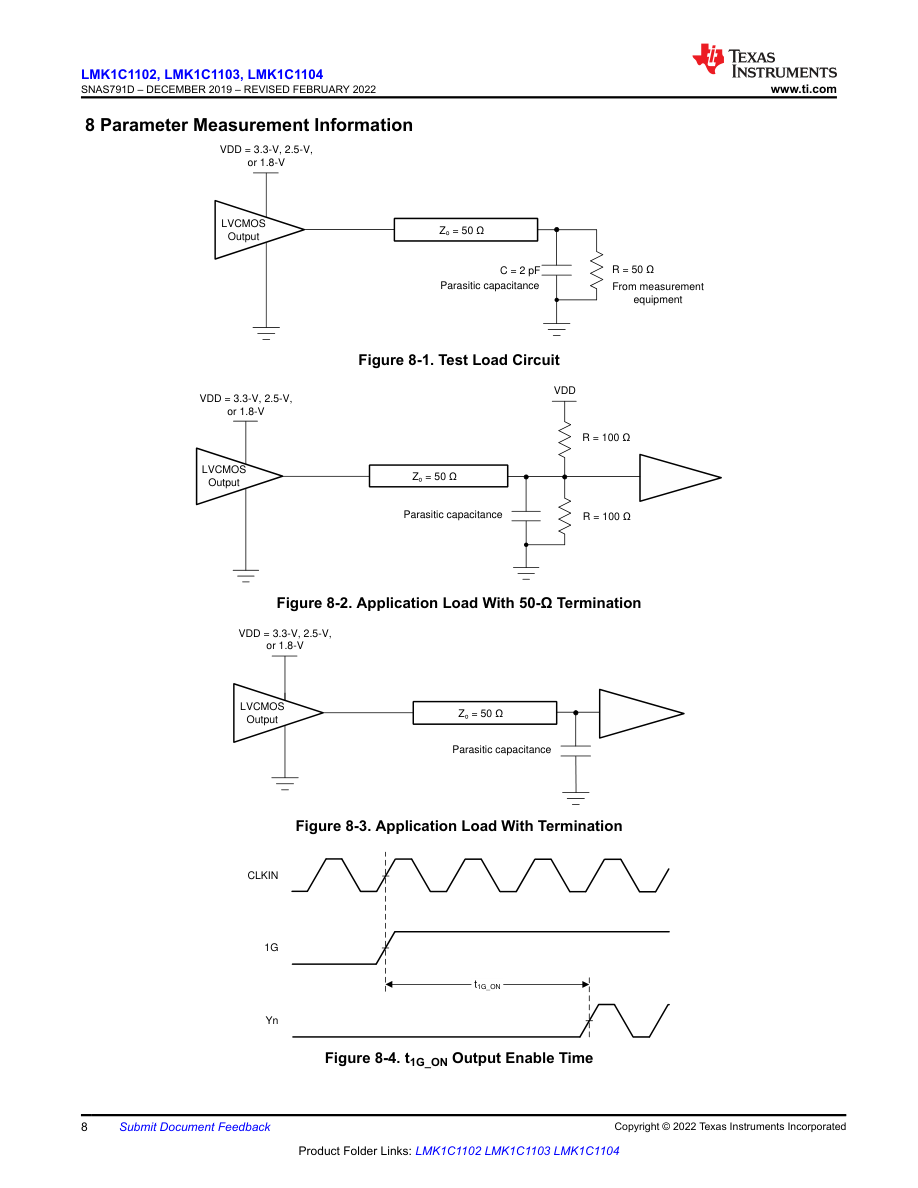
validation/phase_3/rendered/lmk1c1103_datasheet_rev_d_p8.png
