RamazanBozkurrtt/circuitBuilderAi-Astra/validation/phase_3/rendered/tas6424e-q1_datasheet_rev_a_p40.png

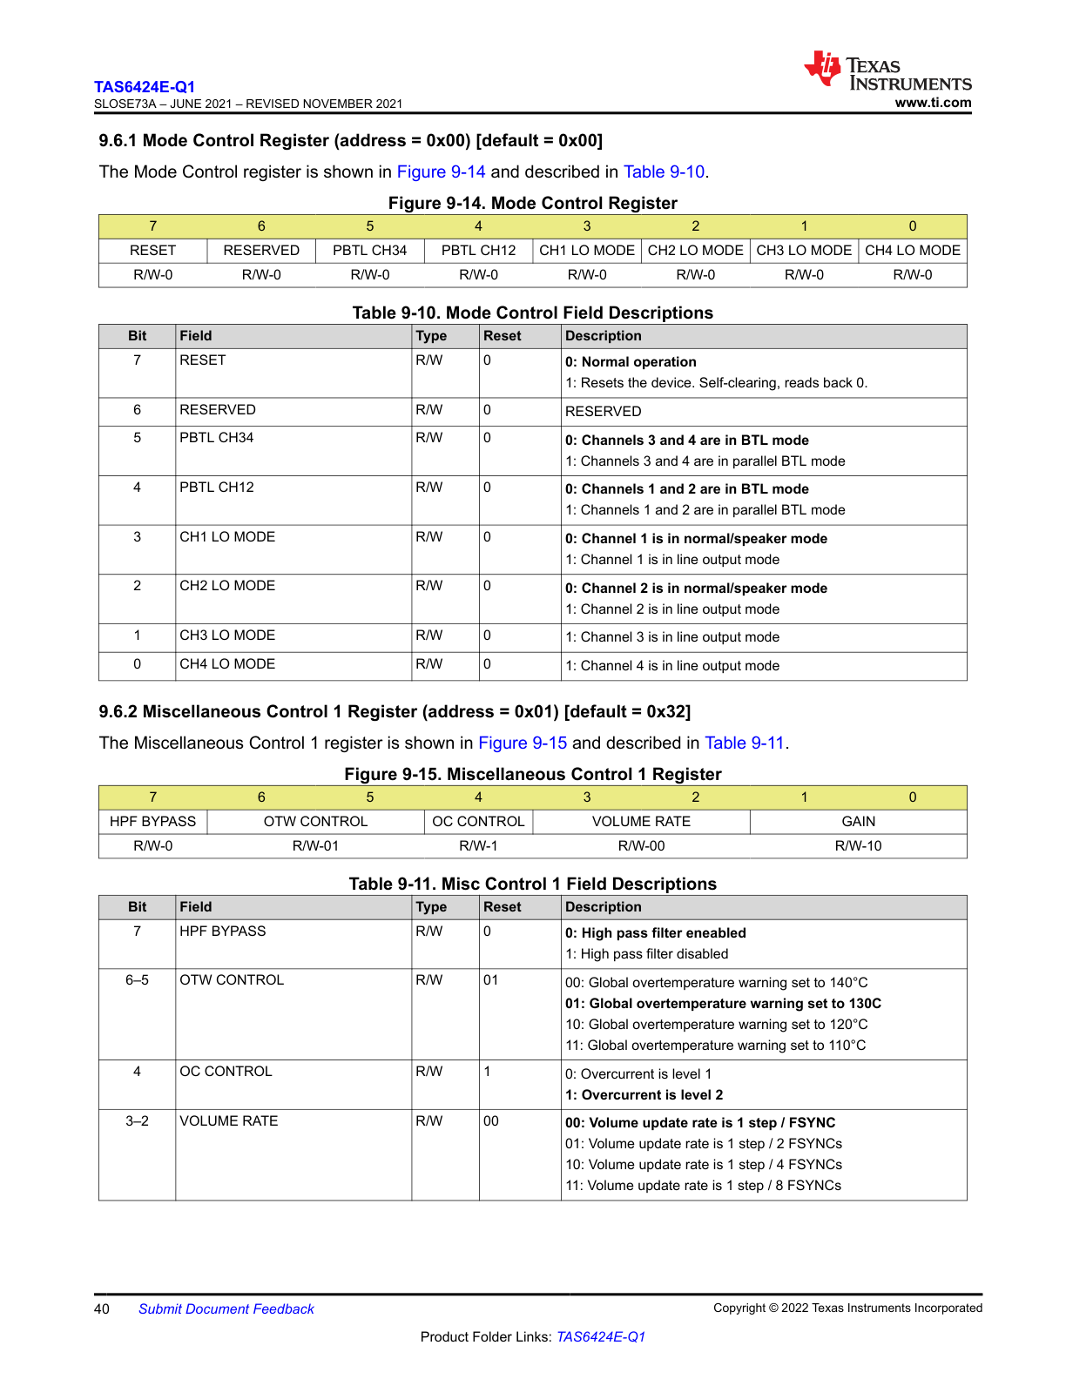
validation/phase_3/rendered/tas6424e-q1_datasheet_rev_a_p40.png
