RamazanBozkurrtt/circuitBuilderAi-Astra/validation/phase_3/rendered/tps386000_datasheet_rev_f_p27.png

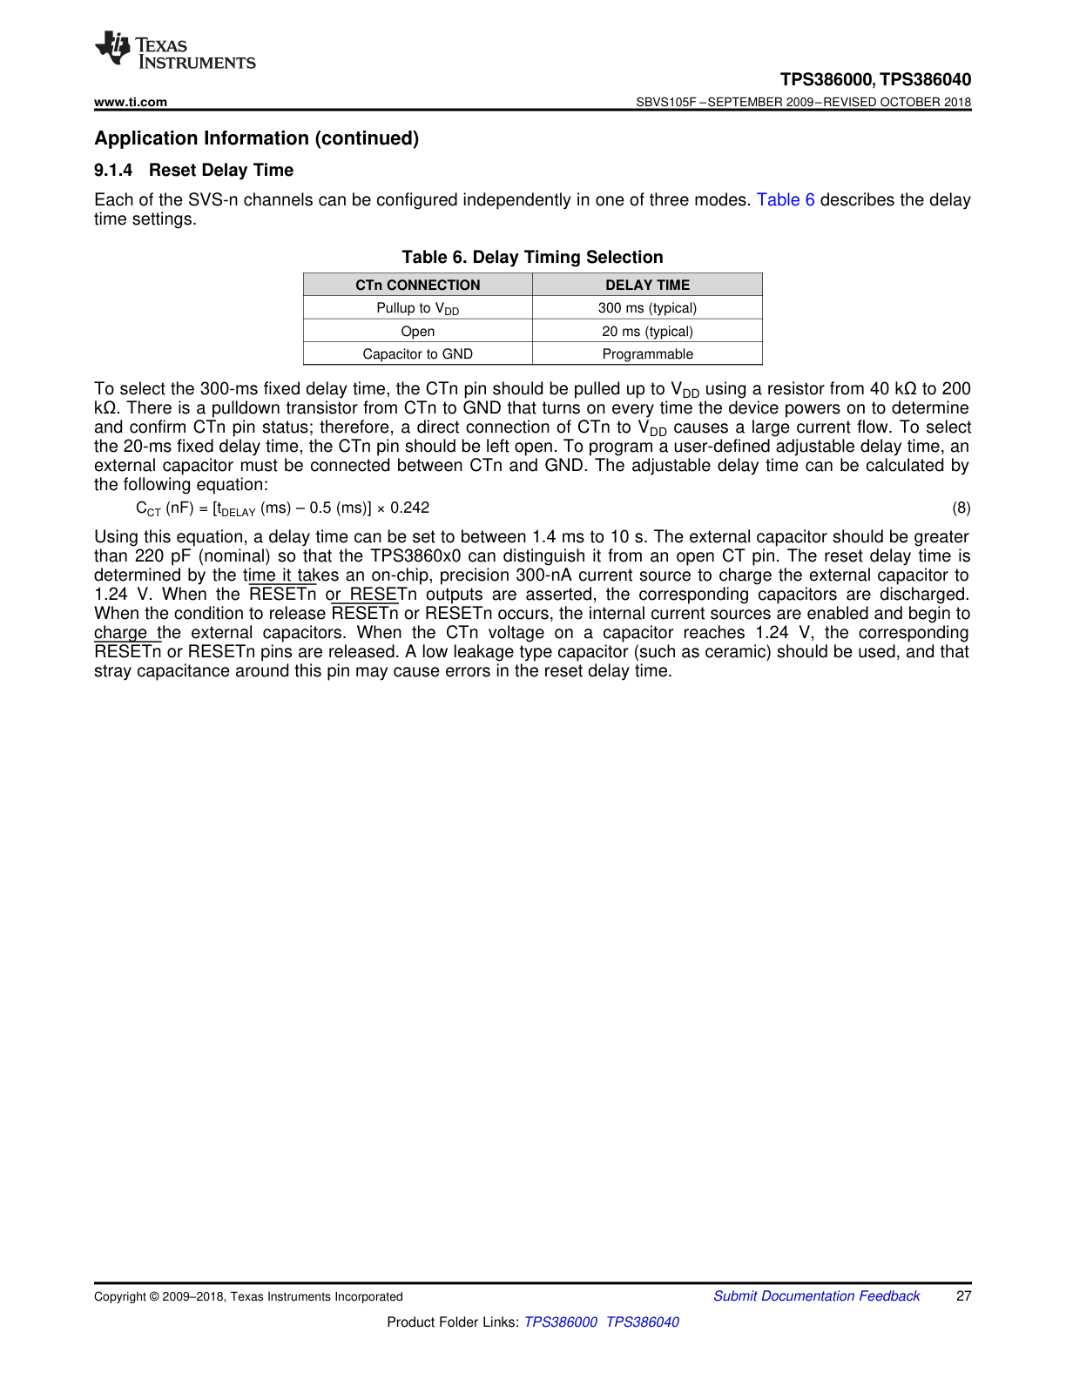
validation/phase_3/rendered/tps386000_datasheet_rev_f_p27.png
