RamazanBozkurrtt/circuitBuilderAi-Astra/validation/phase_4b/phase3f_completion/control_detail_review.png

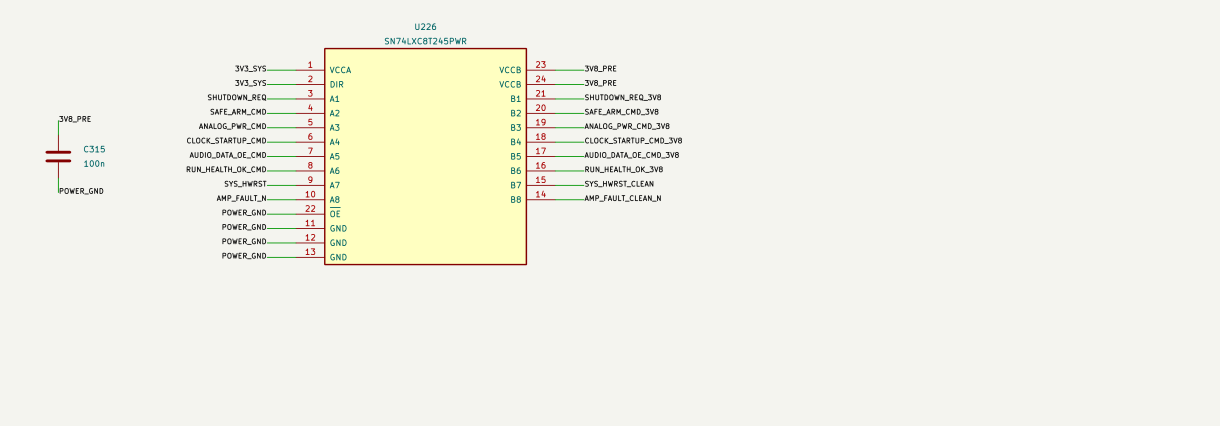
validation/phase_4b/phase3f_completion/control_detail_review.png
