RamazanBozkurrtt/circuitBuilderAi-Astra/validation/phase_4b/phase3f_completion/logic_review.png

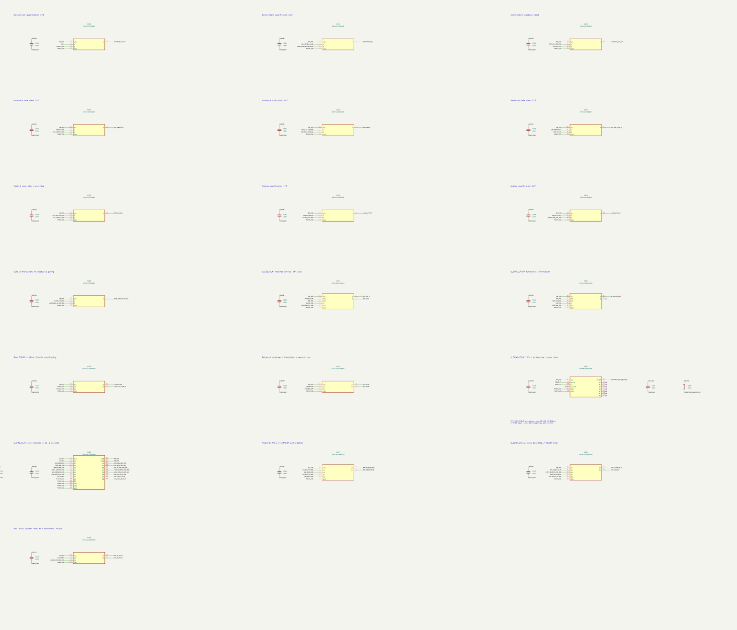
validation/phase_4b/phase3f_completion/logic_review.png
