RamazanBozkurrtt/circuitBuilderAi-Astra/validation/phase_4b/tps7a49_impl_p4.png

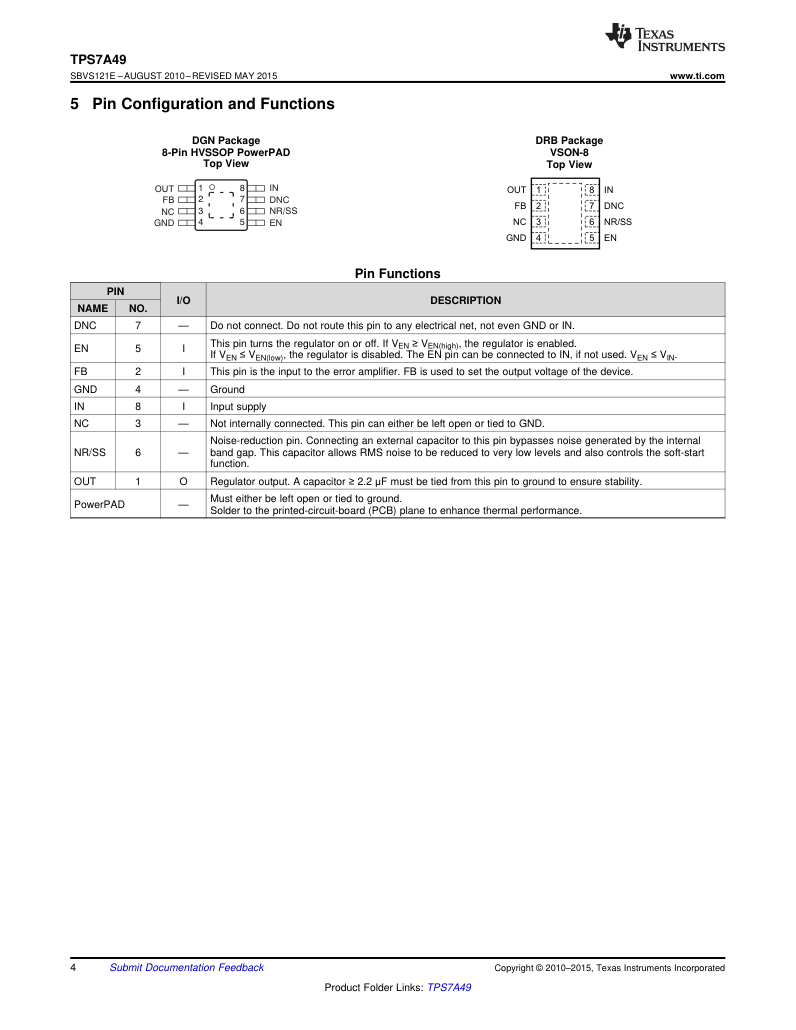
validation/phase_4b/tps7a49_impl_p4.png
