RamazanBozkurrtt/circuitBuilderAi-Astra/validation/phase_4b/tps3431_impl_p28.png

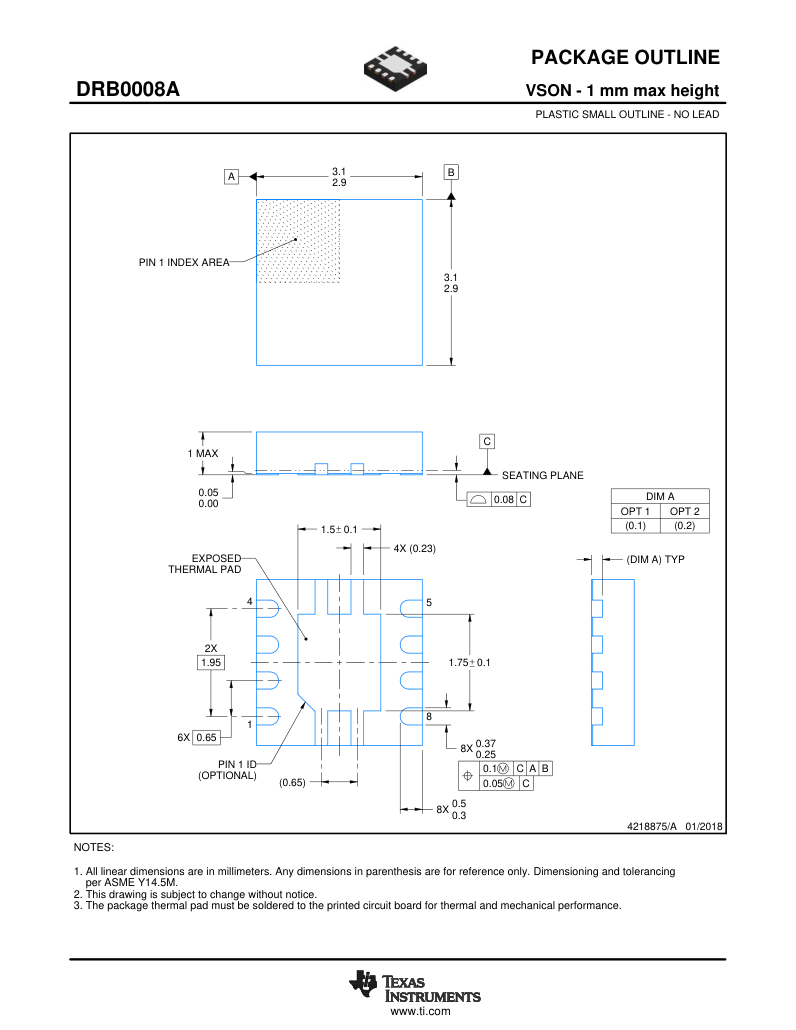
validation/phase_4b/tps3431_impl_p28.png
