RamazanBozkurrtt/circuitBuilderAi-Astra/validation/phase_4b/tps62135_impl_p3.png

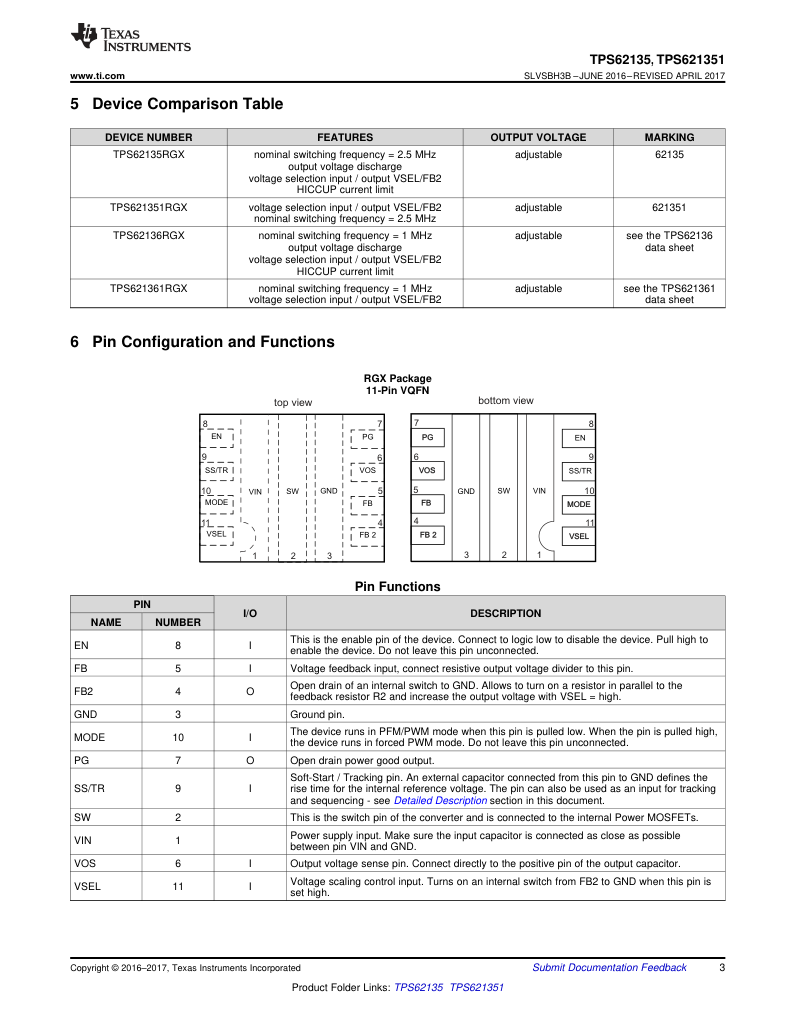
validation/phase_4b/tps62135_impl_p3.png
