RamazanBozkurrtt/circuitBuilderAi-Astra/validation/phase_4b/tps62135_impl_p45.png

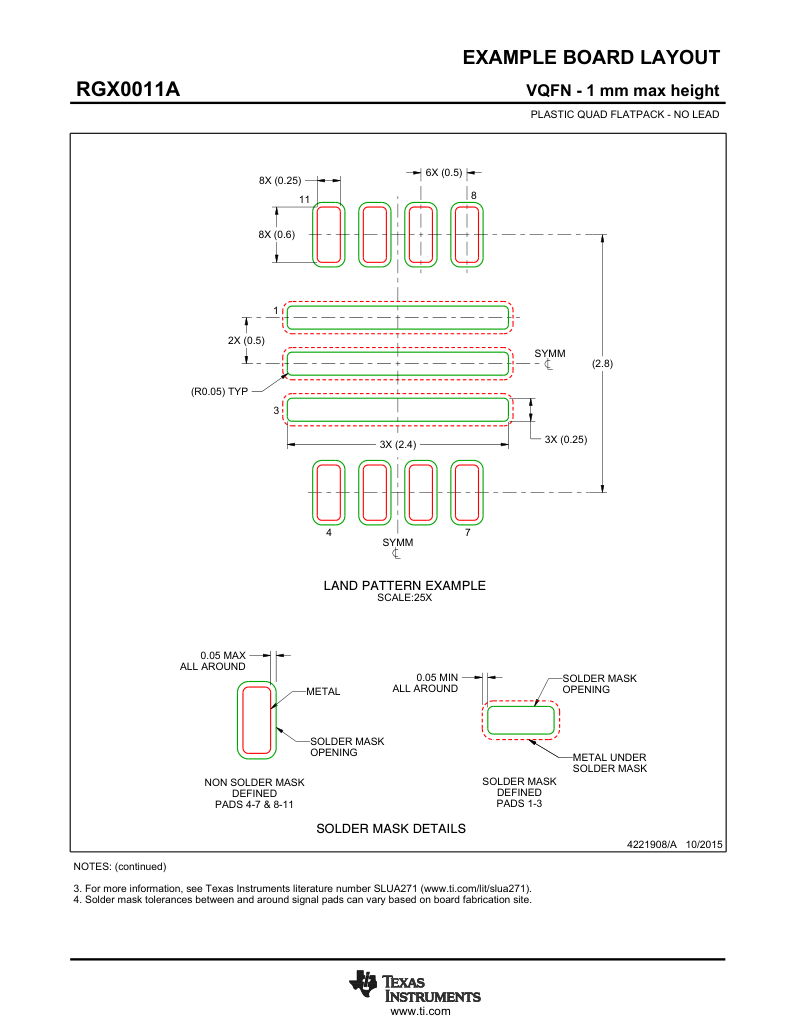
validation/phase_4b/tps62135_impl_p45.png
