RamazanBozkurrtt/circuitBuilderAi-Astra/validation/phase_4b/tps62135_p6.png

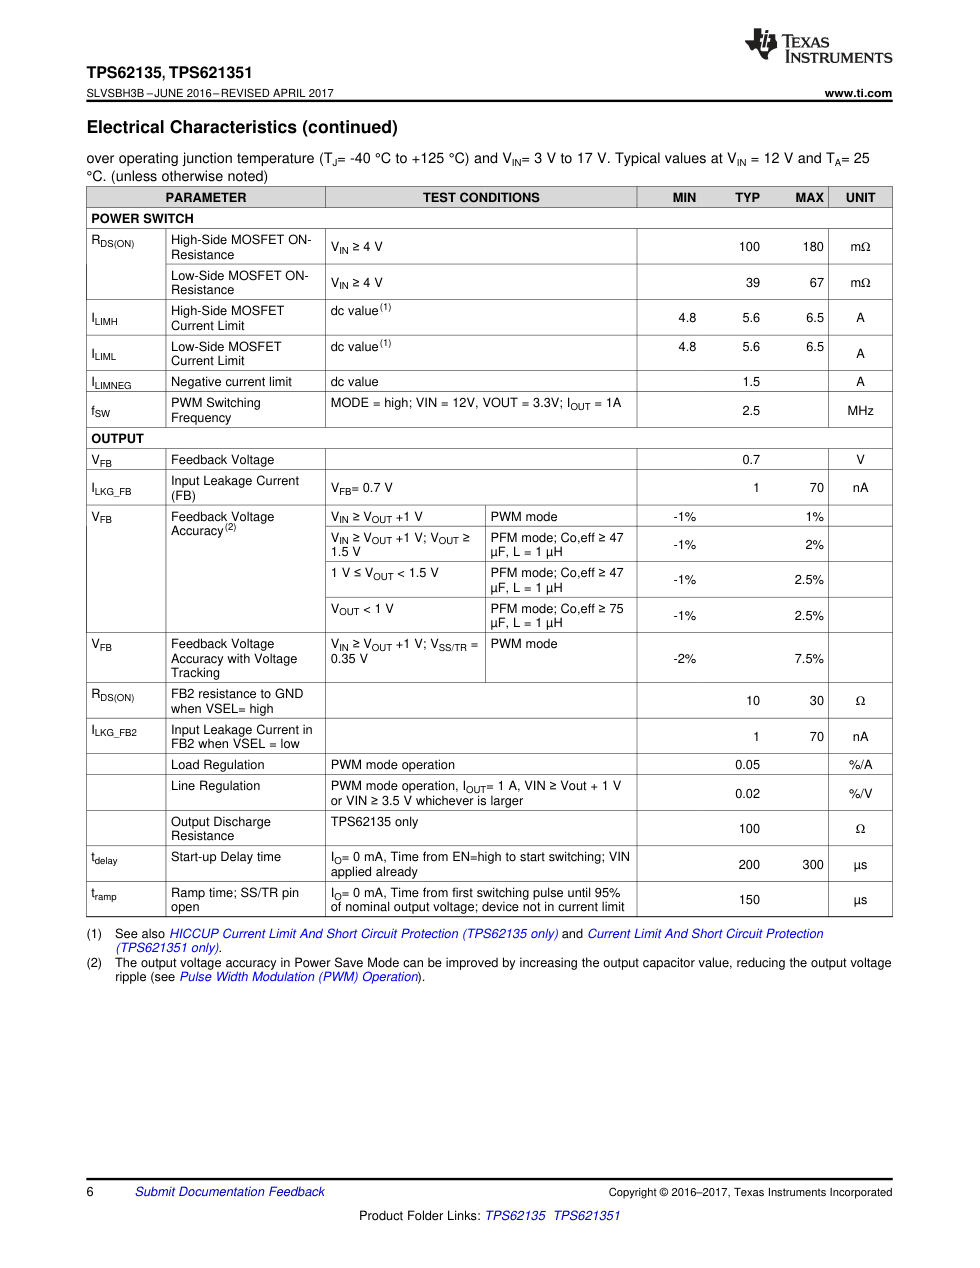
validation/phase_4b/tps62135_p6.png
