RamazanBozkurrtt/circuitBuilderAi-Astra/validation/phase_4b/tps386000_p9.png

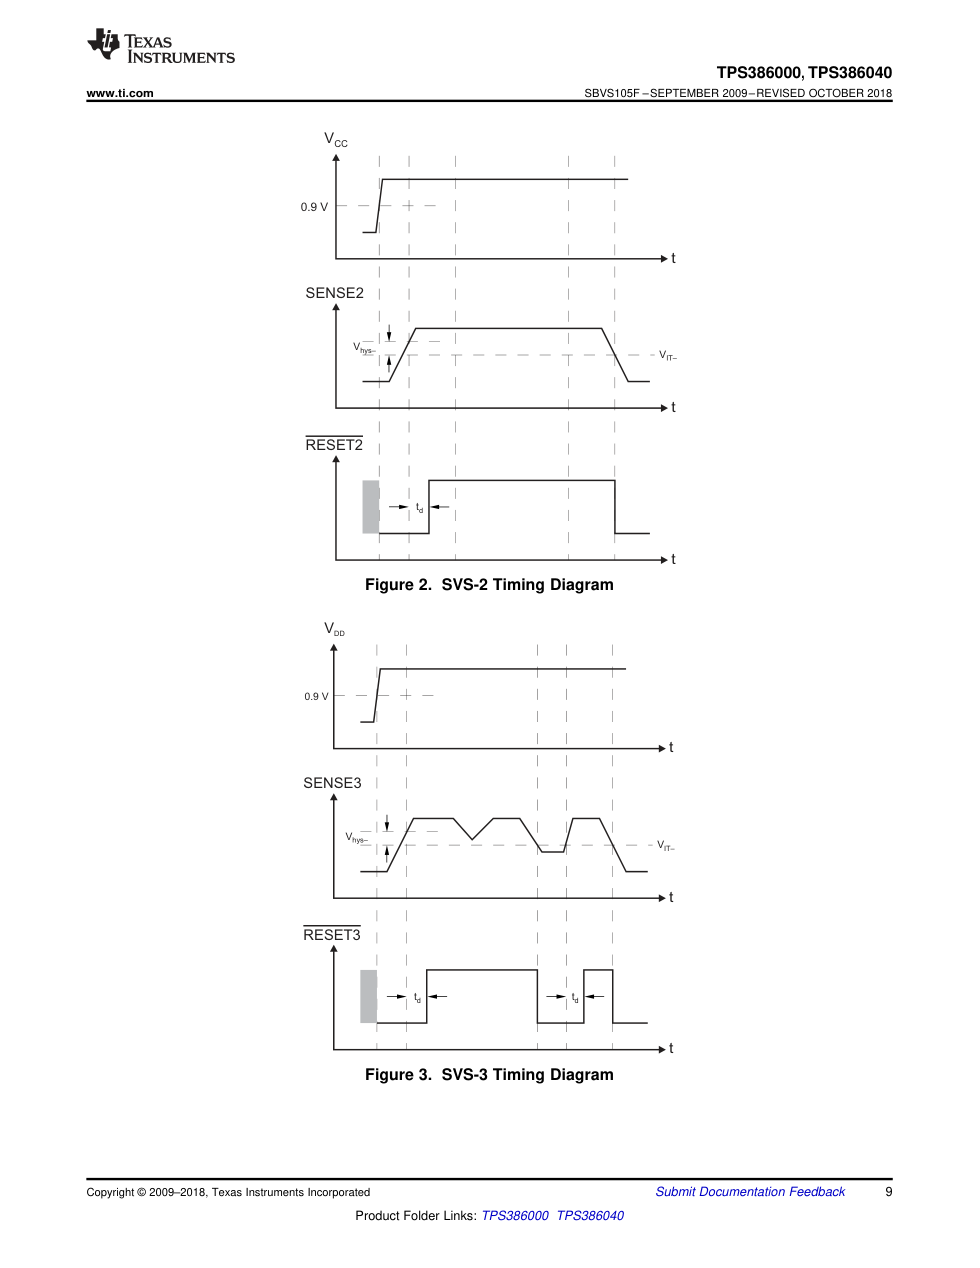
validation/phase_4b/tps386000_p9.png
