RamazanBozkurrtt/circuitBuilderAi-Astra/hardware/kicad/power_input.kicad_sch

## KiCad design hardware/kicad/power_input.kicad_sch (2026-09-09)

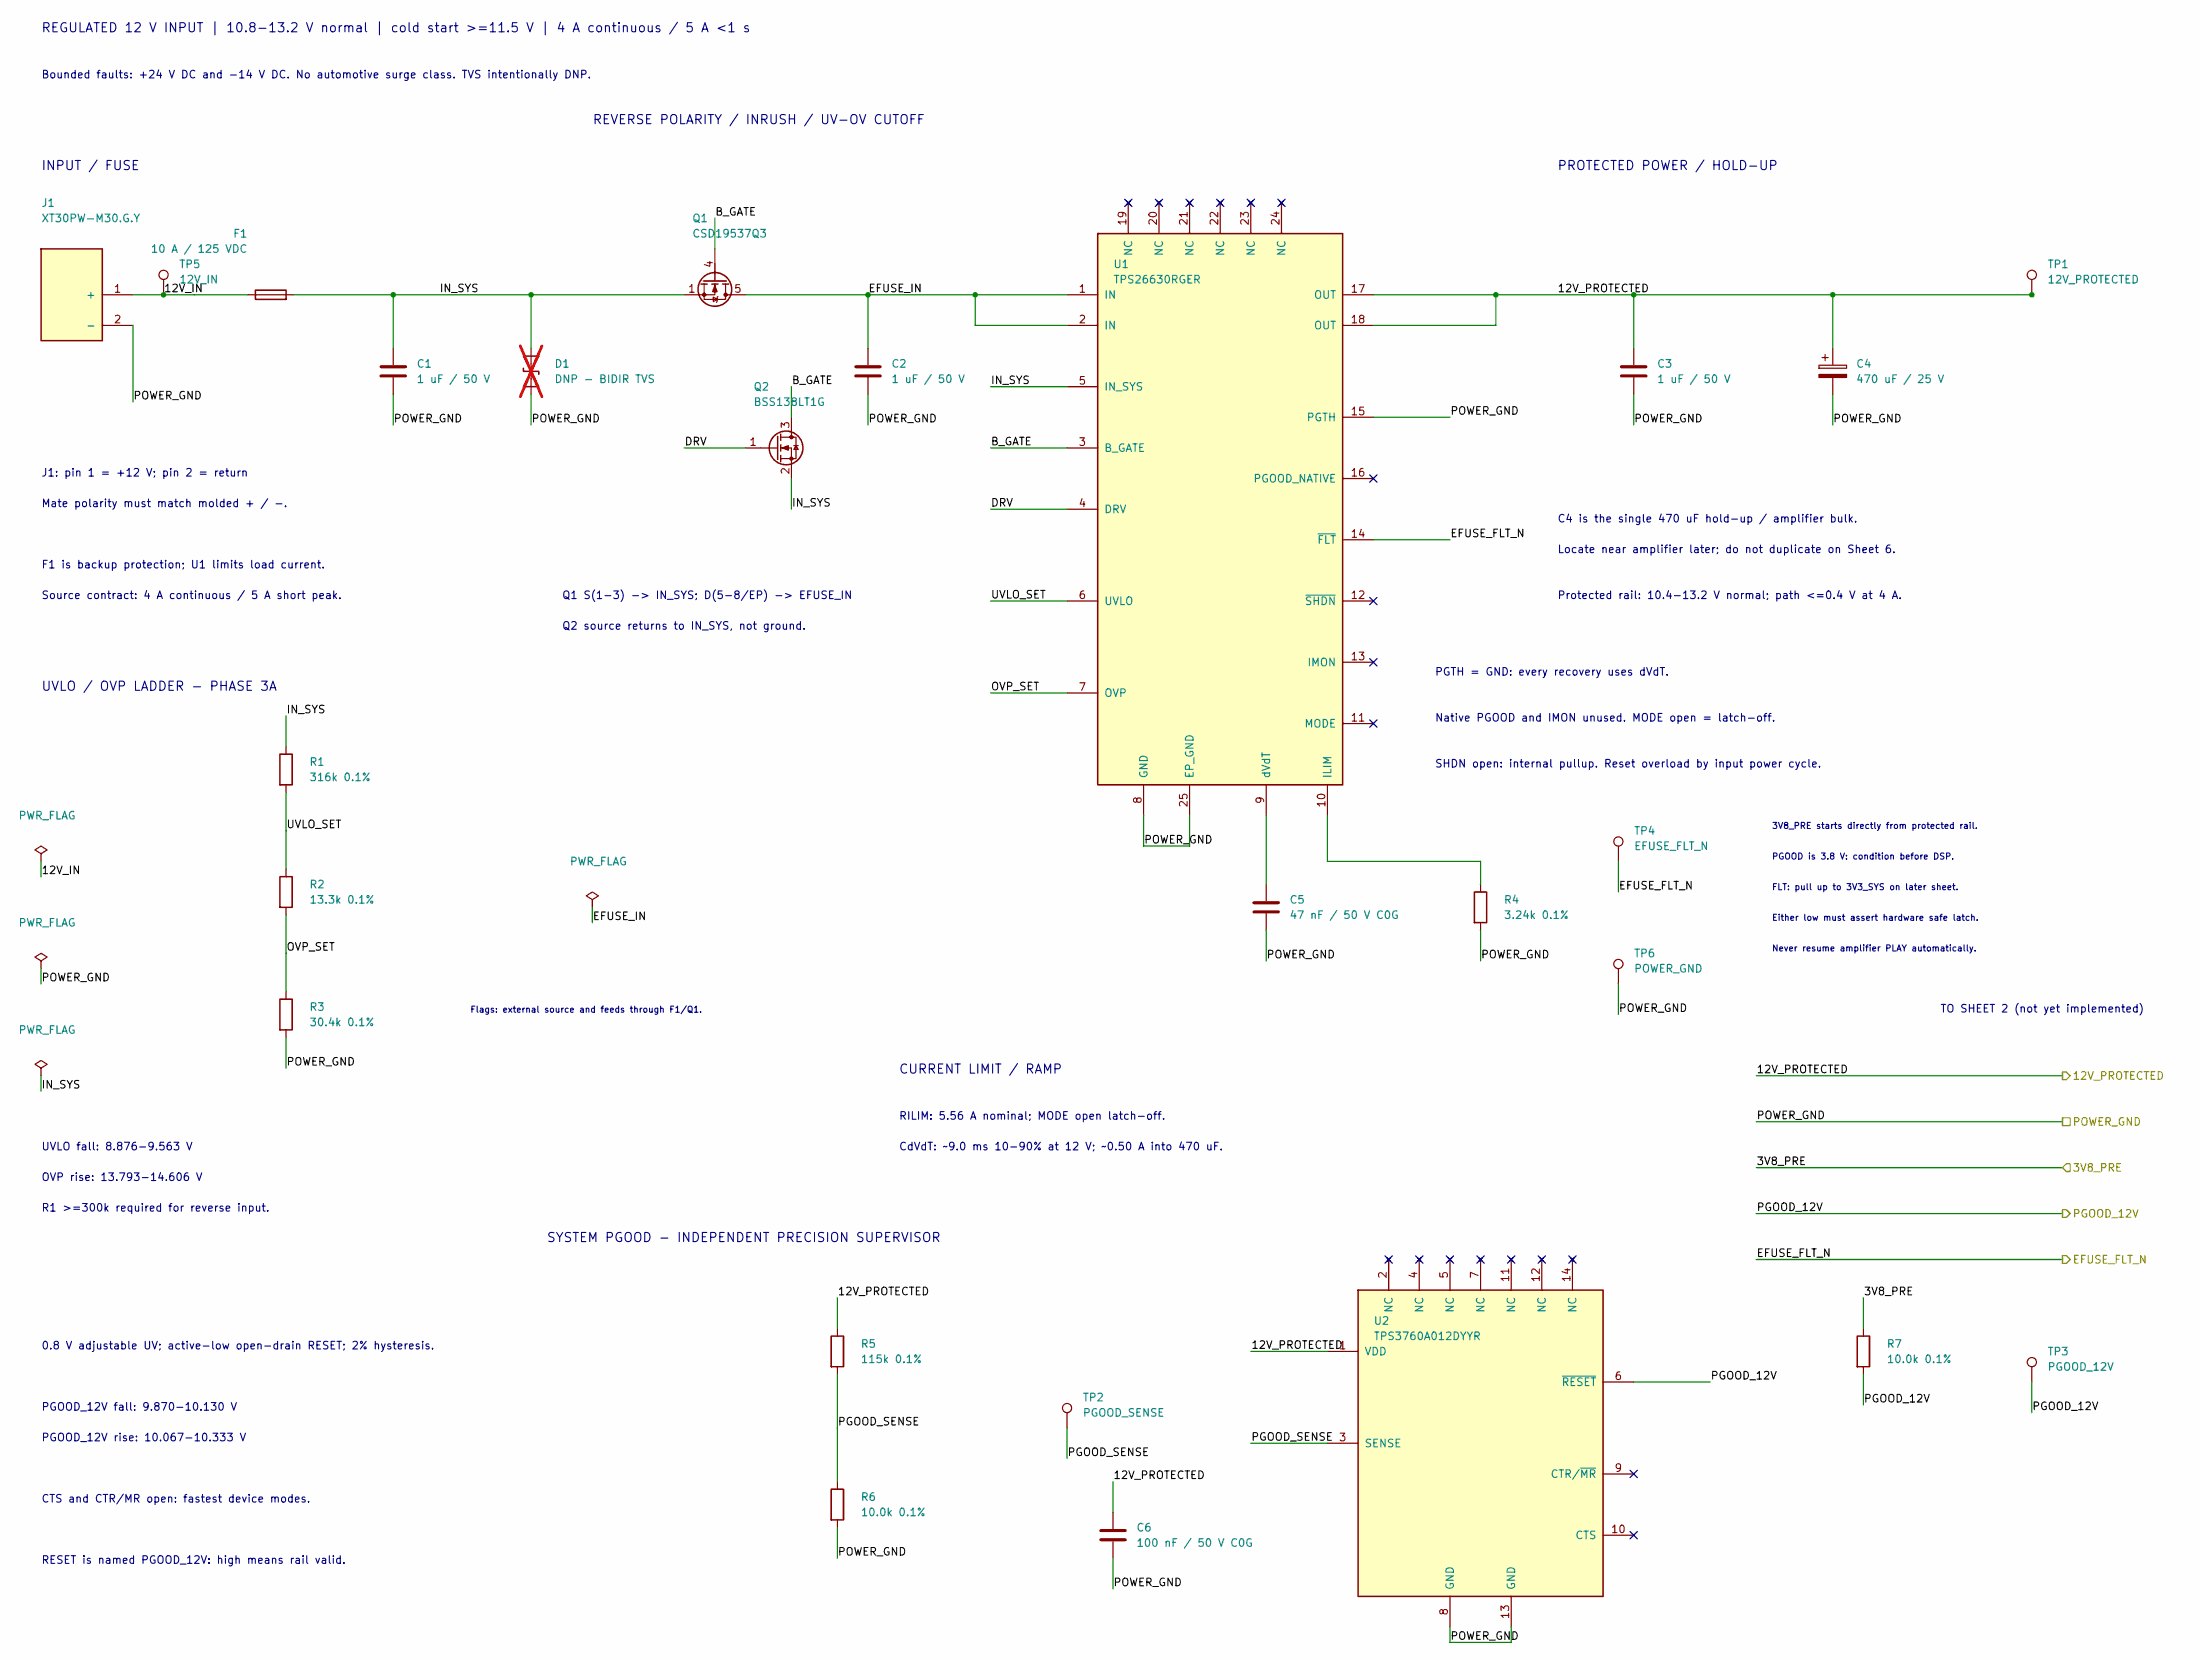
[picture p82: schematic power_input.kicad_sch]

Parts:
C1, C2, C3: 1 uF / 50 V; C_1206_3216Metric; MPN C3216X7R1H105K160AB
C4: 470 uF / 25 V; CP_Radial_D10.0mm_P5.00mm; MPN 25ZLH470MEFC10X12.5
C5: 47 nF / 50 V C0G; C_1206_3216Metric; MPN C1206C473J5GACTU
C6: 100 nF / 50 V C0G; C_1210_3225Metric; MPN C1210C104J5GACTU
D1: DNP - BIDIR TVS; D_SMC; not fitted
F1: 10 A / 125 VDC; Fuse_Littelfuse-NANO2-451_453; MPN 0451010.MRL
J1: XT30PW-M30.G.Y; MPN XT30PW-M30.G.Y
Q1: CSD19537Q3; VSON-8_3.3x3.3mm_P0.65mm_NexFET; MPN CSD19537Q3
Q2: BSS138LT1G; SOT-23; MPN BSS138LT1G
R1: 316k 0.1%; R_0805_2012Metric; MPN TNPW0805316KBYEA
R2: 13.3k 0.1%; R_0805_2012Metric; MPN TNPW080513K3BYEA
R3: 30.4k 0.1%; R_0805_2012Metric; MPN TNPW080530K4BYEA
R4: 3.24k 0.1%; R_0805_2012Metric; MPN TNPW08053K24BYEA
R5: 115k 0.1%; R_0805_2012Metric; MPN TNPW0805115KBYEA
R6, R7: 10.0k 0.1%; R_0805_2012Metric; MPN TNPW080510K0BYEA
TP1: 12V_PROTECTED; TestPoint_Pad_D2.0mm
TP2: PGOOD_SENSE; TestPoint_Pad_D2.0mm
TP3: PGOOD_12V; TestPoint_Pad_D2.0mm
TP4: EFUSE_FLT_N; TestPoint_Pad_D2.0mm
TP5: 12V_IN; TestPoint_Pad_D2.0mm
TP6: POWER_GND; TestPoint_Pad_D2.0mm
U1: TPS26630RGER; Texas_RGE0024H_VQFN-24-1EP_4x4mm_P0.5mm_EP2.7x2.7mm; MPN TPS26630RGER
U2: TPS3760A012DYYR; MPN TPS3760A012DYYR

Connections:
3V8_PRE: R7.1
12V_IN: F1.1, J1.1 (+), TP5.1
12V_PROTECTED: C3.1, C4.1, C6.1, R5.1, TP1.1, U1.17 (OUT), U1.18 (OUT), U2.1 (VDD)
B_GATE: Q1.4 (G), Q2.3 (D), U1.3 (B_GATE)
DRV: Q2.1 (G), U1.4 (DRV)
EFUSE_FLT_N: TP4.1, U1.14 (~FLT)
EFUSE_IN: C2.1, Q1.5 (D), U1.1 (IN), U1.2 (IN)
IN_SYS: C1.1, D1.1 (A1), F1.2, Q1.1 (S), Q1.2 (S), Q1.3 (S), Q2.2 (S), R1.1, U1.5 (IN_SYS)
unnamed: C5.1, U1.9 (dVdT)
unnamed: R4.1, U1.10 (ILIM)
OVP_SET: R2.2, R3.1, U1.7 (OVP)
PGOOD_12V: R7.2, TP3.1, U2.6 (~RESET)
PGOOD_SENSE: R5.2, R6.1, TP2.1, U2.3 (SENSE)
POWER_GND: C1.2, C2.2, C3.2, C4.2, C5.2, C6.2, D1.2 (A2), J1.2 (-), R3.2, R4.2, R6.2, TP6.1, U1.8 (GND), U1.15 (PGTH), U1.25 (EP_GND), U2.8 (GND), U2.13 (GND)
UVLO_SET: R1.2, R2.1, U1.6 (UVLO)

Notes on the sheet:
Source contract: 4 A continuous / 5 A short peak.
UVLO / OVP LADDER - PHASE 3A
C4 is the single 470 uF hold-up / amplifier bulk.
3V8_PRE starts directly from protected rail.
INPUT / FUSE
REVERSE POLARITY / INRUSH / UV-OV CUTOFF
Never resume amplifier PLAY automatically.
CdVdT: ~9.0 ms 10-90% at 12 V; ~0.50 A into 470 uF.
Q2 source returns to IN_SYS, not ground.
F1 is backup protection; U1 limits load current.
PGTH = GND: every recovery uses dVdT.
OVP rise: 13.793-14.606 V
J1: pin 1 = +12 V; pin 2 = return
Locate near amplifier later; do not duplicate on Sheet 6.
Q1 S(1-3) -> IN_SYS; D(5-8/EP) -> EFUSE_IN
Bounded faults: +24 V DC and -14 V DC. No automotive surge class. TVS intentionally DNP.
Flags: external source and feeds through F1/Q1.
FLT: pull up to 3V3_SYS on later sheet.
RESET is named PGOOD_12V: high means rail valid.
Mate polarity must match molded + / -.
Native PGOOD and IMON unused. MODE open = latch-off.
TO SHEET 2 (not yet implemented)
0.8 V adjustable UV; active-low open-drain RESET; 2% hysteresis.
PGOOD_12V fall: 9.870-10.130 V
R1 >=300k required for reverse input.
PGOOD is 3.8 V: condition before DSP.
PGOOD_12V rise: 10.067-10.333 V
Protected rail: 10.4-13.2 V normal; path <=0.4 V at 4 A.
SHDN open: internal pullup. Reset overload by input power cycle.
RILIM: 5.56 A nominal; MODE open latch-off.
REGULATED 12 V INPUT | 10.8-13.2 V normal | cold start >=11.5 V | 4 A continuous / 5 A <1 s
SYSTEM PGOOD - INDEPENDENT PRECISION SUPERVISOR
PROTECTED POWER / HOLD-UP
UVLO fall: 8.876-9.563 V
CTS and CTR/MR open: fastest device modes.
Either low must assert hardware safe latch.
CURRENT LIMIT / RAMP
